CatspersCoffee/S100-Boards/PIC-SPI/S10_PIC_SPI_v1.sch

## KiCad design PIC-SPI/S10_PIC_SPI_v1.sch (2016-01-09, an earlier design)

Schematic: S10_PIC_SPI_v1.sch

Parts:
C1, C2, C5, C7, C11, C12: 10 uF
C3, C4, C6, C8, C14, C17, C20, C21, C25, C27, C28: 0.1 uF
C9: 22 uF
C10, C18: 15 pF
C15: 0.01 uF
C19, C26, C33, C34, C35, C36, C37, C38, C39, C40: C
D1, D4: LED
D2: P55
D3: P54
D5: POWER
D6: DONE
D7: BOARD_SELECT
D8: POWER CH341A
D9: FLASH_0
D10: FLASH_1
D11: FLASH_2
D12: FLASH_3
JP5: JUMPER; PIN_ARRAY_2X1
JPx1, JPx2, JPx3, JPx4, JPx5, JPx6, JPx7, JPx8: JUMPER; PIN_ARRAY_2X1
Jx2: USB_2
P1: M25P80 ISP
P2, P10: CONN_4
P3, P8, P9: CONN_2
P4: S100_MALE
P5: PIC_ISP
P6, P7: CONN_1
P19: XILINX CABLE2
Q1, Q2, Q9: ^^NPN-SOT23
R1, R5, R13, R14, R15, R16, R20, R21, R22, R23, R24, R29, R45: 330
R2, R18, R19, R28, R47: 470
R3: 1K
R4, R8, R10, R11, R30: 10k
R9, R12, R17: 10K
R25, R26, R27: 100
SW1, SW2: RESET
SW4: FLASH_SELECT
SW50: FLASH/RUN
U1: LDO_REG_7805
U2: LM1086CS
U3din1, U3dout1: ^^74HC541
U4, U5, U6, U19: ^^74LS541
U8: PIC18F1330
U12: ^^74LV244
U14, U15, U16, U17: M25P80
U18: CH341A
U20: XC95288XL-TQ144
Ux1: ^^3.3VREG_SOT223
X1: 12MHz

Connections:
0V: C1.2, C2.2, C3.2, C4.2, C5.2, C6.2, C7.2, C8.2, C9.2, C10.2, C11.2, C12.2, C14.2, C15.2, C17.2, C18.2, C19.2, C20.2, C21.2, C25.2, C26.2, C27.2, C28.2, C33.2, C34.2, C35.2, C36.2, C37.2, C38.2, C39.2, C40.2, D2.2 (K), D3.2 (K), D6.2 (K), D7.2 (K), Jx2.4, P1.1, P2.1, P3.2 (PM), P4.50 (0_V2), P4.100 (0_V5), P5.3, P10.1, Q1.2 (E), Q2.2 (E), Q9.2 (E), R5.2, R9.1, R10.1, R14.2, R21.1, R22.1, R23.1, R24.1, SW1.1, SW2.2, SW4.1, SW50.1, U1.2 (GND), U2.2 (GND), U4.1 (G1), U4.19 (G2), U5.1 (G1), U5.19 (G2), U6.1 (G1), U6.19 (G2), U8.5 (VSS/AVSS), U12.10 (GND), U14.4 (GND), U15.4 (GND), U16.4 (GND), U17.4 (GND), U18.12 (GND), U18.27 (WT#), U20.18 (GND), U20.29 (GND), U20.36 (GND), U20.47 (GND), U20.62 (GND), U20.72 (GND), U20.89 (GND), U20.90 (GND), U20.99 (GND), U20.108 (GND), U20.114 (GND), U20.123 (GND), U20.144 (GND), Ux1.1 (GND)
0V_A: P4.20 (0_V1)
0V_B: P4.53 (0_V3)
0V_C: P4.70 (0_V4)
25Pxx_CS: U12.5 (O2b), U12.14 (O2a), U20.124 (P124_FB10_MC10)
25Pxx_SEL_0: U14.1 (~CS), U20.125 (P125_FB10_MC11)
25Pxx_SEL_1: U15.1 (~CS), U20.126 (P126_FB10_MC12)
25Pxx_SEL_2: U16.1 (~CS), U20.128 (P128_FB10_MC14)
25Pxx_SEL_3: U17.1 (~CS), U20.129 (P129_FB10_MC17)
25Pxx_SEL_4: U20.56 (P56_FB9_MC11)
25Pxx_SEL_5: U20.57 (P57_FB9_MC12)
25Pxx_SEL_6: U20.58 (P58_FB9_MC14)
25Pxx_SEL_7: U20.59 (P59_FB9_MC17)
+8V: C1.1, C11.1, P4.1 (+8_V), P4.51 (+8_V), U1.1 (VI), U2.1 (VI)
+16V: P4.2 (+16_V)
-16V: P4.52 (-16_V)
/M1: U20.43 (P43_FB5_MC15)
/WAITtoS100: R47.1, U20.2 (P2_FB4_MC2_I/O/GTS3)
A0: P4.79 (A0), U4.2 (A0), U20.100 (P100_FB14_MC3)
A0b: U4.18 (Y0)
A1: P4.80 (A1), U4.3 (A1), U20.101 (P101_FB14_MC5)
A1b: U4.17 (Y1)
A2: P4.81 (A2), U4.4 (A2), U20.102 (P102_FB14_MC6)
A2b: U4.16 (Y2)
A3: P4.31 (A3), U4.5 (A3), U20.103 (P103_FB14_MC8)
A3b: U4.15 (Y3)
A4: P4.30 (A4), U4.6 (A4), U20.104 (P104_FB14_MC10)
A4b: U4.14 (Y4)
A5: P4.29 (A5), U4.7 (A5), U20.105 (P105_FB14_MC11)
A5b: U4.13 (Y5)
A6: P4.82 (A6), U4.8 (A6), U20.106 (P106_FB14_MC14)
A6b: U4.12 (Y6)
A7: P4.83 (A7), U4.9 (A7), U20.107 (P107_FB14_MC15)
A7b: U4.11 (Y7)
A8: P4.84 (A8), U5.2 (A0), U20.79 (P79_FB15_MC2)
A8b: U5.18 (Y0)
A9: P4.34 (A9), U5.3 (A1), U20.80 (P80_FB15_MC3)
A9b: U5.17 (Y1)
A10: P4.37 (A10), U5.4 (A2), U20.81 (P81_FB15_MC8)
A10b: U5.16 (Y2)
A11: P4.87 (A11), U5.5 (A3), U20.82 (P82_FB15_MC10)
A11b: U5.15 (Y3)
A12: P4.33 (A12), U5.6 (A4), U20.83 (P83_FB15_MC11)
A12b: U5.14 (Y4)
A13: P4.85 (A13), U5.7 (A5), U20.85 (P85_FB15_MC12)
A13b: U5.13 (Y5)
A14: P4.86 (A14), U5.8 (A6), U20.86 (P86_FB15_MC14)
A14b: U5.12 (Y6)
A15: P4.32 (A15), U5.9 (A7), U20.87 (P87_FB15_MC15)
A15b: U5.11 (Y7)
A16: P4.16 (A16), U6.2 (A0), U20.88 (P88_FB15_MC17)
A16b: U6.18 (Y0)
A17: P4.17 (A17), U6.3 (A1), U20.91 (P91_FB16_MC2)
A17b: U6.17 (Y1)
A18: P4.15 (A18), U6.4 (A2), U20.92 (P92_FB16_MC3)
A18b: U6.16 (Y2)
A19: P4.59 (A19), U6.5 (A3), U20.93 (P93_FB16_MC5)
A19b: U6.15 (Y3)
A20: P4.61 (A20), U6.6 (A4), U20.94 (P94_FB16_MC6)
A20b: U6.14 (Y4)
A21: P4.62 (A21), U6.7 (A5), U20.95 (P95_FB16_MC8)
A21b: U6.13 (Y5)
A22: P4.63 (A22), U6.8 (A6), U20.96 (P96_FB16_MC10)
A22b: U6.12 (Y6)
A23: P4.64 (A23), U6.9 (A7), U20.97 (P97_FB16_MC11)
A23b: U6.11 (Y7)
ADSB*: P4.22 (ADSB*)
BOARD_INTERRUPT_VECTc: JPx1.2, JPx2.2, JPx3.2, JPx4.2, JPx5.2, JPx6.2, JPx7.2, JPx8.2
BOARD_SEL_LED: R20.2, U20.31 (P31_FB3_MC12)
CDSB*: P4.19 (CDSB*)
CLOCK*: P4.49 (CLOCK)
CLOCK*b: U20.53 (P53_FB9_MC6)
CPLD2_TCK: R25.1, U20.67 (TCK)
CPLD2_TDI: R26.1, U20.63 (TDI)
CPLD2_TDO: P19.8, U20.122 (TDO)
CPLD2_TMS: R27.1, U20.65 (TMS)
CPLD_4: U20.4 (P4_FB4_MC6)
CPLD_5: U20.5 (P5_FB4_MC8_I/O/GTS1)
CPLD_45: U19.2 (A0), U20.45 (P45_FB7_MC3)
CPLD_46: U19.3 (A1), U20.46 (P46_FB7_MC5)
CPLD_48: U19.4 (A2), U20.48 (P48_FB7_MC12)
CPLD_49: U19.5 (A3), U20.49 (P49_FB7_MC15)
CPLD_130: U19.6 (A4), U20.130 (P130_FB8_MC2)
CPLD_131: U19.7 (A5), U20.131 (P131_FB8_MC3)
CPLD_132: U19.8 (A6), U20.132 (P132_FB8_MC5)
CPLD_133: U19.9 (A7), U20.133 (P133_FB8_MC8)
CPLD_134: U19.1 (G1), U19.19 (G2), U20.134 (P134_FB8_MC10)
CPLD_M25P80_CLK: U12.2 (I0a), U20.135 (P135_FB6_MC2)
CPLD_M25P80_CS: U12.6 (I2a), U20.137 (P137_FB6_MC5)
CPLD_M25P80_Din: U12.4 (I1a), U20.136 (P136_FB6_MC3)
CPLD_M25P80_Dout: R9.2, U12.12 (O3a), U20.138 (P138_FB6_MC6)
D0: U3din1.18 (Y0), U3dout1.2 (A0), U19.18 (Y0), U20.9 (P9_FB2_MC2)
D1: U3din1.17 (Y1), U3dout1.3 (A1), U19.17 (Y1), U20.10 (P3_FB2_MC3)
D2: U3din1.16 (Y2), U3dout1.4 (A2), U19.16 (Y2), U20.11 (P11_FB2_MC5)
D3: U3din1.15 (Y3), U3dout1.5 (A3), U19.15 (Y3), U20.12 (P12_FB2_MC6)
D4: U3din1.14 (Y4), U3dout1.6 (A4), U19.14 (Y4), U20.13 (P13_FB2_MC8)
D5: U3din1.13 (Y5), U3dout1.7 (A5), U19.13 (Y5), U20.14 (P14_FB2_MC10)
D6: U3din1.12 (Y6), U3dout1.8 (A6), U19.12 (Y6), U20.15 (P15_FB2_MC12)
D7: U3din1.11 (Y7), U3dout1.9 (A7), U19.11 (Y7), U20.16 (P16_FB2_MC14)
DBUSIN_EN: U3din1.1 (G1), U3din1.19 (G2), U20.22 (P22_FB1_MC8)
DBUSOUT_EN: U3dout1.1 (G1), U3dout1.19 (G2), U20.21 (P21_FB1_MC6)
DI0: P4.95 (DI1_OD1), U3dout1.18 (Y0)
DI1: P4.94 (DI1_OD1), U3dout1.17 (Y1)
DI2: P4.41 (D12_OD2), U3dout1.16 (Y2)
DI3: P4.42 (D13_OD3), U3dout1.15 (Y3)
DI4: P4.91 (DI4_OD4), U3dout1.14 (Y4)
DI5: P4.92 (DI5_OD5), U3dout1.13 (Y5)
DI6: P4.93 (DI6_OD6), U3dout1.12 (Y6)
DI7: P4.43 (D17_OD7), U3dout1.11 (Y7)
DO0: P4.36 (DO0_ED0), U3din1.2 (A0)
DO1: P4.35 (DO1_ED1), U3din1.3 (A1)
DO2: P4.88 (DO2_ED2), U3din1.4 (A2)
DO3: P4.89 (DO3_ED3), U3din1.5 (A3)
DO4: P4.38 (DO4_ED4), U3din1.6 (A4)
DO5: P4.39 (DO5_ED5), U3din1.7 (A5)
DO6: P4.40 (DO6_ED6), U3din1.8 (A6)
DO7: P4.90 (DO7_ED7), U3din1.9 (A7)
DODSB*: P4.23 (DODSB*)
ERROR*: P4.98 (ERROR*)
FLASH_0: D9.1 (A), U20.71 (P71_FB13_MC2)
FLASH_1: D10.1 (A), U20.74 (P74_FB13_MC8)
FLASH_2: D11.1 (A), U20.75 (P75_FB13_MC11)
FLASH_3: D12.1 (A), U20.76 (P76_FB13_MC14)
GND: P6.1, P7.1, P19.1, P19.3, P19.5, P19.7, P19.9
HOLD*: P4.74 (HOLD*)
INT*: P4.73 (INT*)
IOREQb: P4.69 (RFU3)
IOREQbb: U20.39 (P39_FB5_MC10)
LED_D2: R13.2, U20.7 (P7_FB4_MC14)
LED_D3: R16.2, U20.6 (P6_FB4_MC12_I/O/GTS2)
M2_MCLR: P5.1, R4.2, SW2.1, U8.4 (MCLR/VPP/RA5)
M2_PGC: P5.5, U8.12 (RB6/PWM4/PGC)
M2_PGD: P5.4, U8.13 (RB7/PWM5/PGD)
MWRT: P4.68 (MWRT)
MWRTb: U20.40 (P40_FB5_MC12)
NDEF1: P4.21 (NDEF1)
NDEF2: P4.65 (NDEF2)
NDEF2b: U20.41 (P41_FB5_MC14)
NDEF3: P4.66 (NDEF3)
NMI*: P4.12 (NMI*)
unnamed: C10.1, U18.13 (XI), X1.1
unnamed: C18.1, U18.14 (XO), X1.2
unnamed: D1.1 (A), R1.1
unnamed: D1.2 (K), Q1.3 (C)
unnamed: D2.1 (A), R13.1
unnamed: D3.1 (A), R16.1
unnamed: D4.1 (A), R29.1
unnamed: D4.2 (K), Q2.3 (C)
unnamed: D5.2 (K), R5.1
unnamed: D7.1 (A), R20.1
unnamed: D8.2 (K), R14.1
unnamed: D9.2 (K), R21.2
unnamed: D10.2 (K), R22.2
unnamed: D11.2 (K), R23.2
unnamed: D12.2 (K), R24.2
unnamed: JP5.1, R45.1
unnamed: Jx2.2, U18.11 (UD-)
unnamed: Jx2.3, U18.10 (UD+)
unnamed: P2.2, U20.116 (P116_FB12_MC12)
unnamed: P2.3, U20.115 (P115_FB12_MC10)
unnamed: P2.4, U20.113 (P113_FB12_MC8)
unnamed: P3.1, R15.1
unnamed: P10.2, U20.112 (P112_FB12_MC5)
unnamed: P10.3, U20.111 (P111_FB12_MC3)
unnamed: P10.4, U20.110 (P110_FB12_MC2)
unnamed: P19.4, R27.2
unnamed: P19.6, R25.2
unnamed: P19.10, R26.2
unnamed: Q1.1 (B), R2.1, R19.1
unnamed: Q2.1 (B), R18.1, R28.1
unnamed: Q9.1 (B), R47.2
unnamed: R3.1, U14.3 (~WP), U14.7 (~HOLD), U15.3 (~WP), U15.7 (~HOLD), U16.3 (~WP), U16.7 (~HOLD), U17.3 (~WP), U17.7 (~HOLD)
unnamed: R8.2, SW1.2, U20.24 (P24_FB1_MC12)
unnamed: R11.2, SW4.2, U8.18 (RB3/INT3)
unnamed: R12.2, U12.7 (O1b), U12.16 (O1a), U14.5 (Din), U15.5 (Din), U16.5 (Din), U17.5 (Din)
unnamed: R15.2, U18.1 (ACT#)
unnamed: R17.2, U12.9 (O0b), U12.18 (O0a), U14.6 (CLK), U15.6 (CLK), U16.6 (CLK), U17.6 (CLK)
unnamed: R30.2, SW50.2, U8.17 (RB2/INT2)
unnamed: U12.8 (I3a), U12.17 (I3b), U14.2 (Dout), U15.2 (Dout), U16.2 (Dout), U17.2 (Dout)
PHANTOM*: P4.67 (PHANTOM*)
PHI: P4.24 (PHI)
PHIb: U20.54 (P54_FB9_MC8)
PIC18F_0: U8.11 (RB5/PWM3)
PIC18F_1: U8.10 (RB4/PWM2)
PIC18F_2: U8.7 (RA3/RX/DT)
POC*: P4.99 (POC*)
PROG_M25P80_CLK: P1.2, U12.11 (I0b), U18.18 (D3)
PROG_M25P80_CS: P1.4, U12.15 (I2b), U18.15 (D0)
PROG_M25P80_Din: P1.3, U12.13 (I1b), U18.20 (D5)
PROG_M25P80_Dout: P1.5, R10.2, U12.3 (O3b), U18.22 (D7)
PWRFAIL*: P4.13 (PWRFAIL*)
Q1: R2.2, R18.2, U8.9 (RB1/PWM1), U12.19 (OEb)
Q2: R19.2, R28.2, U8.8 (RB0/PWM0), U12.1 (OEa)
RDY: JP5.2, P4.72 (RDY), Q9.3 (C)
RESET*: P4.75 (RESET*)
RESET*b: U20.3 (P3_FB4_MC5_I/O/GTS4)
RFU1: P4.27 (RFU_1)
RFU2: P4.28 (RFU_2)
RFU4: P4.71 (RFU4)
SDSB*: P4.18 (SDSB*)
SIXTN*: P4.60 (SIXTN*)
SLAVE_CLR*: P4.54 (SLAVE_CLR*)
SLAVE_CLR*vv: U20.33 (P33_FB3_MC15)
SPI_CLK: U20.139 (P139_FB6_MC8)
SPI_Din: U20.140 (P140_FB6_MC10)
SPI_Dout: U20.142 (P142_FB6_MC14)
SPI_SEL_0: U20.66 (P66_FB11_MC11)
SPI_SEL_1: U20.64 (P64_FB11_MC10)
SPI_SEL_2: U20.61 (P61_FB11_MC5)
SPI_SEL_3: U20.60 (P60_FB11_MC3)
TMA0*: P4.55 (TMA0*)
TMA0_CPLD: U20.117 (P117_FB10_MC2)
TMA1*: P4.56 (TMA1*)
TMA1_CPLD: U20.118 (P118_FB10_MC3)
TMA2*: P4.57 (TMA2*)
TMA2_CPLD: U20.119 (P119_FB10_MC5)
TMA3*: P4.14 (TMA3*)
TMA3_CPLD: U20.120 (P120_FB10_MC6)
USB_VCC1: C7.1, Jx2.1, Ux1.3 (VI)
V3.3: C2.1, C4.1, C5.1, C19.1, C26.1, C33.1, C34.1, C35.1, C36.1, C37.1, C38.1, C39.1, C40.1, P8.1, P8.2 (PM), P9.1, P9.2 (PM), P19.2, R3.2, R8.1, R12.1, R17.1, U2.3 (VO), U12.20 (VCC), U14.8 (VCC), U15.8 (VCC), U16.8 (VCC), U17.8 (VCC), U20.1 (VCCIO), U20.8 (VCCINT), U20.37 (VCCIO), U20.42 (VCCINT), U20.55 (VCCIO), U20.73 (VCCIO), U20.84 (VCCINT), U20.109 (VCCIO), U20.127 (VCCIO), U20.141 (VCCINT)
V3.3b: C9.1, C14.1, C15.1, D8.1 (A), U18.9 (V3), U18.28 (VCC), Ux1.2 (VOUT)
VCC: C3.1, C6.1, C8.1, C12.1, C17.1, C20.1, C21.1, C25.1, C27.1, C28.1, D5.1 (A), P5.2, R1.2, R4.1, R11.1, R29.2, R30.1, R45.2, U1.3 (VO), U8.14 (VDD/AVDD)
VI0*: JPx1.1, P4.4 (VIO*)
VI1*: JPx2.1, P4.5 (VI1*)
VI2*: JPx3.1, P4.6 (VI2*)
VI3*: JPx4.1, P4.7 (VI3*)
VI4*: JPx5.1, P4.8 (VI4*)
VI5*: JPx6.1, P4.9 (VI5*)
VI6*: JPx7.1, P4.10 (VI6*)
VI7*: JPx8.1, P4.11 (VI7*)
XRDY: P4.3 (XRDY)
Z80intVectorBusout: U20.44 (P44_FB5_MC17)
pDBIN: P4.78 (pDBIN)
pDBINb: U20.51 (P51_FB9_MC3)
pHLDA: P4.26 (pHDLA)
pSTVAL*: P4.25 (pSTVAL*)
pSYNC: P4.76 (pSYNC)
pWR*: P4.77 (pWR*)
pWR*b: U20.50 (P50_FB9_MC2)
sHLTA: P4.48 (sHLTA)
sINP: P4.46 (sINP)
sINPb: U20.35 (P35_FB5_MC5)
sINTA: P4.96 (sINTA)
sM1: P4.44 (sM1)
sMEMR: P4.47 (sMEMR)
sMEMRb: U20.38 (P38_FB5_MC8_I/O/GCK3)
sOUT: P4.45 (sOUT)
sOUTb: U20.34 (P34_FB5_MC2)
sWO*: P4.97 (sWO*)
sWO*b: U20.52 (P52_FB9_MC5)
sXTRQ*: P4.58 (sXTRQ*)

Notes on the sheet:
XILINX CABLE HEADER 1, 3, 5, 7, 9, 11, 13 - GND 2 - VREF +3.3V 4 - TMS 6 - TCK 8 - TDO 10 - TDI 12, 14 - NC
MOUNTING HOLES
Q1 out is HIGH on PowerUp
B -> A
Pin 49 (clock line from another board) Input
Pin 47 (MEM RD) Input
Pin 45 (I/O WR) Input
INPUT from S100 BUS
Pin 69 (I/O REQUEST) Input
Pin 46 (I/O RD) Input
Pin 68 (MEM WR) Input
Pin 65 (MEM REQUEST) Input
Pin 67 (/PHANTOM) Output
Pin 75 (master reset line) Input
Pin 76 (indicates beginning of machine cycle) Output
Pin 77 (active low when processor write to I/O or MEM) Input
Pin 78 (active high when processor reads I/O or MEM) Input
Pin 79 (Address line 0) S100 Bus
ADDRESS INPUTS from S100 BUS
Pin 44 (processor Instruction Fetch Cycle M1) Input
Pin 16 (Address line 16) S100 Bus
Pin 17 (Address line 17) S100 Bus
Pin 15 (Address line 18) S100 Bus
Pin 97 (active low when processor is in Write status) Input
Pin 26 (Processor in HOLD condition) Output
Pin 27 (Processor in WAIT condition) Output
Pin 24 (Primary Processor clock line ) Input
DATA I/O from/to S100 BUS
input to CPU from S100 bus (in terms of master) OUTPUT for this board
output to S100 Bus from CPU (in terms of master) INPUT for this board
from Pin xx of CPLD
Pin 59 (Address line 19) S100 Bus
/WAIT is output from slave to Processor
SPARE CPLD PINS
TO-220
~WR
~RD
~MREQ
~IORQ
DONE
RUN
PROGRAM
Data input to processorfrom 25Pxx via 74LV244 not able to Hi-Z so is separate Data line into CPLD
Data output (from proc) to 25P80
Q2 out is LOW on PowerUp
Pin 61 (Address line 20) S100 Bus
Pin 62 (Address line 21) S100 Bus
Pin 54 (reset from another board) Input
Pin 63 (Address line 22) S100 Bus
Pin 64 (Address line 23) S100 Bus
to BOARD_SELECT LED
to U35
to U36
to U37
Input - from U35
xxxx
to U42
to U44
to U13
to U15
to FPGA
to LED's
to U71 output /WAIT to S100 BUS
to LED D3
to LED D2
reset signal input from s100 bus
from U7
from U7b
SOT233
to U
FOR RUN/FLASH
WAIT to PIN 72 S100
Active Low This board data output, CPU data input
Pin 72 (controld run/WAIT state of processor) Input
SPARES
MCP_1
MCP_2
Pin96 Input
Buffered RESET* from S100 BUS
Active Low - sINTA*b
Active Low - pDBIN**b
ALL TMA lines are high when Z80 is Bus master
Active Low Address input with I/O req
Active Low - pDBIN*b
Active Low - pDBIN*b (READ STROBE)
Data input to processorfrom other SPI devices able to Hi-Z so is separate Data line into CPLD
CPLD output Data Bus
Q2 out is LOW on PowerUp - RUN
Q1 out is HIGH on PowerUp - PROG
Q1 out is HIGH on PowerUp - PROG so this LED will be on with Q1 high Q1 high = RUN Q1 low = PROG
Texas Instruments CD74HC154M96, Decoder, Demultiplexer, 1-of-16, Inverting, 2 → 6 V, 24-Pin SOIC RS Stock No. 662-7020
to U14
to U16
to U17
output from CPLD to 74LV244 then back to 25Pxx_CS
CS line for 25Pxx SPI: output from CPLD (pin 137) to 74LV244 then back to 25Pxx_CS (pin 124), internally with a 74138 the correct 25Pxx line is selected and routed to a single 25Pxx device (CPLD pins 125, 126, 128, 129)
Signals for other onboard SPI: on separate circuit
Active High (All TMA lines High)
Active High (SINTA and Read)
Active High (SINTA and Read and All TMA Lines high (Z80))
