CatspersCoffee/S100-Boards/Z80-FPGA-SBC/SBC.sch

## KiCad design Z80-FPGA-SBC/SBC.sch (2013-09-12, an earlier design)

Schematic: SBC.sch

Parts:
C1, C5, C9, C10, C12, C14, C15, C16, C17, C18, C23, C30, C41, C42, C43, C44, C45, C46, C47, C48, C49, C50, C51, C52, C54, C55, C56, C57, C60: 0.1 uF
C2, C3, C24, C25, C26, C27, C28, C29, C32: 10 uF
C4, C6, C7, C8, C11, C13, C19, C20: 0.1 uF; C2
C31: 22 uF
C58, C59, C61, C62, C65, C66, C67, C68, C69, C70: C
D2: DIODE
D3, D4, D5, D6, D8, D9, D10: LED
J1: USB_2
JP1, JP2, JP3, JP4: JUMPER; PIN_ARRAY_2X1
K1, K6, K8, K9, K12: CONN_3
P1: PARALLEL
P2: CLK_CPU
P4: XILINX CABLE
P5: CLK_UART
P6: RESET
P7: CPLD_JTAG
P8: PF_JTAG
P9: S6_JTAG
P10: PROG_B
P14: CONN_6
P17, P18: CONN_1
P21: S100_MALE
Q1: ^^NPN-BC817-SOT323
R1: 10
R2: 10K
R3, R25, R26, R27, R29, R35, R41, R42, R43: 330
R4, R33: 1K
R9: 10K; Digikey ??
R12: 4700
R21, R23: 10k
R22, R24: 0
R30, R31, R32: 100
R34, R36: 4K7
SW1: SW_PUSH
SW3: PROG_B
U1: 16550
U2, U16: 27C080
U3: 23LC1024
U4: PAC_GHOST
U6, U17: POWER_SELECT
U7: 74LS14
U9: LDO_REG_7805
U10: LM1086CS
U11: LF25CDT
U12: LD1117DT12
U13, U14, U15, U35, U36, U37, U42, U44, U50, U51, U52, U54, U55: 74LS245
U19: 8255
U22, U46, U47, U48, U49: 74LS541
U24: Z80-CPU
U25, U27: IS61LV5128AL-SOJ32
U26: 74LS06N; 74xx-eu-DIL14
U28: FT232R
U30: XC6SLX9-TQ144
U31: CLK_FPGA1; Digikey CTX285LVCT-ND
U32: XC95288XL-TQ144
U33: XCF02S
U43, U53: 74LVC245

Connections:
0V_A: JP1.2, P21.20 (0_V1)
0V_B: JP2.2, P21.53 (0_V3)
0V_C: JP3.2, P21.70 (0_V4)
25LC_CS: P14.1, R9.1, U3.1 (CS), U30.43 (IO_L62N_D6_2)
25LC_S0: P14.4, U3.2 (SO), U30.44 (IO_L62P_D5_2)
25LC_SCK: P14.5, U3.5 (SI), U30.40 (IO_L64N_D9_2)
25LC_SI: P14.6, U3.6 (SCK), U30.41 (IO_L64P_D8_2)
+8V: C3.1, C24.1, C27.1, C28.1, P21.1 (+8_V), P21.51 (+8_V), U9.1 (VI), U10.1 (VI), U11.1 (VI), U12.3 (VI)
+16V: P21.2 (+16_V), U6.2 (IN2)
-16V: P21.52 (-16_V), U17.2 (IN2)
/BUSAK: U24.23 (BUSAK), U32.4 (P4_FB4_MC6), U50.7 (A5), U55.9 (A7)
/BUSRQ: U24.25 (BUSRQ), U43.14 (B4), U50.6 (A4)
/CS_CFG: U35.9 (A7)
/CS_PPI: U19.6 (CS), U35.6 (A4)
/CS_RAM: R22.1, U35.2 (A0)
/CS_ROM: U2.22 (CE), U35.3 (A1)
/CS_ROM_1: U16.22 (CE), U35.4 (A2)
/CS_ROM_2: R24.1, U35.5 (A3)
/CS_RTC: U35.8 (A6)
/CS_UART: U1.14 (CS2), U35.7 (A5)
/HALT: U24.18 (HALT), U32.3 (P3_FB4_MC5_I/O/GTS4), U55.8 (A6)
/INT: U24.16 (INT), U26.2, U43.17 (B1), U50.3 (A1)
/IORQ: U24.20 (IORQ), U32.31 (P31_FB3_MC12), U55.4 (A2)
/M1: U24.27 (M1), U32.28 (P28_FB3_MC2), U55.2 (A0)
/MREQ: U24.19 (MREQ), U32.30 (P30_FB3_MC10_I/O/GCK1), U55.3 (A1)
/NMI: U24.17 (NMI), U43.16 (B2), U50.4 (A2)
/RD: U1.21 (DISTR), U2.24 (OE), U16.24 (OE), U19.5 (RD), U24.21 (RD), U25.24 (OE), U27.24 (OE), U32.32 (P32_FB3_MC14_I/O/GCK2), U55.5 (A3)
/RESET: U7.4, U24.26 (RESET), U32.131 (P131_FB8_MC3), U43.15 (B3), U50.5 (A3)
/RFSH: U24.28 (REFSH), U32.2 (P2_FB4_MC2_I/O/GTS3), U55.7 (A5)
/WAIT: U24.24 (WAIT), U43.18 (B0), U50.2 (A0)
/WR: K6.3, U1.18 (/DOSTR), U19.36 (WR), U24.22 (WR), U25.29 (WE), U27.29 (WE), U32.33 (P33_FB3_MC15), U55.6 (A4)
A0: U1.28 (A0), U2.12 (A0), U16.12 (A0), U19.9 (A0), U24.30 (A0), U25.12 (A0), U27.12 (A0), U32.100 (P100_FB14_MC3), U46.2 (A0), U51.2 (A0)
A0b: P21.79 (A0), U46.18 (Y0)
A1: U1.27 (A1), U2.11 (A1), U16.11 (A1), U19.8 (A1), U24.31 (A1), U25.11 (A1), U27.11 (A1), U32.101 (P101_FB14_MC5), U46.3 (A1), U51.3 (A1)
A1b: P21.80 (A1), U46.17 (Y1)
A2: U1.26 (A2), U2.10 (A2), U16.10 (A2), U24.32 (A2), U25.10 (A2), U27.10 (A2), U32.102 (P102_FB14_MC6), U46.4 (A2), U51.4 (A2)
A2b: P21.81 (A2), U46.16 (Y2)
A3: U2.9 (A3), U16.9 (A3), U24.33 (A3), U25.9 (A3), U27.9 (A3), U32.103 (P103_FB14_MC8), U46.5 (A3), U51.5 (A3)
A3b: P21.31 (A3), U46.15 (Y3)
A4: U2.8 (A4), U16.8 (A4), U24.34 (A4), U25.8 (A4), U27.8 (A4), U32.104 (P104_FB14_MC10), U46.6 (A4), U51.6 (A4)
A4b: P21.30 (A4), U46.14 (Y4)
A5: U2.7 (A5), U16.7 (A5), U24.35 (A5), U25.7 (A5), U27.7 (A5), U32.105 (P105_FB14_MC11), U46.7 (A5), U51.7 (A5)
A5b: P21.29 (A5), U46.13 (Y5)
A6: U2.6 (A6), U16.6 (A6), U24.36 (A6), U25.6 (A6), U27.6 (A6), U32.106 (P106_FB14_MC14), U46.8 (A6), U51.8 (A6)
A6b: P21.82 (A6), U46.12 (Y6)
A7: U2.5 (A7), U16.5 (A7), U24.37 (A7), U25.5 (A7), U27.5 (A7), U32.107 (P107_FB14_MC15), U46.9 (A7), U51.9 (A7)
A7b: P21.83 (A7), U46.11 (Y7)
A8: U2.27 (A8), U16.27 (A8), U24.38 (A8), U25.27 (A8), U27.27 (A8), U32.79 (P79_FB15_MC2), U47.2 (A0), U52.2 (A0)
A8b: P21.84 (A8), U47.18 (Y0)
A9: U2.26 (A9), U16.26 (A9), U24.39 (A9), U25.26 (A9), U27.26 (A9), U32.80 (P80_FB15_MC3), U47.3 (A1), U52.3 (A1)
A9b: P21.34 (A9), U47.17 (Y1)
A10: U2.23 (A10), U16.23 (A10), U24.40 (A10), U25.23 (A10), U27.23 (A10), U32.81 (P81_FB15_MC8), U47.4 (A2), U52.4 (A2)
A10b: P21.37 (A10), U47.16 (Y2)
A11: U2.25 (A11), U16.25 (A11), U24.1 (A11), U25.25 (A11), U27.25 (A11), U32.82 (P82_FB15_MC10), U47.5 (A3), U52.5 (A3)
A11b: P21.87 (A11), U47.15 (Y3)
A12: U2.4 (A12), U16.4 (A12), U24.2 (A12), U25.4 (A12), U27.4 (A12), U32.83 (P83_FB15_MC11), U47.6 (A4), U52.6 (A4)
A12b: P21.33 (A12), U47.14 (Y4)
A13: U2.28 (A13), U16.28 (A13), U24.3 (A13), U25.28 (A13), U27.28 (A13), U32.85 (P85_FB15_MC12), U47.7 (A5), U52.7 (A5)
A13b: P21.85 (A13), U47.13 (Y5)
A14: U2.29 (A14), U16.29 (A14), U24.4 (A14), U25.3 (A14), U27.3 (A14), U32.86 (P86_FB15_MC14), U47.8 (A6), U52.8 (A6)
A14b: P21.86 (A14), U47.12 (Y6)
A15: U24.5 (A15), U32.87 (P87_FB15_MC15), U47.9 (A7), U52.9 (A7)
A15_RAM: U25.31 (A15), U36.7 (A5)
A15_RAM_3: U27.31 (A15), U37.3 (A1)
A15_ROM: U2.3 (A15), U16.3 (A15), U36.2 (A0)
A15b: P21.32 (A15), U47.11 (Y7)
A16_RAM: U25.2 (A16), U36.8 (A6), U48.2 (A0)
A16_RAM_3: U27.2 (A16), U37.4 (A2)
A16_ROM: U2.2 (A16), U16.2 (A16), U36.3 (A1)
A16b: P21.16 (A16), U48.18 (Y0)
A17_RAM: U25.1 (A17), U36.9 (A7), U48.3 (A1)
A17_RAM_3: U27.1 (A17), U37.5 (A3)
A17_ROM: K1.1, U36.4 (A2)
A17b: P21.17 (A17), U48.17 (Y1)
A18_RAM: U25.30 (A18), U37.2 (A0), U48.4 (A2)
A18_RAM_3: U27.30 (A18), U37.6 (A4)
A18_ROM: K6.1, K8.3, U36.5 (A3)
A18b: P21.15 (A18), U48.16 (Y2)
A19_ROM: K8.1, U36.6 (A4)
ADSB*: P21.22 (ADSB*)
B_/INT: K12.1, U26.13
CDSB*: P21.19 (CDSB*)
CLK_CPU: P2.8, U13.11 (B7), U24.6 (CLK), U43.11 (B7)
CLK_CPU2: U15.8 (A6)
CLK_UART: P5.5, U1.16 (XTAL1(I))
CLOCK2: P21.59 (A19), U15.12 (B6)
CLOCK*: P21.49 (CLOCK), U13.9 (A7)
CPLD1_TDI: P7.3, U32.63 (TDI)
CPLD1_TDO: P7.1, U32.122 (TDO)
CPLD_20: U14.9 (A7), U32.20 (P20_FB1_MC5)
CPLD_21: U14.8 (A6), U32.21 (P21_FB1_MC6)
CPLD_22: U14.7 (A5), U32.22 (P22_FB1_MC8)
CPLD_23: U14.6 (A4), U32.23 (P23_FB1_MC10)
CPLD_24: U14.5 (A3), U32.24 (P24_FB1_MC12)
CPLD_25: U14.4 (A2), U32.25 (P25_FB1_MC14)
CPLD_26: U14.3 (A1), U32.26 (P26_FB1_MC15)
CPLD_27: U14.2 (A0), U32.27 (P27_FB1_MC17)
CPLD_39: U32.39 (P39_FB5_MC10), U42.18 (B0)
CPLD_40: U32.40 (P40_FB5_MC12), U42.17 (B1)
CPLD_41: U32.41 (P41_FB5_MC14), U42.16 (B2)
CPLD_43: U32.43 (P43_FB5_MC15), U42.15 (B3)
CPLD_44: U32.44 (P44_FB5_MC17), U42.14 (B4)
CPLD_45: U32.45 (P45_FB7_MC3), U42.13 (B5)
CPLD_46: U32.46 (P46_FB7_MC5), U42.12 (B6)
CPLD_48: U32.48 (P48_FB7_MC12), U42.11 (B7)
CPLD_49: U32.49 (P49_FB7_MC15)
CPLD_50: U32.50 (P50_FB9_MC2)
CPLD_51: U15.6 (A4), U32.51 (P51_FB9_MC3)
CPLD_52: U15.5 (A3), U32.52 (P52_FB9_MC5)
CPLD_53: U15.4 (A2), U32.53 (P53_FB9_MC6)
CPLD_54: U15.3 (A1), U32.54 (P54_FB9_MC8)
CPLD_56: U15.2 (A0), U32.56 (P56_FB9_MC11)
CPLD_57: U13.17 (B1), U32.57 (P57_FB9_MC12)
CPLD_58: U13.18 (B0), U32.58 (P58_FB9_MC14)
CPLD_59: U32.59 (P59_FB9_MC17)
CPLD_60: U32.60 (P60_FB11_MC3), U36.14 (B4)
CPLD_61: U32.61 (P61_FB11_MC5), U36.15 (B3)
CPLD_64: U32.64 (P64_FB11_MC10), U36.16 (B2)
CPLD_66: U32.66 (P66_FB11_MC11), U36.17 (B1)
CPLD_68: U32.68 (P68_FB11_MC12), U36.18 (B0)
CPLD_69: U32.69 (P69_FB11_MC14), U35.11 (B7)
CPLD_70: U32.70 (P70_FB11_MC17), U35.12 (B6)
CPLD_71: R41.1, U32.71 (P71_FB13_MC2)
CPLD_74: R42.1, U32.74 (P74_FB13_MC8)
CPLD_75: R43.1, U32.75 (P75_FB13_MC11)
CPLD_76: U32.76 (P76_FB13_MC14), U37.11 (B7)
CPLD_77: U32.77 (P77_FB13_MC15), U37.12 (B6)
CPLD_78: U32.78 (P78_FB13_MC17), U37.13 (B5)
CPLD_91: U32.91 (P91_FB16_MC2), U36.13 (B5)
CPLD_92: U32.92 (P92_FB16_MC3), U36.12 (B6)
CPLD_93: U32.93 (P93_FB16_MC5), U36.11 (B7)
CPLD_94: U32.94 (P94_FB16_MC6), U37.18 (B0)
CPLD_95: U32.95 (P95_FB16_MC8), U37.17 (B1)
CPLD_96: U32.96 (P96_FB16_MC10), U37.16 (B2)
CPLD_97: U32.97 (P97_FB16_MC11), U37.15 (B3)
CPLD_98: U32.98 (P98_FB16_MC12), U37.14 (B4)
CPLD_110: U32.110 (P110_FB12_MC2), U35.13 (B5)
CPLD_111: U32.111 (P111_FB12_MC3), U35.14 (B4)
CPLD_112: U32.112 (P112_FB12_MC5), U35.15 (B3)
CPLD_113: U32.113 (P113_FB12_MC8), U35.16 (B2)
CPLD_115: U32.115 (P115_FB12_MC10), U35.17 (B1)
CPLD_116: U32.116 (P116_FB12_MC12), U35.18 (B0)
CPLD_117: U32.117 (P117_FB10_MC2), U44.12 (B6)
CPLD_118: U32.118 (P118_FB10_MC3), U44.13 (B5)
CPLD_119: U32.119 (P119_FB10_MC5), U44.14 (B4)
CPLD_120: U32.120 (P120_FB10_MC6), U44.15 (B3)
CPLD_121: U32.121 (P121_FB10_MC8), U44.16 (B2)
CPLD_124: U32.124 (P124_FB10_MC10), U44.17 (B1)
CPLD_125: U32.125 (P125_FB10_MC11), U44.18 (B0)
CPLD_126: U32.126 (P126_FB10_MC12)
CPLD_128: U32.128 (P128_FB10_MC14)
CPLD_129: U32.129 (P129_FB10_MC17)
CPLD_130: U32.130 (P130_FB8_MC2)
CTS_TTL: U1.36 (CTS), U28.11 (CTS#)
D0: U1.1 (D0), U2.13 (D0), U16.13 (D0), U19.34 (D0), U22.18 (Y0), U24.14 (D0), U25.13 (I/O_0), U27.13 (I/O_0), U32.9 (P9_FB2_MC2), U32.17 (P17_FB2_MC15), U49.2 (A0), U53.18 (B0), U54.2 (A0)
D1: U1.2 (D1), U2.14 (D1), U16.14 (D1), U19.33 (D1), U22.17 (Y1), U24.15 (D1), U25.14 (I/O_1), U27.14 (I/O_1), U32.10 (P3_FB2_MC3), U32.19 (P19_FB2_MC17), U49.3 (A1), U53.17 (B1), U54.3 (A1)
D2: U1.3 (D2), U2.15 (D2), U16.15 (D2), U19.32 (D2), U22.16 (Y2), U24.12 (D2), U25.15 (I/O_2), U27.15 (I/O_2), U32.11 (P11_FB2_MC5), U49.4 (A2), U53.16 (B2), U54.4 (A2)
D3: U1.4 (D3), U2.17 (D3), U16.17 (D3), U19.31 (D3), U22.15 (Y3), U24.8 (D3), U25.17 (I/O_3), U27.17 (I/O_3), U32.12 (P12_FB2_MC6), U49.5 (A3), U53.15 (B3), U54.5 (A3)
D4: U1.5 (D4), U2.18 (D4), U16.18 (D4), U19.30 (D4), U22.14 (Y4), U24.7 (D4), U25.18 (I/O_4), U27.18 (I/O_4), U32.13 (P13_FB2_MC8), U49.6 (A4), U53.14 (B4), U54.6 (A4)
D5: U1.6 (D5), U2.19 (D5), U16.19 (D5), U19.29 (D5), U22.13 (Y5), U24.9 (D5), U25.19 (I/O_5), U27.19 (I/O_5), U32.14 (P14_FB2_MC10), U49.7 (A5), U53.13 (B5), U54.7 (A5)
D6: U1.7 (D6), U2.20 (D6), U16.20 (D6), U19.28 (D6), U22.12 (Y6), U24.10 (D6), U25.20 (I/O_6), U27.20 (I/O_6), U32.15 (P15_FB2_MC12), U49.8 (A6), U53.12 (B6), U54.8 (A6)
D7: U1.8 (D7), U2.21 (D7), U16.21 (D7), U19.27 (D7), U22.11 (Y7), U24.13 (D7), U25.21 (I/O_7), U27.21 (I/O_7), U32.16 (P16_FB2_MC14), U49.9 (A7), U53.11 (B7), U54.9 (A7)
DBUSIN_EN: U22.1 (G1), U22.19 (G2), U32.132 (P132_FB8_MC5)
DBUSOUT_EN: U32.133 (P133_FB8_MC8), U49.1 (G1), U49.19 (G2)
DI0b: P21.95 (DI1_OD1), U49.18 (Y0)
DI1b: P21.94 (DI1_OD1), U49.17 (Y1)
DI2b: P21.41 (D12_OD2), U49.16 (Y2)
DI3b: P21.42 (D13_OD3), U49.15 (Y3)
DI4b: P21.91 (DI4_OD4), U49.14 (Y4)
DI5b: P21.92 (DI5_OD5), U49.13 (Y5)
DI6b: P21.93 (DI6_OD6), U49.12 (Y6)
DI7b: P21.43 (D17_OD7), U49.11 (Y7)
DO0b: P21.36 (DO0_ED0), U22.2 (A0)
DO1b: P21.35 (DO1_ED1), U22.3 (A1)
DO2b: P21.88 (DO2_ED2), U22.4 (A2)
DO3b: P21.89 (DO3_ED3), U22.5 (A3)
DO4b: P21.38 (DO4_ED4), U22.6 (A4)
DO5b: P21.39 (DO5_ED5), U22.7 (A5)
DO6b: P21.40 (DO6_ED6), U22.8 (A6)
DO7b: P21.90 (DO7_ED7), U22.9 (A7)
DODSB*: P21.23 (DODSB*)
DSR_TTL: U1.37 (DSR), U28.9 (DSR#)
DTR_TTL: U1.33 (DTR), U28.2 (DTR#)
ERROR*: P21.98 (ERROR*)
FPGA_2: U30.2 (IO_L83P_3)
FPGA_5: U30.5 (IO_L52N_3)
FPGA_6: U30.6 (IO_L52P_3)
FPGA_7: U30.7 (IO_L51N_3)
FPGA_8: U30.8 (IO_L51P_3)
FPGA_9: U30.9 (IO_L50N_3)
FPGA_10: U30.10 (IO_L50P_3)
FPGA_11: U30.11 (IO_L49N_3)
FPGA_12: U30.12 (IO_L49P_3)
FPGA_14: U30.14 (IO_L44N_GCLK20_3)
FPGA_15: U30.15 (IO_L44P_GCLK21_3)
FPGA_16: U30.16 (IO_L43N_GCLK22_IRDY2_3)
FPGA_17: U30.17 (IO_L43P_GCLK23_3)
FPGA_21: U30.21 (IO_L42N_GCLK24_3)
FPGA_22: U30.22 (IO_L42P_GCLK25_TRDY2_3)
FPGA_23: U30.23 (IO_L41N_GCLK26_3)
FPGA_24: U30.24 (IO_L41P_GCLK27_3)
FPGA_26: U30.26 (IO_L37N_3), U32.143 (P143_FB6_MC15_I/O/GSR)
FPGA_27: U30.27 (IO_L37P_3), U32.142 (P142_FB6_MC14)
FPGA_29: U30.29 (IO_L36N_3), U32.140 (P140_FB6_MC10)
FPGA_30: U30.30 (IO_L36P_3), U32.139 (P139_FB6_MC8)
FPGA_32: U30.32 (IO_L2N_3), U32.138 (P138_FB6_MC6)
FPGA_33: U30.33 (IO_L2P_3), U32.137 (P137_FB6_MC5)
FPGA_34: U30.34 (IO_L1N_VREF_3), U32.136 (P136_FB6_MC3)
FPGA_35: U30.35 (IO_L1P_3), U32.135 (P135_FB6_MC2)
FPGA_45: U30.45 (IO_L49N_D4_2)
FPGA_46: U30.46 (IO_L49P_D3_2)
FPGA_48: U30.48 (IO_L48P_D7_2)
FPGA_55: U30.55 (IO_L30N_GCLK0_USERCCLK_2)
FPGA_56: U30.56 (IO_L30P_GCLK1_D13_2)
FPGA_57: U30.57 (IO_L14N_D12_2)
FPGA_58: U30.58 (IO_L14P_D11_2)
FPGA_59: U30.59 (IO_L13N_D10_2)
FPGA_84: U30.84 (IO_L43N_GCLK4_1), U43.8 (A6)
FPGA_87: U30.87 (IO_L42N_GCLK6_TRDY1_1), U43.7 (A5)
FPGA_88: U30.88 (IO_L42P_GCLK7_1), U43.6 (A4)
FPGA_92: U30.92 (IO_L41N_GCLK8_1), U43.5 (A3)
FPGA_93: U30.93 (IO_L41P_GCLK9_IRDY1_1), U43.4 (A2)
FPGA_94: U30.94 (IO_L40N_GCLK10_1), U43.3 (A1)
FPGA_95: U30.95 (IO_L40P_GCLK11_1), U43.2 (A0)
FPGA_97: U30.97 (IO_L34N_1), U55.11 (B7)
FPGA_98: U30.98 (IO_L34P_1), U55.12 (B6)
FPGA_99: U30.99 (IO_L33N_1), U55.13 (B5)
FPGA_100: U30.100 (IO_L33P_1), U55.14 (B4)
FPGA_101: U30.101 (IO_L32N_1), U55.15 (B3)
FPGA_102: U30.102 (IO_L32P_1), U55.16 (B2)
FPGA_104: U30.104 (IO_L1N_VREF_1), U55.17 (B1)
FPGA_105: U30.105 (IO_L1P_1), U55.18 (B0)
FPGA_111: U30.111 (IO_L66N_SCP0_0), U53.9 (A7), U54.11 (B7)
FPGA_112: U30.112 (IO_L66P_SCP1_0), U53.8 (A6), U54.12 (B6)
FPGA_114: U30.114 (IO_L65N_SCP2_0), U53.7 (A5), U54.13 (B5)
FPGA_115: U30.115 (IO_L65P_SCP3_0), U53.6 (A4), U54.14 (B4)
FPGA_116: U30.116 (IO_L64N_SCP4_0), U53.5 (A3), U54.15 (B3)
FPGA_117: U30.117 (IO_L64P_SCP5_0), U53.4 (A2), U54.16 (B2)
FPGA_118: U30.118 (IO_L63N_SCP6_0), U53.3 (A1), U54.17 (B1)
FPGA_119: U30.119 (IO_L63P_SCP7_0), U53.2 (A0), U54.18 (B0)
FPGA_120: U30.120 (IO_L62N_VREF_0), U52.11 (B7)
FPGA_121: U30.121 (IO_L62P_0), U52.12 (B6)
FPGA_123: U30.123 (IO_L37N_GCLK12_0), U52.13 (B5)
FPGA_124: U30.124 (IO_L37P_GCLK13_0), U52.14 (B4)
FPGA_126: U30.126 (IO_L36N_GCLK14_0), U52.15 (B3)
FPGA_127: U30.127 (IO_L36P_GCLK15_0), U52.16 (B2)
FPGA_131: U30.131 (IO_L35N_GCLK16_0), U52.17 (B1)
FPGA_132: U30.132 (IO_L35P_GCLK17_0), U52.18 (B0)
FPGA_133: U30.133 (IO_L34N_GCLK18_0), U51.11 (B7)
FPGA_134: U30.134 (IO_L34P_GCLK19_0), U51.12 (B6)
FPGA_137: U30.137 (IO_L4N_0), U51.13 (B5)
FPGA_138: U30.138 (IO_L4P_0), U51.14 (B4)
FPGA_139: U30.139 (IO_L3N_0), U51.15 (B3)
FPGA_140: U30.140 (IO_L3P_0), U51.16 (B2)
FPGA_141: U30.141 (IO_L2N_0), U51.17 (B1)
FPGA_142: U30.142 (IO_L2P_0), U51.18 (B0)
FPGA_CLK_0: U30.51 (IO_L31P_GCLK31_D14_2), U31.3 (OUT)
FPGA_CLK_2: U30.50 (IO_L31N_GCLK30_D15_2), U43.9 (A7)
GND: C1.2, C2.2, C3.2, C4.2, C5.2, C6.2, C7.2, C8.2, C9.2, C10.2, C11.2, C12.2, C13.2, C14.2, C15.2, C16.2, C17.2, C18.2, C19.2, C20.2, C23.2, C24.2, C25.2, C26.2, C27.2, C28.2, C29.2, C30.2, C31.2, C32.2, C41.2, C42.2, C43.2, C44.2, C45.2, C46.2, C47.2, C48.2, C49.2, C50.2, C51.2, C52.2, C54.2, C55.2, C56.2, C57.2, C58.2, C59.2, C60.2, C61.2, C62.2, C65.2, C66.2, C67.2, C68.2, C69.2, C70.2, D3.2 (K), D8.2 (K), D9.2 (K), D10.2 (K), J1.4, JP1.1, JP2.1, JP3.1, JP4.2, K9.1, P1.26 (P22), P2.7, P4.1, P4.3, P4.5, P4.7, P4.9, P5.4, P6.1, P10.2 (PM), P14.3, P17.1, P18.1, P21.50 (0_V2), P21.100 (0_V5), Q1.2 (E), SW1.1, SW3.1, U1.19 (DOSTR), U1.22 (/DISTR), U1.25 (ADS), U3.4 (VSS), U9.2 (GND), U10.2 (GND), U11.2 (GND), U12.1 (GND), U24.29 (VSS), U25.16 (GND), U27.16 (GND), U28.7 (GND), U28.18 (GND), U28.21 (GND), U28.25 (AGND), U28.26 (TEST), U30.3 (GND), U30.13 (GND), U30.25 (GND), U30.49 (GND), U30.54 (GND), U30.60 (IO_L13P_M1_2), U30.68 (GND), U30.73 (SUSPEND), U30.77 (GND), U30.91 (GND), U30.96 (GND), U30.108 (GND), U30.113 (GND), U30.130 (GND), U30.136 (GND), U31.2 (GND), U32.18 (GND), U32.29 (GND), U32.36 (GND), U32.47 (GND), U32.62 (GND), U32.72 (GND), U32.89 (GND), U32.90 (GND), U32.99 (GND), U32.108 (GND), U32.114 (GND), U32.123 (GND), U32.144 (GND), U33.11 (GND), U35.1 (A->B), U35.19 (CE), U36.1 (A->B), U36.19 (CE), U37.1 (A->B), U37.19 (CE), U43.1 (DIR), U43.10 (GND), U50.1 (A->B), U50.19 (CE), U53.10 (GND)
HOLD*: P21.74 (HOLD*), U15.16 (B2)
INT: U1.30 (IRQ), U26.3
INT*: P21.73 (INT*), U15.17 (B1)
IOREQ: U32.134 (P134_FB8_MC10), U48.9 (A7)
IOREQb: P21.63 (A22), U42.6 (A4), U48.11 (Y7)
MWRT: P21.68 (MWRT), U42.7 (A5), U44.3 (A1)
NC_A23: K12.3, R12.2
NDEF1: P21.21 (NDEF1), U15.14 (B4)
NDEF2: P21.65 (NDEF2), U42.8 (A6)
NDEF3: P21.66 (NDEF3), U42.9 (A7)
NMI*: P21.12 (NMI*), U14.18 (B0)
unnamed: C2.1, D2.1 (A), R1.1, R2.2, U7.1
unnamed: D3.1 (A), R3.2
unnamed: D4.1 (A), R25.2
unnamed: D4.2 (K), U28.23 (CBUS0)
unnamed: D5.1 (A), R26.2
unnamed: D5.2 (K), U28.22 (CBUS1)
unnamed: D6.1 (A), R27.2
unnamed: D6.2 (K), Q1.3 (C)
unnamed: D8.1 (A), R41.2
unnamed: D9.1 (A), R42.2
unnamed: D10.1 (A), R43.2
unnamed: J1.2, U28.16 (USBDM_D-)
unnamed: J1.3, U28.15 (USBDP_D+)
unnamed: K1.2 (PM), U2.30 (A17), U16.30 (A17)
unnamed: K6.2 (PM), U2.31 (A18), U16.31 (A18)
unnamed: K8.2 (PM), U2.1 (A19), U16.1 (A19)
unnamed: K12.2 (PM), U26.4
unnamed: P4.4, R32.2
unnamed: P4.6, R30.2
unnamed: P4.8, P7.2
unnamed: P4.10, R31.2
unnamed: P6.2 (PM), R1.2, SW1.2
unnamed: P7.4, P8.2
unnamed: P8.4, P9.2
unnamed: P9.4, R31.1
unnamed: P10.1, R34.2, SW3.2, U30.37 (PROGRAM_B_2), U33.7 (CF)
unnamed: Q1.1 (B), R29.1
unnamed: R21.2, R22.2, U25.22 (CE)
unnamed: R23.2, R24.2, U27.22 (CE)
unnamed: R29.2, R35.2, U30.71 (DONE_2), U33.10 (CE)
unnamed: R33.1, U31.1 (OE/StandBy)
unnamed: R36.2, U30.39 (IO_L65P_INIT_B_2), U33.8 (OE/RST)
unnamed: U1.9 (RCLK), U1.15 (BAUDOUT)
unnamed: U6.1 (IN1), U9.3 (VO)
unnamed: U10.3 (VO), U17.1 (IN1)
unnamed: U26.1, U26.12
unnamed: U30.65 (IO_L3P_D0_DIN_MISO_MISO1_2), U33.1 (DATA_(D0))
unnamed: U30.70 (IO_L1P_CCLK_2), U33.3 (CLK)
unnamed: U32.5 (P5_FB4_MC8_I/O/GTS1), U50.18 (B0)
unnamed: U32.6 (P6_FB4_MC12_I/O/GTS2), U50.17 (B1)
unnamed: U32.7 (P7_FB4_MC14), U50.16 (B2)
unnamed: U32.34 (P34_FB5_MC2), U50.15 (B3)
unnamed: U32.35 (P35_FB5_MC5), U50.14 (B4)
unnamed: U32.38 (P38_FB5_MC8_I/O/GCK3), U50.13 (B5)
PA0: P1.2, U19.4 (PA0)
PA1: P1.4, U19.3 (PA1)
PA2: P1.6, U19.2 (PA2)
PA3: P1.8, U19.1 (PA3)
PA4: P1.10, U19.40 (PA4)
PA5: P1.12, U19.39 (PA5)
PA6: P1.14, U19.38 (PA6)
PA7: P1.16, U19.37 (PA7)
PB0: P1.18, U19.18 (PB0)
PB1: P1.20, U19.19 (PB1)
PB2: P1.22, U19.20 (PB2)
PB3: P1.24 (P20), U19.21 (PB3)
PB4: P1.23, U19.22 (PB4)
PB5: P1.21, U19.23 (PB5)
PB6: P1.19, U19.24 (PB6)
PB7: P1.17, U19.25 (PB7)
PC0: P1.1, U19.14 (PC0)
PC1: P1.3, U19.15 (PC1)
PC2: P1.5, U19.16 (PC2)
PC3: P1.7, U19.17 (PC3)
PC4: P1.9, U19.13 (PC4)
PC5: P1.11, U19.12 (PC5)
PC6: P1.13, U19.11 (PC6)
PC7: P1.15, U19.10 (PC7)
PF1_TDI: P8.3, U33.4 (TDI)
PF1_TDO: P8.1, U33.17 (TDO)
PHANTOM*: P21.67 (PHANTOM*), U44.2 (A0)
PHI: P21.24 (PHI), U15.11 (B7)
PHI_CLOCK: U15.9 (A7)
POC*: P21.99 (POC*)
PPWR: K9.2 (PM), P1.25 (P24)
PWRFAIL*: P21.13 (PWRFAIL*)
RDY: P21.72 (RDY), U15.18 (B0)
RESET: U1.35 (MR), U7.2, U7.3, U19.35 (RESET)
RESET*: P21.75 (RESET*), U15.15 (B3)
RFU1: P21.27 (RFU_1), U13.3 (A1)
RFU2: P21.28 (RFU_2)
RFU3: P21.69 (RFU3)
RFU4: P21.71 (RFU4)
RTS_TTL: U1.32 (RTS), U28.3 (RTS#)
S6LX9_TD0: P9.1, U30.106 (TDO)
S6LX9_TDI: P9.3, U30.110 (TDI)
S100bufferEN: JP4.1, R4.1, U13.1 (A->B), U13.19 (CE), U14.1 (A->B), U14.19 (CE), U15.1 (A->B), U15.19 (CE), U42.1 (A->B), U42.19 (CE), U44.1 (A->B), U44.19 (CE), U46.1 (G1), U46.19 (G2), U47.1 (G1), U47.19 (G2), U48.1 (G1), U48.19 (G2)
SDSB*: P21.18 (SDSB*)
SIN_TTL: U1.10 (SIN), U28.1 (TXD)
SIXTN*: P21.60 (SIXTN*)
SLAVE_CLR*: P21.54 (SLAVE_CLR*)
SOUT_TTL: U1.11 (SOUT), U28.5 (RXD)
TCK: R30.1, U30.109 (TCK), U32.67 (TCK), U33.6 (TCK)
TMA0*: P21.55 (TMA0*)
TMA1*: P21.56 (TMA1*)
TMA2*: P21.57 (TMA2*)
TMA3*: P21.14 (TMA3*)
TMS: R32.1, U30.107 (TMS), U32.65 (TMS), U33.5 (TMS)
USB_VCC0: J1.1, R25.1, R26.1, U28.4 (VCCIO), U28.20 (VCC)
V1.2: C32.1, C42.1, C48.1, C54.1, C56.1, C60.1, U12.2 (VO), U30.19 (VCCINT), U30.28 (VCCINT), U30.52 (VCCINT), U30.89 (VCCINT), U30.128 (VCCINT)
V2.5: C29.1, R34.1, R35.1, U11.3 (VO)
V3.3: C26.1, C41.1, C43.1, C44.1, C45.1, C46.1, C47.1, C49.1, C50.1, C51.1, C52.1, C55.1, C57.1, C58.1, C59.1, C61.1, C62.1, C65.1, C66.1, C67.1, C68.1, C69.1, C70.1, P4.2, P14.2, R9.2, R33.2, R36.1, U3.3 (SIO2), U3.7 (HOLD), U3.8 (VCC), U17.3 (OUT), U30.4 (VCCO_3), U30.18 (VCCO_3), U30.20 (VCCAUX), U30.31 (VCCO_3), U30.36 (VCCAUX), U30.42 (VCCO_2), U30.53 (VCCAUX), U30.63 (VCCO_2), U30.69 (IO_L1N_M0_CMPMISO_2), U30.76 (VCCO_1), U30.86 (VCCO_1), U30.90 (VCCAUX), U30.103 (VCCO_1), U30.122 (VCCO_0), U30.125 (VCCO_0), U30.129 (VCCAUX), U30.135 (VCCO_0), U31.4 (VDD), U32.1 (VCCIO), U32.8 (VCCINT), U32.37 (VCCIO), U32.42 (VCCINT), U32.55 (VCCIO), U32.73 (VCCIO), U32.84 (VCCINT), U32.109 (VCCIO), U32.127 (VCCIO), U32.141 (VCCINT), U33.18 (VCCINT), U33.19 (VCCO), U33.20 (VCCJ), U43.20 (VCC), U53.20 (VCC)
VCC: C1.1, C4.1, C5.1, C6.1, C7.1, C8.1, C9.1, C10.1, C11.1, C12.1, C13.1, C14.1, C15.1, C16.1, C17.1, C18.1, C19.1, C20.1, C23.1, C25.1, C30.1, C31.1, D2.2 (K), K1.3, K9.3, P2.1, P2.14, P5.1, P5.8, R2.1, R3.1, R4.2, R12.1, R21.1, R23.1, R27.1, U1.12 (CS0), U1.13 (CS1), U6.3 (OUT), U24.11 (VCC), U25.32 (VDD), U27.32 (VDD)
VI0*: P21.4 (VIO*)
VI1*: P21.5 (VI1*), U14.11 (B7)
VI2*: P21.6 (VI2*), U14.12 (B6)
VI3*: P21.7 (VI3*), U14.13 (B5)
VI4*: P21.8 (VI4*), U14.14 (B4)
VI5*: P21.9 (VI5*), U14.15 (B3)
VI6*: P21.10 (VI6*), U14.16 (B2)
VI7*: P21.11 (VI7*), U14.17 (B1)
XRDY: P21.3 (XRDY)
pDBIN: P21.78 (pDBIN), U44.6 (A4)
pHLDA: P21.26 (pHDLA), U13.2 (A0)
pSTVAL*: P21.25 (pSTVAL*)
pSYNC: P21.76 (pSYNC), U44.4 (A2)
pWR*: P21.77 (pWR*), U44.5 (A3)
sHLTA: P21.48 (sHLTA)
sINP: P21.46 (sINP), U42.4 (A2)
sINTA: P21.96 (sINTA), U44.7 (A5)
sM1: P21.44 (sM1), U42.2 (A0)
sMEMR: P21.47 (sMEMR), U42.5 (A3)
sOUT: P21.45 (sOUT), U42.3 (A1)
sWO*: P21.97 (sWO*), U44.8 (A6)
sXTRQ*: P21.58 (sXTRQ*)

Notes on the sheet:
Pin 49
Input to Processor from CPLD
Input - from Processor to CPLD
Pin 47 (MEM RD) Output
Pin 12 (Nonmaskable Interrupt) Input
Pin 45 (I/O WR) output
MOUNTING HOLES
Connections for 25LC devices --------------------------------------- PICkit 2 Pin 25LC Device Pin (DIP) (1) VPP 1 nCS (2) Vdd 8 Vcc (3) GND 4 Vss (4) PGD 2 SO (5) PGC 6 SCK (6) AUX 5 SI 7 nHOLD - disabled (Vdd) 3 nWP - disabled (Vdd)
All routed to CPLD
Pin 5 (RXD) - INPUT Pin 1 (TXD) - OUTPUT
SRAM used as ROM space. CS defined by latches inside CPLD so Z80 can run initial program to load SRAM with Program (seen as RAM) and then switch its CS line over to see it as ROM
/CS_ROM1-2 are extra ROMs
POWER
CONFIG
DONE_LED
DIN
2CCLK
INIT_B
XILINX CABLE HEADER 1, 3, 5, 7, 9, 11, 13 - GND 2 - VREF +3.3V 4 - TMS 6 - TCK 8 - TDO 10 - TDI 12, 14 - NC
PROG_B
Jumper to exclude Uxx CPLD1 from Chain jump 2->4, for inclusion jump 1->2 & 3->4
BANK 2
BANK 1
BANK 0
BANK 3
Jumper to exclude Program Flash 1 from Chain jump 2->4, for inclusion jump 1->2 & 3->4
Jumper to exclude S3E 1 from Chain jump 2->4, for inclusion jump 1->2 & 3->4
MODE Selector
K9 = USE FOR VCC OR GND PIN 25 PARALLEL PORT
DELETED!! K7 = USE FOR 512K SRAM OR 128K SRAM DELETED!!
K1 = USE FOR 32 PIN EPROM OR 28 PIN EPROM K6 = USE FOR 27C080 EPROM OR 29C040 FLASH K8 = USE FOR 27C080 EPROM OR 29C040 FLASH
SERIAL IO
PARALLEL IO
CPU, CLOCK, AND MEMORY
FILTER CAPACITORS ON VARIOUS INTEGRATED CIRCUITS
RESET SWITCH / POWER ON RESET / POWER SWITCH
to U35
to U36
B->A
Z80 OUTPUTS from FPGA
reset into CPLD
B->A OUTPUT to S100 BUS
Pin 63 (I/O REQUEST) output
Pin 46 (I/O RD) output
Pin 68 (MEM WR) Output
Pin 65 (MEM REQUEST) Output
Pin 66 (/REFRESH - Z80 DRAM Refresh) Output
Pin 67 (/PHANTOM) Output
Pin 68 (Memory Write) Output
Pin 72 (controld run/WAIT state of processor) Input
Pin 73 (request to interrupt to processor) Input
Pin 74 (request for HOLD to processor) Input
Pin 75 (forces processor to reset state) Input
Pin 76 (indicates beginning of machine cycle) Output
Pin 77 (active low when processor write to I/O or MEM) Output
Pin 78 (active high when processor reads I/O or MEM) Output
Pin 79 (Address line 0) output
OUTPUT to S100 BUS
ADDRESS OUTPUTS to S100 BUS
Pin 44 (processor Instruction Fetch Cycle M1) output
DATA I/O from/to S100 BUS
Z80 INPUTS to FPGA
Z80 DATA BUS INPUT to FPGA
Z80 DATA BUS OUTPUT from FPGA
+5V from Power supply on Rail
+3.3V from Power supply on Rail
to U37
Pin 63 (I/O Request Signal) output
from Pin 44 of CPLD
INPUT from S100 BUS
Input in terms of the Slave on the S100 Bus, DI is INPUT for salve, so, OUTPUT for master
OUTPUT from Slave on S100 Bus, INPUT for the Master
from Pin 41 of CPLD
from Pin 42 of CPLD
to U22
to U49
B->A INPUT from S100 BUS
Pin 5 (Vectored Interrupt 1) Input
Pin 6 (Vectored Interrupt 2) Input
Pin 7 (Vectored Interrupt 3) Input
Pin 8 (Vectored Interrupt 4) Input
Pin 9 (Vectored Interrupt 5) Input
Pin 10 (Vectored Interrupt 6) Input
Pin 11 (Vectored Interrupt 7) Input
Pin 16 (Address line 16) output
Pin 17 (Address line 17) output
Pin 15 (Address line 18) output
Pin 21 (Single Step Processor) Input
Pin 96 (Interrupt Acknowledge - for PINT, identifiees the IF cycle(s) about to happen) Output
Pin 97 (active low when processor is in Write status) Output
Pin 26 (Processor in HOLD condition) Output
Pin 27 (Processor in WAIT condition) Output
Pin 24 (Primary Processor clock line - USUALLY Output but Input into this board) Input
Pin 59 (Clock line 2) Input
B -> A
DPAK
TO-220
Input - from U35
to U42
to U44
to U13
to U15
to FPGA
to LED's
