CatspersCoffee/S100-Boards/Backplane-18-Slot/rev1/S100-Backplane.sch

## KiCad design Backplane-18-Slot/rev1/S100-Backplane.sch (2014-03-11, an earlier design)

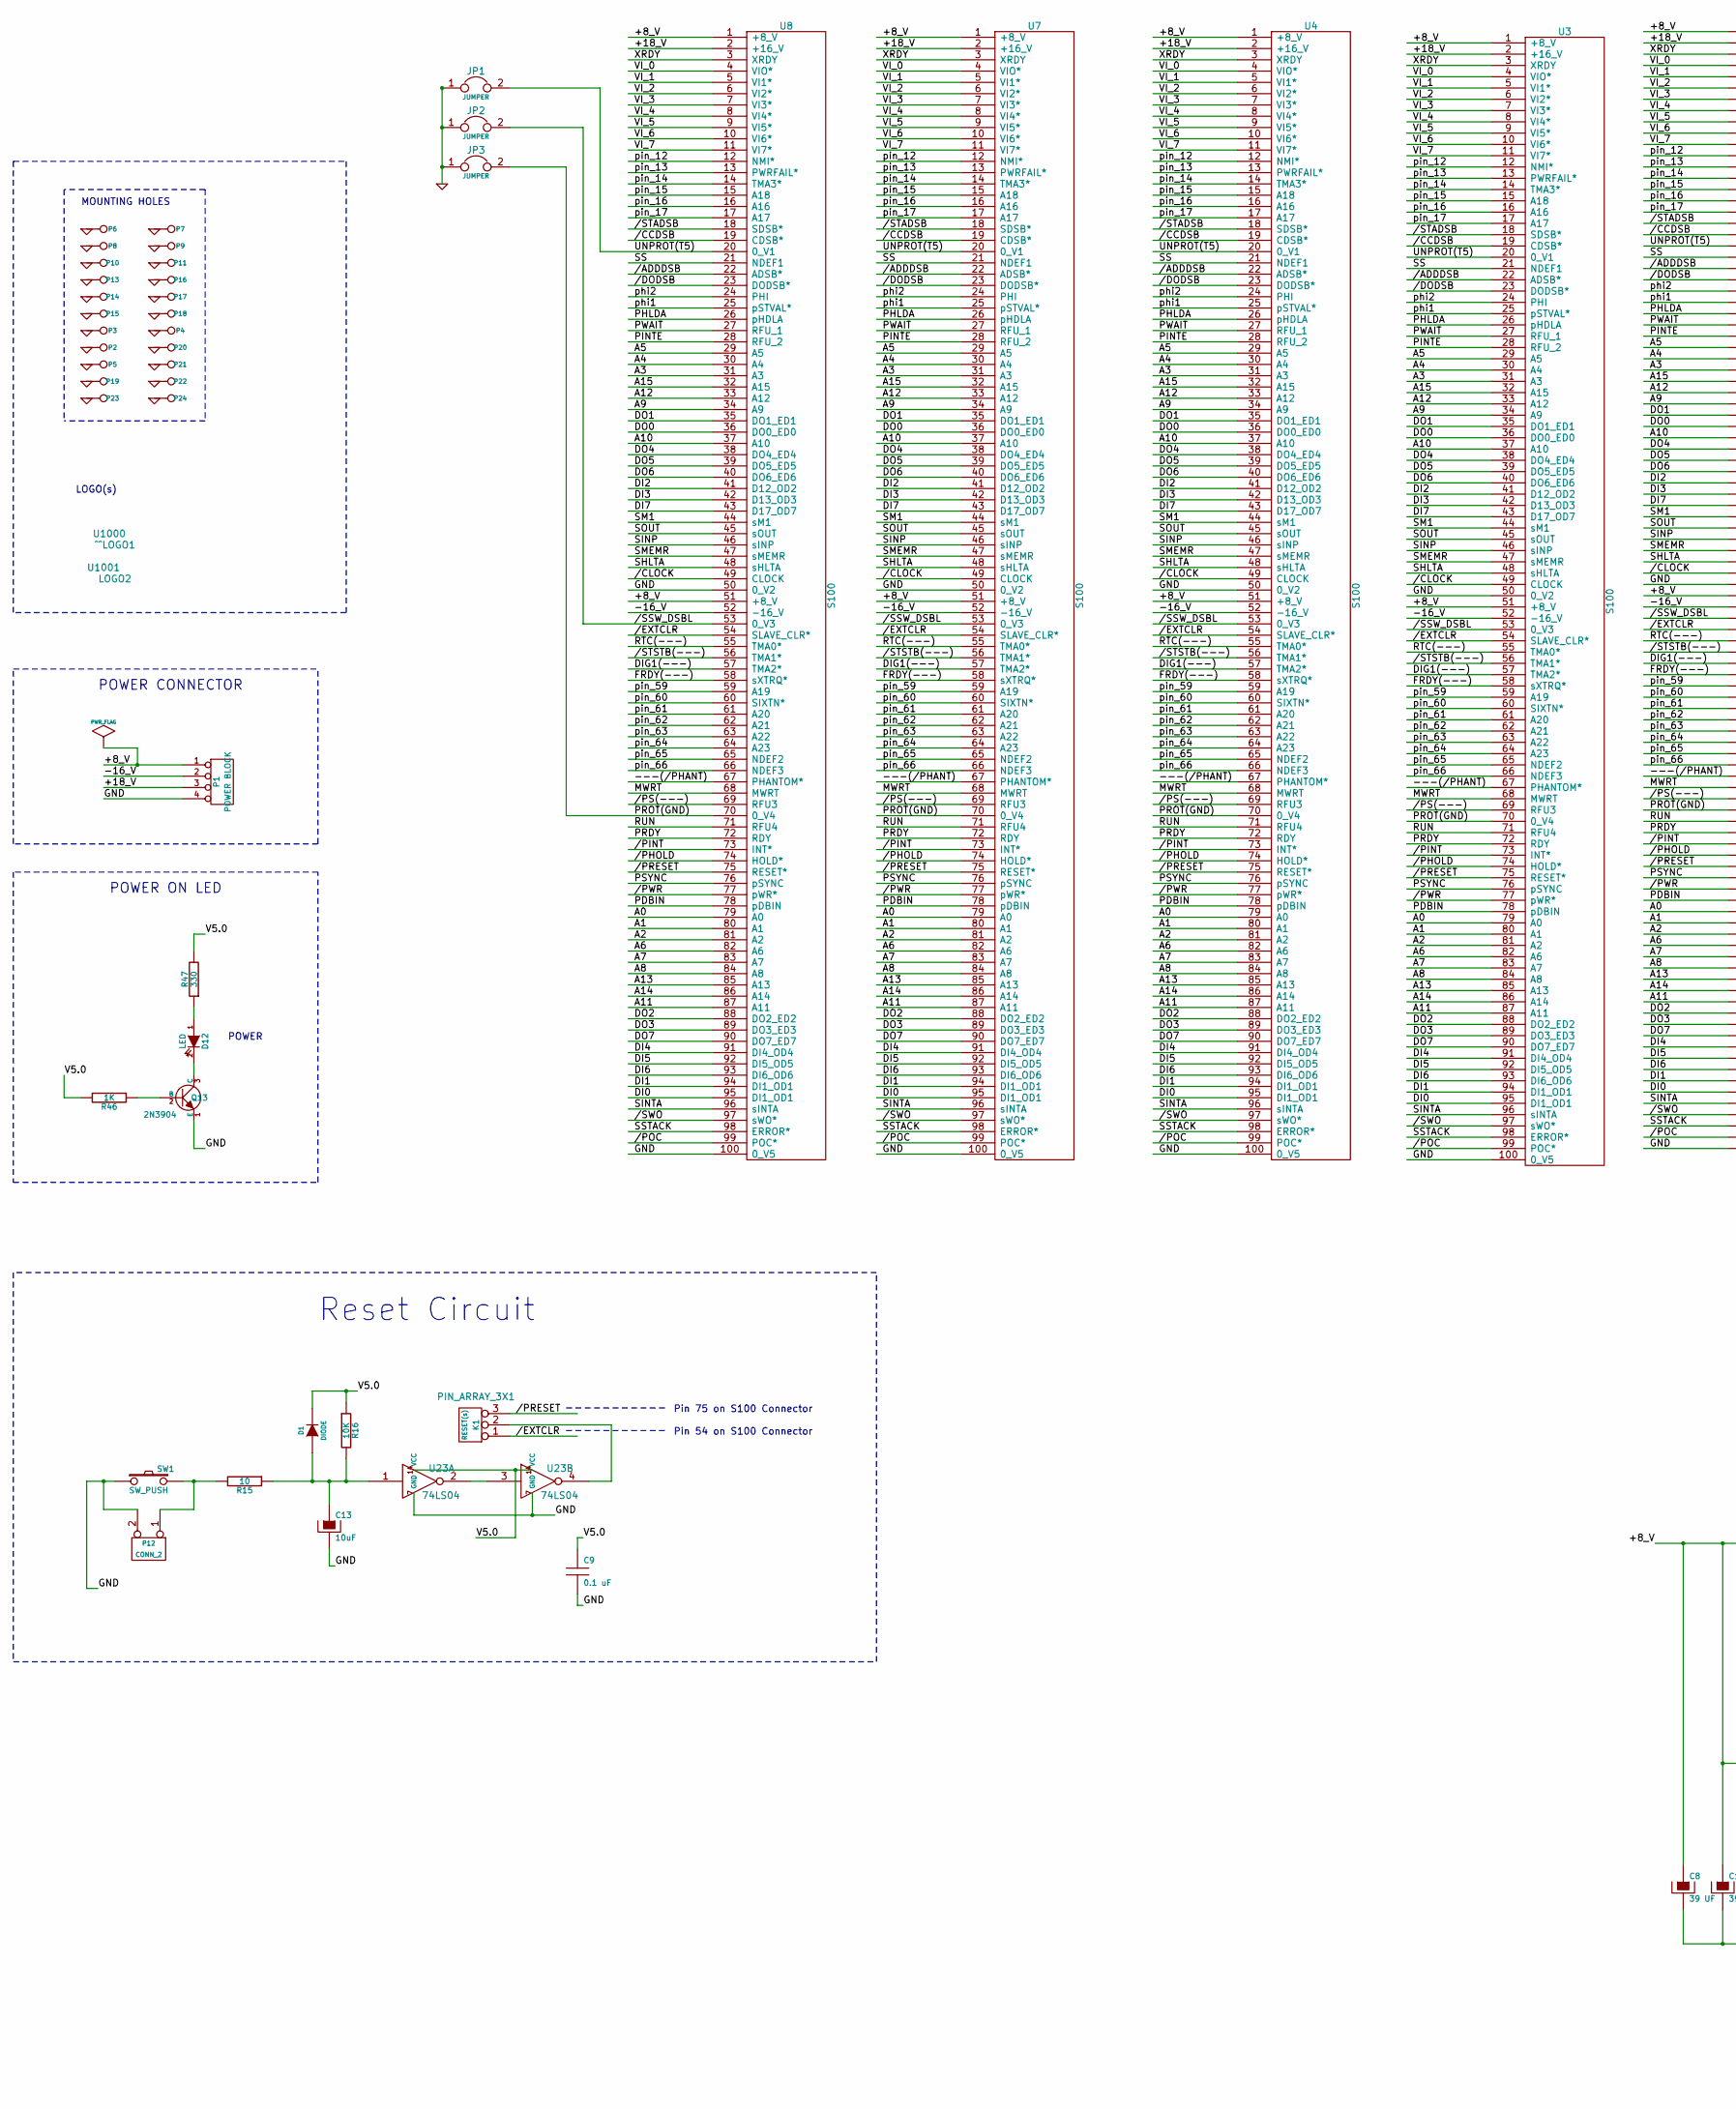
[picture p59: schematic S100-Backplane.sch, part in row 1, column 1]

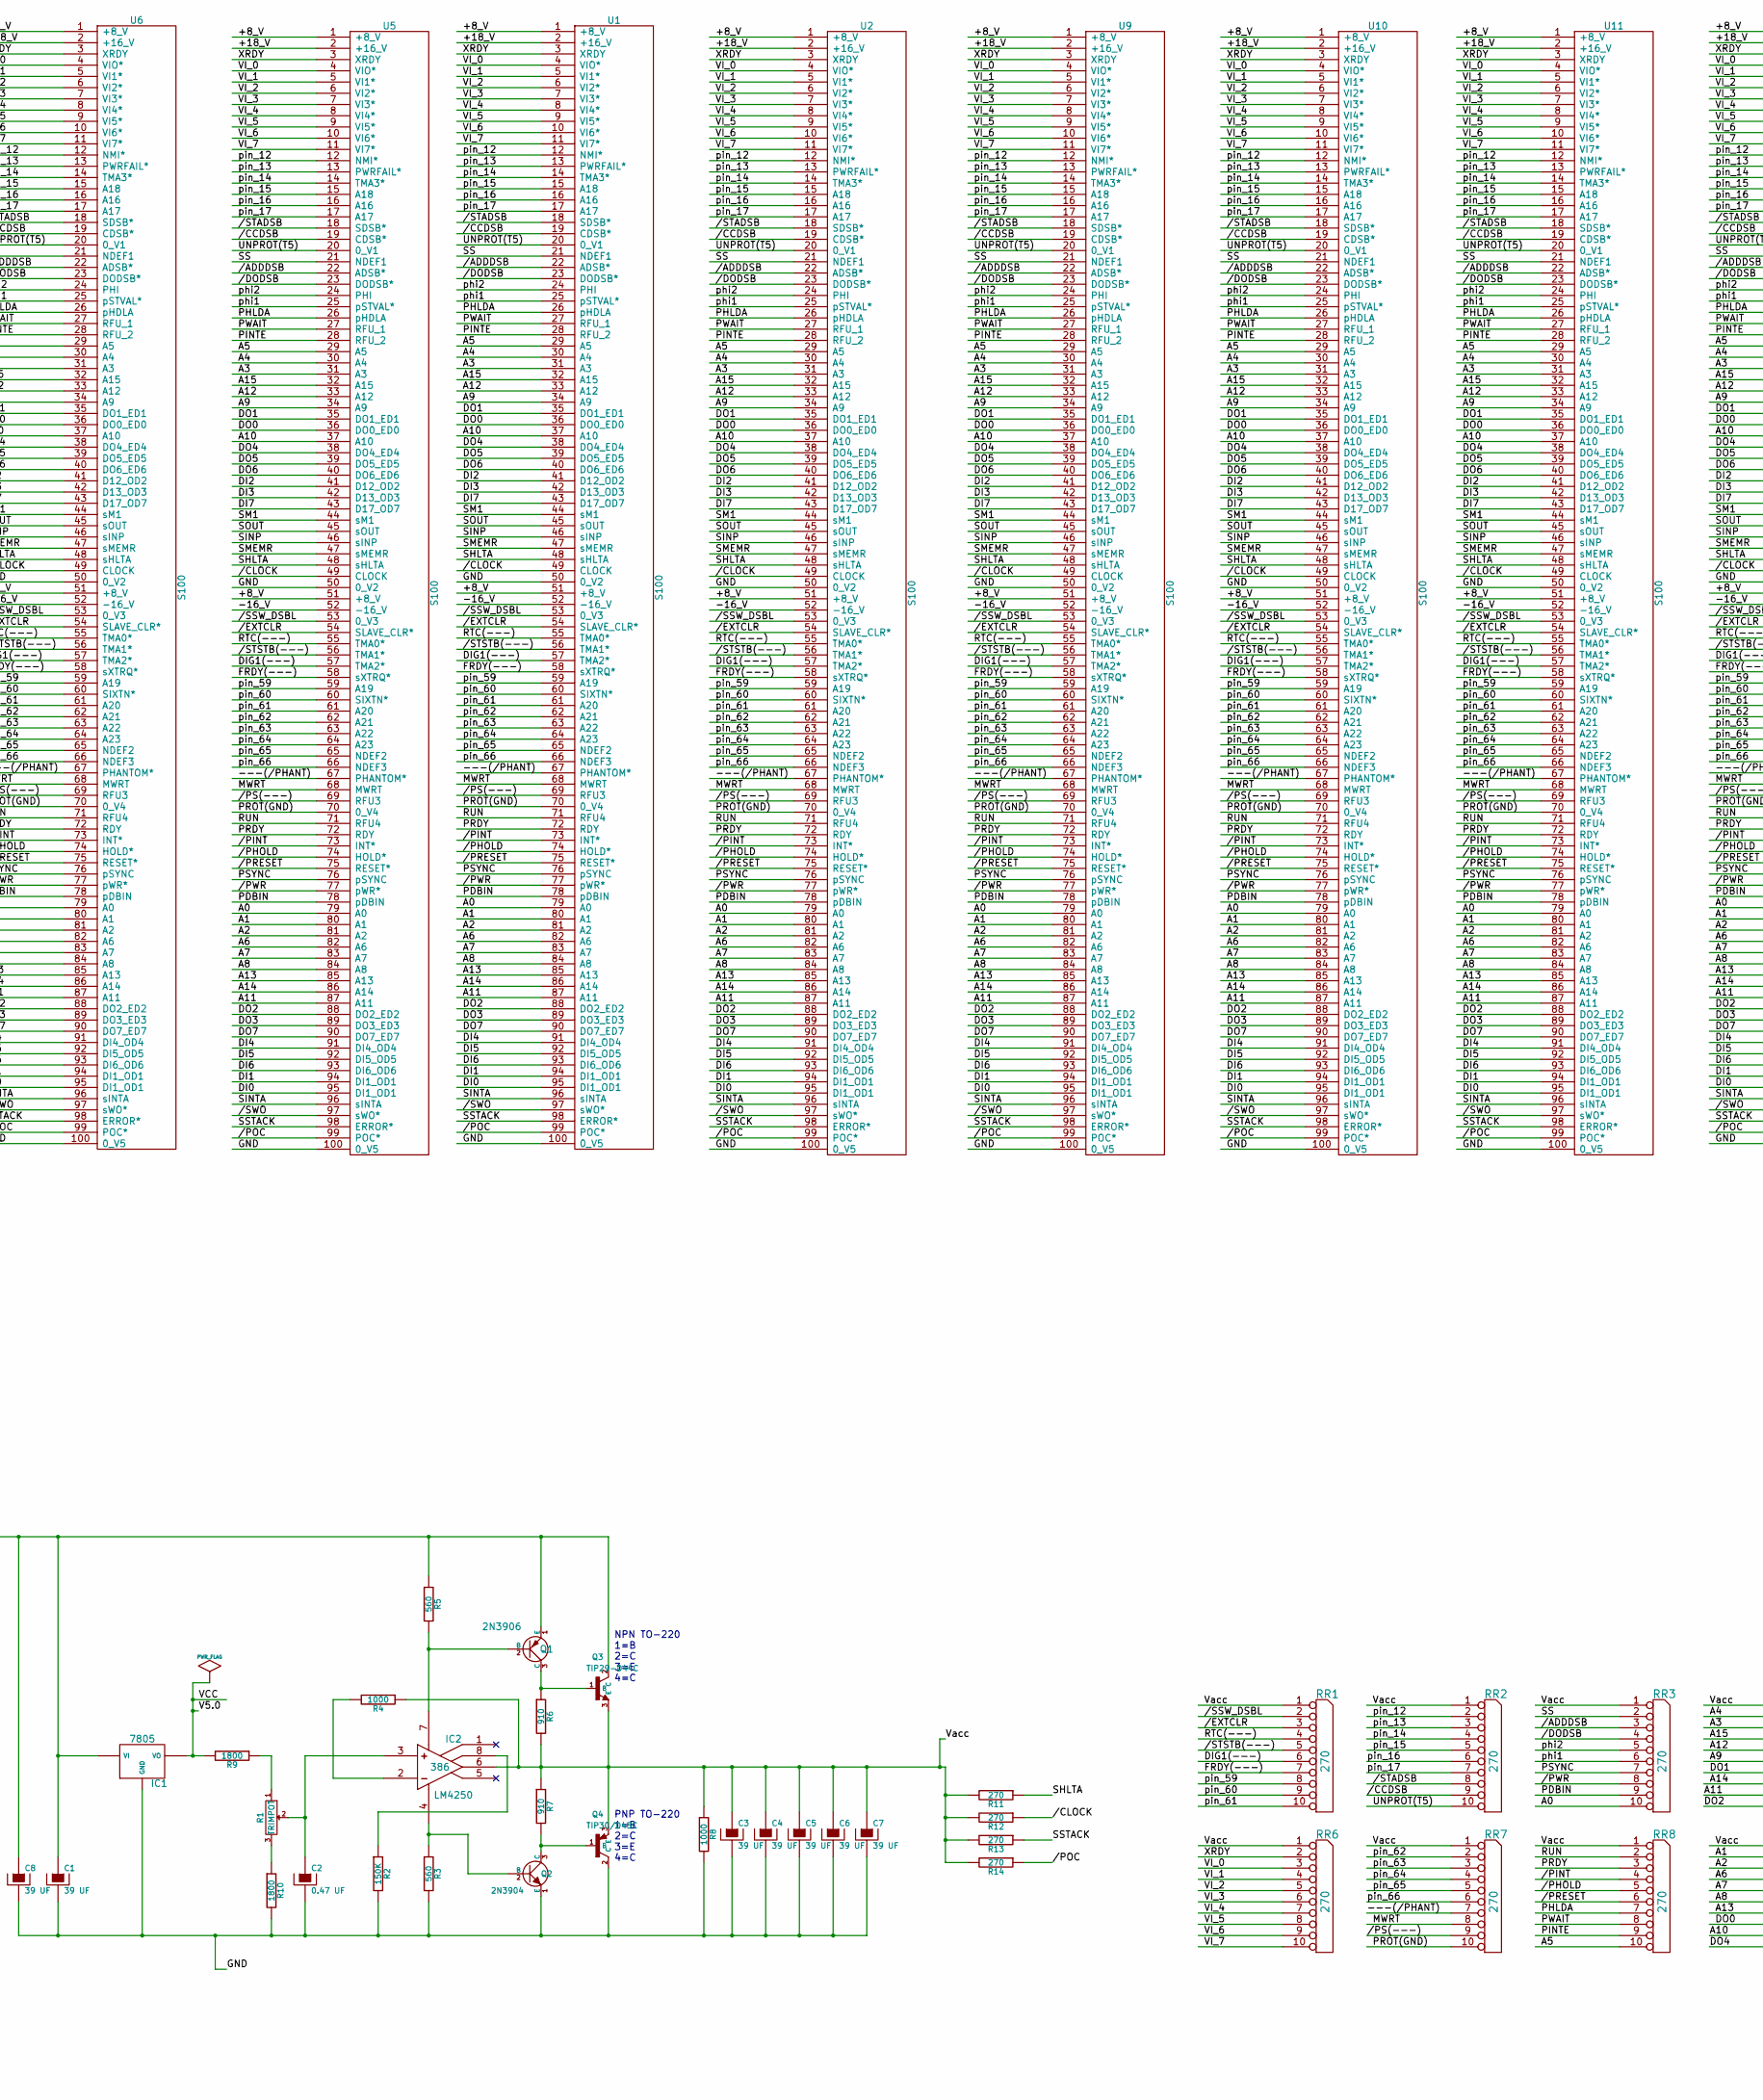
[picture p60: schematic S100-Backplane.sch, part in row 1, column 2]

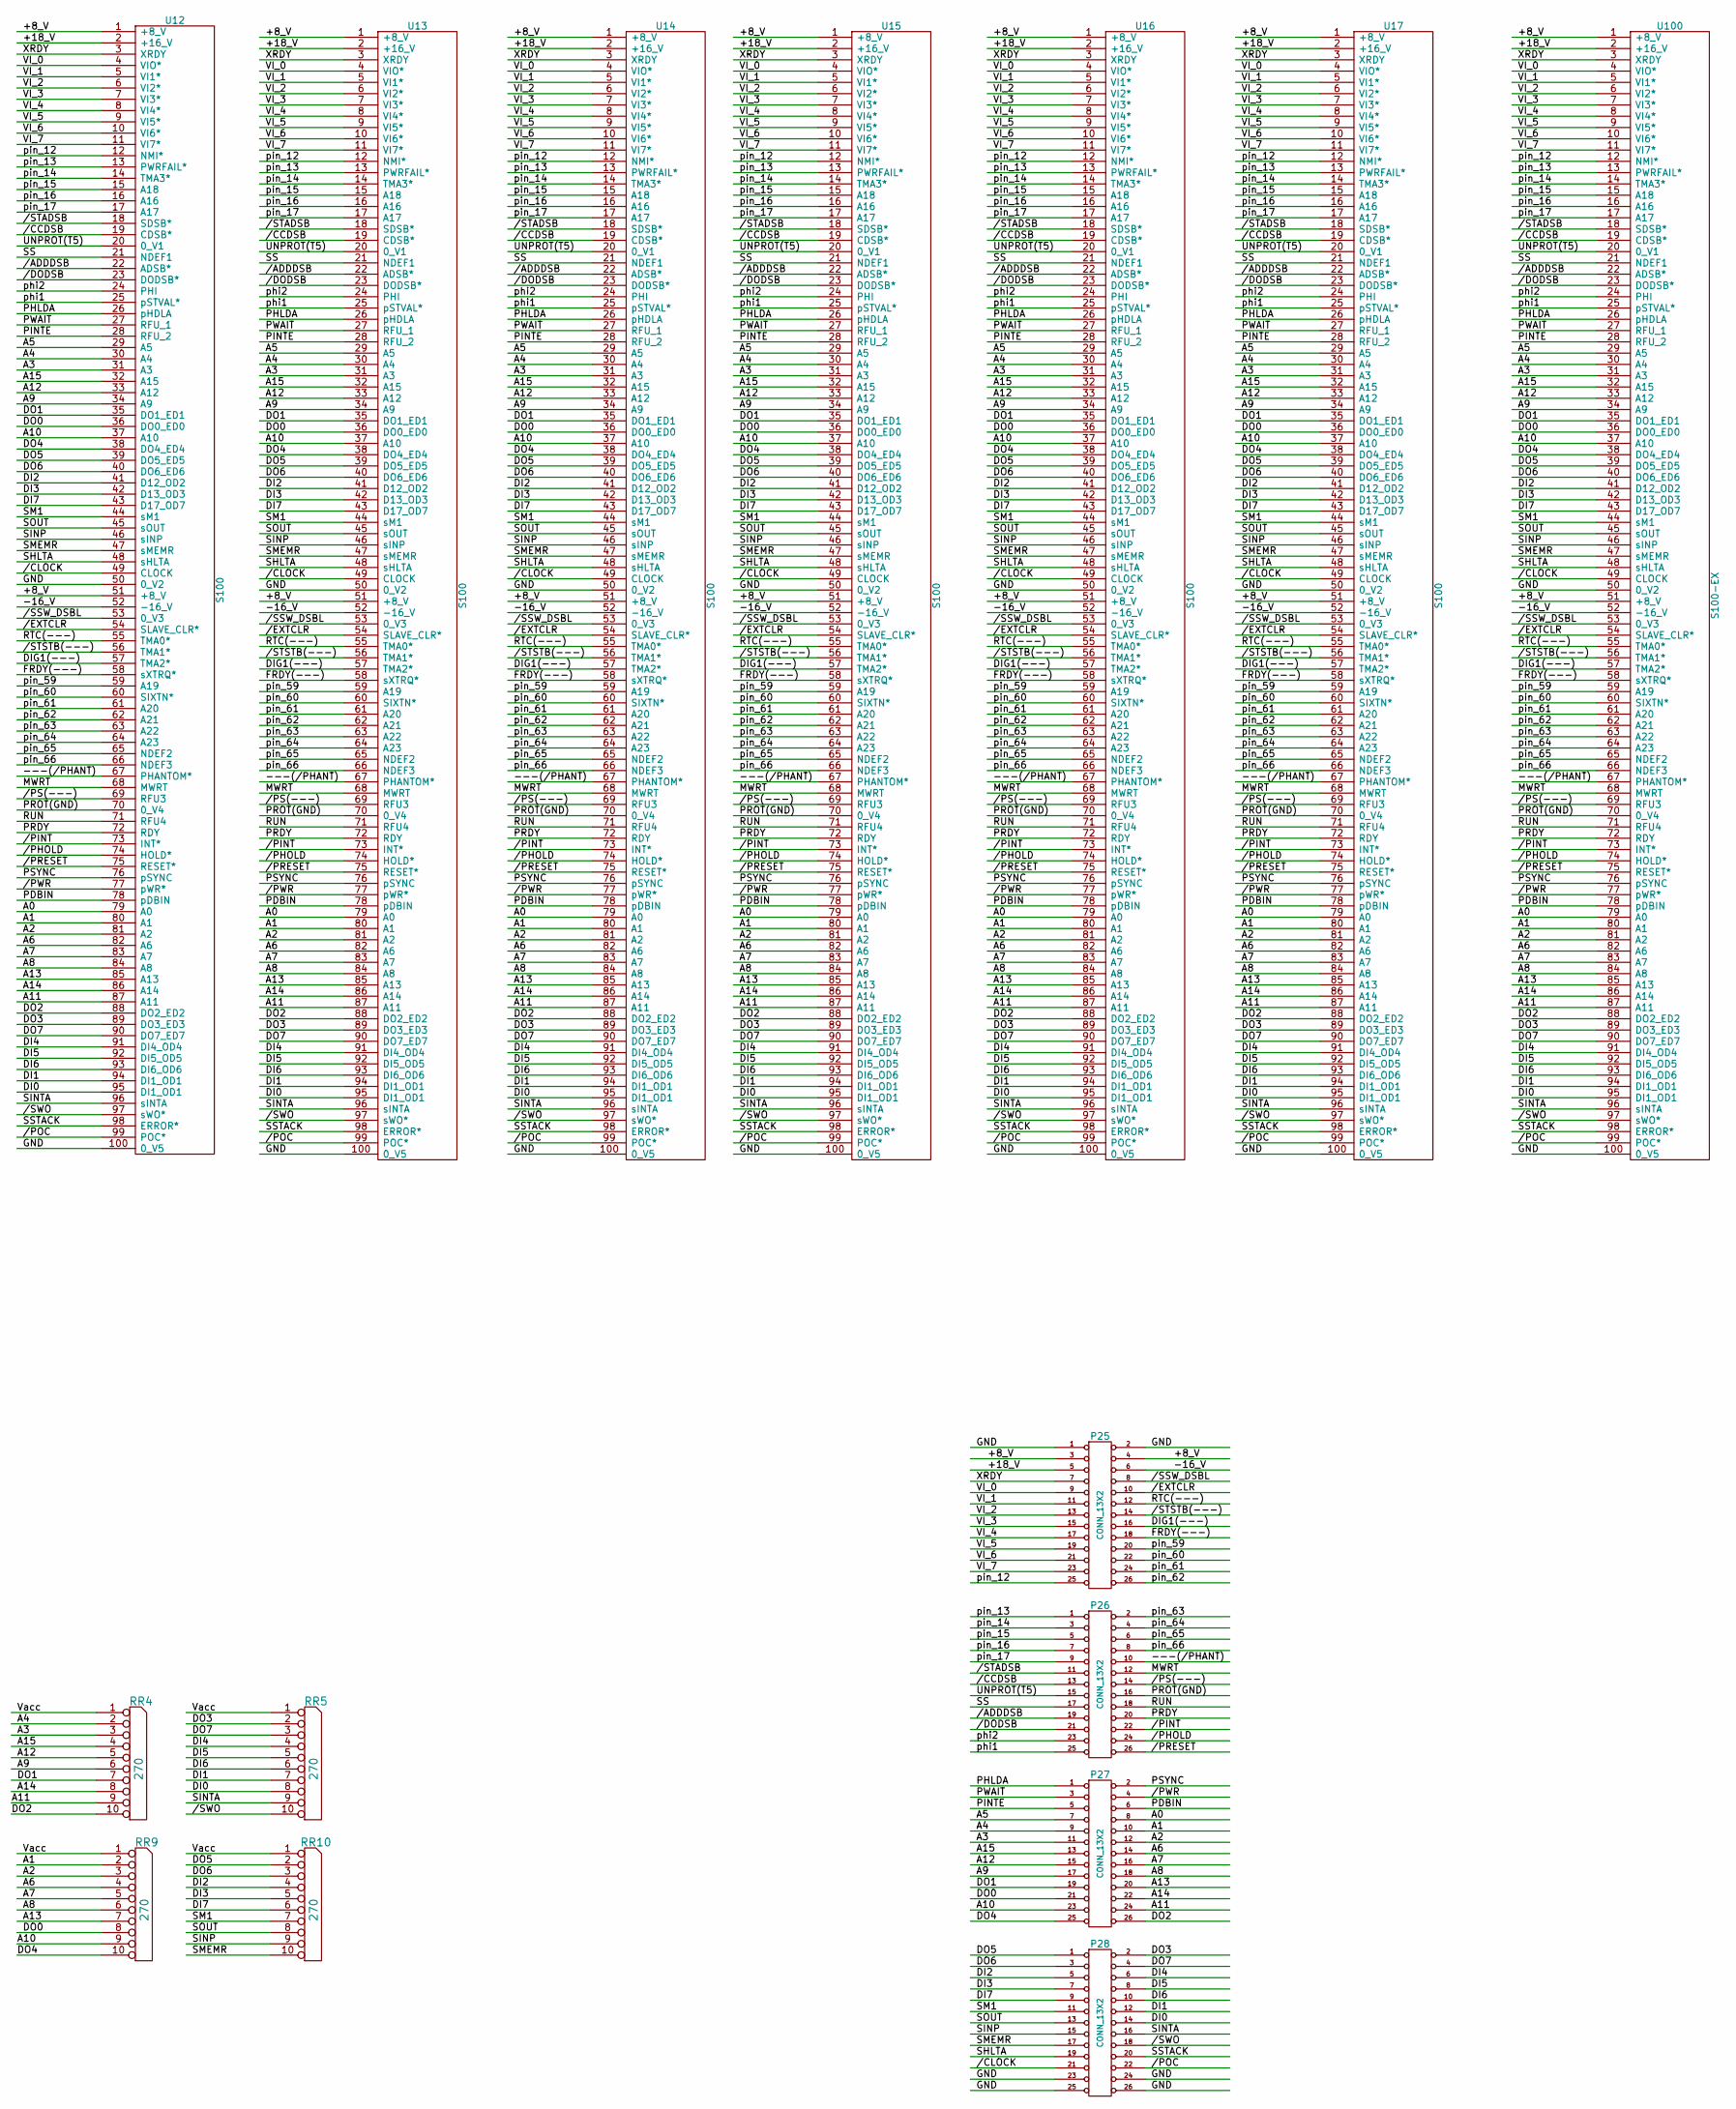
[picture p61: schematic S100-Backplane.sch, part in row 1, column 3]

Parts:
C1, C3, C4, C5, C6, C7, C8: 39 UF
C2: 0.47 UF
C9: 0.1 uF
C13: 10uF
D1: DIODE
D12: LED
IC1: 7805
IC2: LM4250
JP1, JP2, JP3: JUMPER
K1: RESET(s); PIN_ARRAY_3X1
P1: POWER BLOCK
P2, P3, P4, P5, P6, P7, P8, P9, P10, P11, P13, P14, P15, P16, P17, P18, P19, P20, P21, P22, P23, P24: CONN_1
P12: CONN_2
P25, P26, P27, P28: CONN_13X2
Q1: 2N3906
Q2, Q13: 2N3904
Q3: TIP29-D44C; transistor-TO220
Q4: TIP30/D45C; transistor-TO220
R1: TRIMPOT
R2: 150K
R3, R5: 560
R4, R8: 1000
R6, R7: 910
R9, R10: 1800
R11, R12, R13, R14: 270
R15: 10
R16: 10K
R46: 1K
R47: 330
RR1, RR2, RR3, RR4, RR5, RR6, RR7, RR8, RR9, RR10: 270
SW1: SW_PUSH
U1, U2, U3, U4, U5, U6, U7, U8, U9, U10, U11, U12, U13, U14, U15, U16, U17: S100
U23: 74LS04
U100: S100-EX
U1000: ^^LOGO1
U1001: LOGO2

Connections:
+8_V: C1.1, C8.1, IC1.VI, P1.1, P25.3, P25.4, Q1.1 (E), Q3.2 (C), R5.1, U1.1 (+8_V), U1.51 (+8_V), U2.1 (+8_V), U2.51 (+8_V), U3.1 (+8_V), U3.51 (+8_V), U4.1 (+8_V), U4.51 (+8_V), U5.1 (+8_V), U5.51 (+8_V), U6.1 (+8_V), U6.51 (+8_V), U7.1 (+8_V), U7.51 (+8_V), U8.1 (+8_V), U8.51 (+8_V), U9.1 (+8_V), U9.51 (+8_V), U10.1 (+8_V), U10.51 (+8_V), U11.1 (+8_V), U11.51 (+8_V), U12.1 (+8_V), U12.51 (+8_V), U13.1 (+8_V), U13.51 (+8_V), U14.1 (+8_V), U14.51 (+8_V), U15.1 (+8_V), U15.51 (+8_V), U16.1 (+8_V), U16.51 (+8_V), U17.1 (+8_V), U17.51 (+8_V), U100.1 (+8_V), U100.51 (+8_V)
+18_V: P1.3, P25.5, U1.2 (+16_V), U2.2 (+16_V), U3.2 (+16_V), U4.2 (+16_V), U5.2 (+16_V), U6.2 (+16_V), U7.2 (+16_V), U8.2 (+16_V), U9.2 (+16_V), U10.2 (+16_V), U11.2 (+16_V), U12.2 (+16_V), U13.2 (+16_V), U14.2 (+16_V), U15.2 (+16_V), U16.2 (+16_V), U17.2 (+16_V), U100.2 (+16_V)
-16_V: P1.2, P25.6, U1.52 (-16_V), U2.52 (-16_V), U3.52 (-16_V), U4.52 (-16_V), U5.52 (-16_V), U6.52 (-16_V), U7.52 (-16_V), U8.52 (-16_V), U9.52 (-16_V), U10.52 (-16_V), U11.52 (-16_V), U12.52 (-16_V), U13.52 (-16_V), U14.52 (-16_V), U15.52 (-16_V), U16.52 (-16_V), U17.52 (-16_V), U100.52 (-16_V)
---(/PHANT): P26.10, RR7.7, U1.67 (PHANTOM*), U2.67 (PHANTOM*), U3.67 (PHANTOM*), U4.67 (PHANTOM*), U5.67 (PHANTOM*), U6.67 (PHANTOM*), U7.67 (PHANTOM*), U8.67 (PHANTOM*), U9.67 (PHANTOM*), U10.67 (PHANTOM*), U11.67 (PHANTOM*), U12.67 (PHANTOM*), U13.67 (PHANTOM*), U14.67 (PHANTOM*), U15.67 (PHANTOM*), U16.67 (PHANTOM*), U17.67 (PHANTOM*), U100.67 (PHANTOM*)
/ADDDSB: P26.19, RR3.3, U1.22 (ADSB*), U2.22 (ADSB*), U3.22 (ADSB*), U4.22 (ADSB*), U5.22 (ADSB*), U6.22 (ADSB*), U7.22 (ADSB*), U8.22 (ADSB*), U9.22 (ADSB*), U10.22 (ADSB*), U11.22 (ADSB*), U12.22 (ADSB*), U13.22 (ADSB*), U14.22 (ADSB*), U15.22 (ADSB*), U16.22 (ADSB*), U17.22 (ADSB*), U100.22 (ADSB*)
/CCDSB: P26.13, RR2.9, U1.19 (CDSB*), U2.19 (CDSB*), U3.19 (CDSB*), U4.19 (CDSB*), U5.19 (CDSB*), U6.19 (CDSB*), U7.19 (CDSB*), U8.19 (CDSB*), U9.19 (CDSB*), U10.19 (CDSB*), U11.19 (CDSB*), U12.19 (CDSB*), U13.19 (CDSB*), U14.19 (CDSB*), U15.19 (CDSB*), U16.19 (CDSB*), U17.19 (CDSB*), U100.19 (CDSB*)
/CLOCK: P28.21, R12.1, U1.49 (CLOCK), U2.49 (CLOCK), U3.49 (CLOCK), U4.49 (CLOCK), U5.49 (CLOCK), U6.49 (CLOCK), U7.49 (CLOCK), U8.49 (CLOCK), U9.49 (CLOCK), U10.49 (CLOCK), U11.49 (CLOCK), U12.49 (CLOCK), U13.49 (CLOCK), U14.49 (CLOCK), U15.49 (CLOCK), U16.49 (CLOCK), U17.49 (CLOCK), U100.49 (CLOCK)
/DODSB: P26.21, RR3.4, U1.23 (DODSB*), U2.23 (DODSB*), U3.23 (DODSB*), U4.23 (DODSB*), U5.23 (DODSB*), U6.23 (DODSB*), U7.23 (DODSB*), U8.23 (DODSB*), U9.23 (DODSB*), U10.23 (DODSB*), U11.23 (DODSB*), U12.23 (DODSB*), U13.23 (DODSB*), U14.23 (DODSB*), U15.23 (DODSB*), U16.23 (DODSB*), U17.23 (DODSB*), U100.23 (DODSB*)
/EXTCLR: K1.1, P25.10, RR1.3, U1.54 (SLAVE_CLR*), U2.54 (SLAVE_CLR*), U3.54 (SLAVE_CLR*), U4.54 (SLAVE_CLR*), U5.54 (SLAVE_CLR*), U6.54 (SLAVE_CLR*), U7.54 (SLAVE_CLR*), U8.54 (SLAVE_CLR*), U9.54 (SLAVE_CLR*), U10.54 (SLAVE_CLR*), U11.54 (SLAVE_CLR*), U12.54 (SLAVE_CLR*), U13.54 (SLAVE_CLR*), U14.54 (SLAVE_CLR*), U15.54 (SLAVE_CLR*), U16.54 (SLAVE_CLR*), U17.54 (SLAVE_CLR*), U100.54 (SLAVE_CLR*)
/PHOLD: P26.24 (P20), RR8.5, U1.74 (HOLD*), U2.74 (HOLD*), U3.74 (HOLD*), U4.74 (HOLD*), U5.74 (HOLD*), U6.74 (HOLD*), U7.74 (HOLD*), U8.74 (HOLD*), U9.74 (HOLD*), U10.74 (HOLD*), U11.74 (HOLD*), U12.74 (HOLD*), U13.74 (HOLD*), U14.74 (HOLD*), U15.74 (HOLD*), U16.74 (HOLD*), U17.74 (HOLD*), U100.74 (HOLD*)
/PINT: P26.22, RR8.4, U1.73 (INT*), U2.73 (INT*), U3.73 (INT*), U4.73 (INT*), U5.73 (INT*), U6.73 (INT*), U7.73 (INT*), U8.73 (INT*), U9.73 (INT*), U10.73 (INT*), U11.73 (INT*), U12.73 (INT*), U13.73 (INT*), U14.73 (INT*), U15.73 (INT*), U16.73 (INT*), U17.73 (INT*), U100.73 (INT*)
/POC: P28.22, R14.1, U1.99 (POC*), U2.99 (POC*), U3.99 (POC*), U4.99 (POC*), U5.99 (POC*), U6.99 (POC*), U7.99 (POC*), U8.99 (POC*), U9.99 (POC*), U10.99 (POC*), U11.99 (POC*), U12.99 (POC*), U13.99 (POC*), U14.99 (POC*), U15.99 (POC*), U16.99 (POC*), U17.99 (POC*), U100.99 (POC*)
/PRESET: K1.3, P26.26 (P22), RR8.6, U1.75 (RESET*), U2.75 (RESET*), U3.75 (RESET*), U4.75 (RESET*), U5.75 (RESET*), U6.75 (RESET*), U7.75 (RESET*), U8.75 (RESET*), U9.75 (RESET*), U10.75 (RESET*), U11.75 (RESET*), U12.75 (RESET*), U13.75 (RESET*), U14.75 (RESET*), U15.75 (RESET*), U16.75 (RESET*), U17.75 (RESET*), U100.75 (RESET*)
/PS(---): P26.14, RR7.9, U1.69 (RFU3), U2.69 (RFU3), U3.69 (RFU3), U4.69 (RFU3), U5.69 (RFU3), U6.69 (RFU3), U7.69 (RFU3), U8.69 (RFU3), U9.69 (RFU3), U10.69 (RFU3), U11.69 (RFU3), U12.69 (RFU3), U13.69 (RFU3), U14.69 (RFU3), U15.69 (RFU3), U16.69 (RFU3), U17.69 (RFU3), U100.69 (RFU3)
/PWR: P27.4, RR3.8, U1.77 (pWR*), U2.77 (pWR*), U3.77 (pWR*), U4.77 (pWR*), U5.77 (pWR*), U6.77 (pWR*), U7.77 (pWR*), U8.77 (pWR*), U9.77 (pWR*), U10.77 (pWR*), U11.77 (pWR*), U12.77 (pWR*), U13.77 (pWR*), U14.77 (pWR*), U15.77 (pWR*), U16.77 (pWR*), U17.77 (pWR*), U100.77 (pWR*)
/SSW_DSBL: JP2.2, P25.8, RR1.2, U1.53 (0_V3), U2.53 (0_V3), U3.53 (0_V3), U4.53 (0_V3), U5.53 (0_V3), U6.53 (0_V3), U7.53 (0_V3), U8.53 (0_V3), U9.53 (0_V3), U10.53 (0_V3), U11.53 (0_V3), U12.53 (0_V3), U13.53 (0_V3), U14.53 (0_V3), U15.53 (0_V3), U16.53 (0_V3), U17.53 (0_V3), U100.53 (0_V3)
/STADSB: P26.11, RR2.8, U1.18 (SDSB*), U2.18 (SDSB*), U3.18 (SDSB*), U4.18 (SDSB*), U5.18 (SDSB*), U6.18 (SDSB*), U7.18 (SDSB*), U8.18 (SDSB*), U9.18 (SDSB*), U10.18 (SDSB*), U11.18 (SDSB*), U12.18 (SDSB*), U13.18 (SDSB*), U14.18 (SDSB*), U15.18 (SDSB*), U16.18 (SDSB*), U17.18 (SDSB*), U100.18 (SDSB*)
/STSTB(---): P25.14, RR1.5, U1.56 (TMA1*), U2.56 (TMA1*), U3.56 (TMA1*), U4.56 (TMA1*), U5.56 (TMA1*), U6.56 (TMA1*), U7.56 (TMA1*), U8.56 (TMA1*), U9.56 (TMA1*), U10.56 (TMA1*), U11.56 (TMA1*), U12.56 (TMA1*), U13.56 (TMA1*), U14.56 (TMA1*), U15.56 (TMA1*), U16.56 (TMA1*), U17.56 (TMA1*), U100.56 (TMA1*)
/SWO: P28.18, RR5.10, U1.97 (sWO*), U2.97 (sWO*), U3.97 (sWO*), U4.97 (sWO*), U5.97 (sWO*), U6.97 (sWO*), U7.97 (sWO*), U8.97 (sWO*), U9.97 (sWO*), U10.97 (sWO*), U11.97 (sWO*), U12.97 (sWO*), U13.97 (sWO*), U14.97 (sWO*), U15.97 (sWO*), U16.97 (sWO*), U17.97 (sWO*), U100.97 (sWO*)
A0: P27.8, RR3.10, U1.79 (A0), U2.79 (A0), U3.79 (A0), U4.79 (A0), U5.79 (A0), U6.79 (A0), U7.79 (A0), U8.79 (A0), U9.79 (A0), U10.79 (A0), U11.79 (A0), U12.79 (A0), U13.79 (A0), U14.79 (A0), U15.79 (A0), U16.79 (A0), U17.79 (A0), U100.79 (A0)
A1: P27.10, RR9.2, U1.80 (A1), U2.80 (A1), U3.80 (A1), U4.80 (A1), U5.80 (A1), U6.80 (A1), U7.80 (A1), U8.80 (A1), U9.80 (A1), U10.80 (A1), U11.80 (A1), U12.80 (A1), U13.80 (A1), U14.80 (A1), U15.80 (A1), U16.80 (A1), U17.80 (A1), U100.80 (A1)
A2: P27.12, RR9.3, U1.81 (A2), U2.81 (A2), U3.81 (A2), U4.81 (A2), U5.81 (A2), U6.81 (A2), U7.81 (A2), U8.81 (A2), U9.81 (A2), U10.81 (A2), U11.81 (A2), U12.81 (A2), U13.81 (A2), U14.81 (A2), U15.81 (A2), U16.81 (A2), U17.81 (A2), U100.81 (A2)
A3: P27.11, RR4.3, U1.31 (A3), U2.31 (A3), U3.31 (A3), U4.31 (A3), U5.31 (A3), U6.31 (A3), U7.31 (A3), U8.31 (A3), U9.31 (A3), U10.31 (A3), U11.31 (A3), U12.31 (A3), U13.31 (A3), U14.31 (A3), U15.31 (A3), U16.31 (A3), U17.31 (A3), U100.31 (A3)
A4: P27.9, RR4.2, U1.30 (A4), U2.30 (A4), U3.30 (A4), U4.30 (A4), U5.30 (A4), U6.30 (A4), U7.30 (A4), U8.30 (A4), U9.30 (A4), U10.30 (A4), U11.30 (A4), U12.30 (A4), U13.30 (A4), U14.30 (A4), U15.30 (A4), U16.30 (A4), U17.30 (A4), U100.30 (A4)
A5: P27.7, RR8.10, U1.29 (A5), U2.29 (A5), U3.29 (A5), U4.29 (A5), U5.29 (A5), U6.29 (A5), U7.29 (A5), U8.29 (A5), U9.29 (A5), U10.29 (A5), U11.29 (A5), U12.29 (A5), U13.29 (A5), U14.29 (A5), U15.29 (A5), U16.29 (A5), U17.29 (A5), U100.29 (A5)
A6: P27.14, RR9.4, U1.82 (A6), U2.82 (A6), U3.82 (A6), U4.82 (A6), U5.82 (A6), U6.82 (A6), U7.82 (A6), U8.82 (A6), U9.82 (A6), U10.82 (A6), U11.82 (A6), U12.82 (A6), U13.82 (A6), U14.82 (A6), U15.82 (A6), U16.82 (A6), U17.82 (A6), U100.82 (A6)
A7: P27.16, RR9.5, U1.83 (A7), U2.83 (A7), U3.83 (A7), U4.83 (A7), U5.83 (A7), U6.83 (A7), U7.83 (A7), U8.83 (A7), U9.83 (A7), U10.83 (A7), U11.83 (A7), U12.83 (A7), U13.83 (A7), U14.83 (A7), U15.83 (A7), U16.83 (A7), U17.83 (A7), U100.83 (A7)
A8: P27.18, RR9.6, U1.84 (A8), U2.84 (A8), U3.84 (A8), U4.84 (A8), U5.84 (A8), U6.84 (A8), U7.84 (A8), U8.84 (A8), U9.84 (A8), U10.84 (A8), U11.84 (A8), U12.84 (A8), U13.84 (A8), U14.84 (A8), U15.84 (A8), U16.84 (A8), U17.84 (A8), U100.84 (A8)
A9: P27.17, RR4.6, U1.34 (A9), U2.34 (A9), U3.34 (A9), U4.34 (A9), U5.34 (A9), U6.34 (A9), U7.34 (A9), U8.34 (A9), U9.34 (A9), U10.34 (A9), U11.34 (A9), U12.34 (A9), U13.34 (A9), U14.34 (A9), U15.34 (A9), U16.34 (A9), U17.34 (A9), U100.34 (A9)
A10: P27.23, RR9.9, U1.37 (A10), U2.37 (A10), U3.37 (A10), U4.37 (A10), U5.37 (A10), U6.37 (A10), U7.37 (A10), U8.37 (A10), U9.37 (A10), U10.37 (A10), U11.37 (A10), U12.37 (A10), U13.37 (A10), U14.37 (A10), U15.37 (A10), U16.37 (A10), U17.37 (A10), U100.37 (A10)
A11: P27.24 (P20), RR4.9, U1.87 (A11), U2.87 (A11), U3.87 (A11), U4.87 (A11), U5.87 (A11), U6.87 (A11), U7.87 (A11), U8.87 (A11), U9.87 (A11), U10.87 (A11), U11.87 (A11), U12.87 (A11), U13.87 (A11), U14.87 (A11), U15.87 (A11), U16.87 (A11), U17.87 (A11), U100.87 (A11)
A12: P27.15, RR4.5, U1.33 (A12), U2.33 (A12), U3.33 (A12), U4.33 (A12), U5.33 (A12), U6.33 (A12), U7.33 (A12), U8.33 (A12), U9.33 (A12), U10.33 (A12), U11.33 (A12), U12.33 (A12), U13.33 (A12), U14.33 (A12), U15.33 (A12), U16.33 (A12), U17.33 (A12), U100.33 (A12)
A13: P27.20, RR9.7, U1.85 (A13), U2.85 (A13), U3.85 (A13), U4.85 (A13), U5.85 (A13), U6.85 (A13), U7.85 (A13), U8.85 (A13), U9.85 (A13), U10.85 (A13), U11.85 (A13), U12.85 (A13), U13.85 (A13), U14.85 (A13), U15.85 (A13), U16.85 (A13), U17.85 (A13), U100.85 (A13)
A14: P27.22, RR4.8, U1.86 (A14), U2.86 (A14), U3.86 (A14), U4.86 (A14), U5.86 (A14), U6.86 (A14), U7.86 (A14), U8.86 (A14), U9.86 (A14), U10.86 (A14), U11.86 (A14), U12.86 (A14), U13.86 (A14), U14.86 (A14), U15.86 (A14), U16.86 (A14), U17.86 (A14), U100.86 (A14)
A15: P27.13, RR4.4, U1.32 (A15), U2.32 (A15), U3.32 (A15), U4.32 (A15), U5.32 (A15), U6.32 (A15), U7.32 (A15), U8.32 (A15), U9.32 (A15), U10.32 (A15), U11.32 (A15), U12.32 (A15), U13.32 (A15), U14.32 (A15), U15.32 (A15), U16.32 (A15), U17.32 (A15), U100.32 (A15)
DI0: P28.14, RR5.8, U1.95 (DI1_OD1), U2.95 (DI1_OD1), U3.95 (DI1_OD1), U4.95 (DI1_OD1), U5.95 (DI1_OD1), U6.95 (DI1_OD1), U7.95 (DI1_OD1), U8.95 (DI1_OD1), U9.95 (DI1_OD1), U10.95 (DI1_OD1), U11.95 (DI1_OD1), U12.95 (DI1_OD1), U13.95 (DI1_OD1), U14.95 (DI1_OD1), U15.95 (DI1_OD1), U16.95 (DI1_OD1), U17.95 (DI1_OD1), U100.95 (DI1_OD1)
DI1: P28.12, RR5.7, U1.94 (DI1_OD1), U2.94 (DI1_OD1), U3.94 (DI1_OD1), U4.94 (DI1_OD1), U5.94 (DI1_OD1), U6.94 (DI1_OD1), U7.94 (DI1_OD1), U8.94 (DI1_OD1), U9.94 (DI1_OD1), U10.94 (DI1_OD1), U11.94 (DI1_OD1), U12.94 (DI1_OD1), U13.94 (DI1_OD1), U14.94 (DI1_OD1), U15.94 (DI1_OD1), U16.94 (DI1_OD1), U17.94 (DI1_OD1), U100.94 (DI1_OD1)
DI2: P28.5, RR10.4, U1.41 (D12_OD2), U2.41 (D12_OD2), U3.41 (D12_OD2), U4.41 (D12_OD2), U5.41 (D12_OD2), U6.41 (D12_OD2), U7.41 (D12_OD2), U8.41 (D12_OD2), U9.41 (D12_OD2), U10.41 (D12_OD2), U11.41 (D12_OD2), U12.41 (D12_OD2), U13.41 (D12_OD2), U14.41 (D12_OD2), U15.41 (D12_OD2), U16.41 (D12_OD2), U17.41 (D12_OD2), U100.41 (D12_OD2)
DI3: P28.7, RR10.5, U1.42 (D13_OD3), U2.42 (D13_OD3), U3.42 (D13_OD3), U4.42 (D13_OD3), U5.42 (D13_OD3), U6.42 (D13_OD3), U7.42 (D13_OD3), U8.42 (D13_OD3), U9.42 (D13_OD3), U10.42 (D13_OD3), U11.42 (D13_OD3), U12.42 (D13_OD3), U13.42 (D13_OD3), U14.42 (D13_OD3), U15.42 (D13_OD3), U16.42 (D13_OD3), U17.42 (D13_OD3), U100.42 (D13_OD3)
DI4: P28.6, RR5.4, U1.91 (DI4_OD4), U2.91 (DI4_OD4), U3.91 (DI4_OD4), U4.91 (DI4_OD4), U5.91 (DI4_OD4), U6.91 (DI4_OD4), U7.91 (DI4_OD4), U8.91 (DI4_OD4), U9.91 (DI4_OD4), U10.91 (DI4_OD4), U11.91 (DI4_OD4), U12.91 (DI4_OD4), U13.91 (DI4_OD4), U14.91 (DI4_OD4), U15.91 (DI4_OD4), U16.91 (DI4_OD4), U17.91 (DI4_OD4), U100.91 (DI4_OD4)
DI5: P28.8, RR5.5, U1.92 (DI5_OD5), U2.92 (DI5_OD5), U3.92 (DI5_OD5), U4.92 (DI5_OD5), U5.92 (DI5_OD5), U6.92 (DI5_OD5), U7.92 (DI5_OD5), U8.92 (DI5_OD5), U9.92 (DI5_OD5), U10.92 (DI5_OD5), U11.92 (DI5_OD5), U12.92 (DI5_OD5), U13.92 (DI5_OD5), U14.92 (DI5_OD5), U15.92 (DI5_OD5), U16.92 (DI5_OD5), U17.92 (DI5_OD5), U100.92 (DI5_OD5)
DI6: P28.10, RR5.6, U1.93 (DI6_OD6), U2.93 (DI6_OD6), U3.93 (DI6_OD6), U4.93 (DI6_OD6), U5.93 (DI6_OD6), U6.93 (DI6_OD6), U7.93 (DI6_OD6), U8.93 (DI6_OD6), U9.93 (DI6_OD6), U10.93 (DI6_OD6), U11.93 (DI6_OD6), U12.93 (DI6_OD6), U13.93 (DI6_OD6), U14.93 (DI6_OD6), U15.93 (DI6_OD6), U16.93 (DI6_OD6), U17.93 (DI6_OD6), U100.93 (DI6_OD6)
DI7: P28.9, RR10.6, U1.43 (D17_OD7), U2.43 (D17_OD7), U3.43 (D17_OD7), U4.43 (D17_OD7), U5.43 (D17_OD7), U6.43 (D17_OD7), U7.43 (D17_OD7), U8.43 (D17_OD7), U9.43 (D17_OD7), U10.43 (D17_OD7), U11.43 (D17_OD7), U12.43 (D17_OD7), U13.43 (D17_OD7), U14.43 (D17_OD7), U15.43 (D17_OD7), U16.43 (D17_OD7), U17.43 (D17_OD7), U100.43 (D17_OD7)
DIG1(---): P25.16, RR1.6, U1.57 (TMA2*), U2.57 (TMA2*), U3.57 (TMA2*), U4.57 (TMA2*), U5.57 (TMA2*), U6.57 (TMA2*), U7.57 (TMA2*), U8.57 (TMA2*), U9.57 (TMA2*), U10.57 (TMA2*), U11.57 (TMA2*), U12.57 (TMA2*), U13.57 (TMA2*), U14.57 (TMA2*), U15.57 (TMA2*), U16.57 (TMA2*), U17.57 (TMA2*), U100.57 (TMA2*)
DO0: P27.21, RR9.8, U1.36 (DO0_ED0), U2.36 (DO0_ED0), U3.36 (DO0_ED0), U4.36 (DO0_ED0), U5.36 (DO0_ED0), U6.36 (DO0_ED0), U7.36 (DO0_ED0), U8.36 (DO0_ED0), U9.36 (DO0_ED0), U10.36 (DO0_ED0), U11.36 (DO0_ED0), U12.36 (DO0_ED0), U13.36 (DO0_ED0), U14.36 (DO0_ED0), U15.36 (DO0_ED0), U16.36 (DO0_ED0), U17.36 (DO0_ED0), U100.36 (DO0_ED0)
DO1: P27.19, RR4.7, U1.35 (DO1_ED1), U2.35 (DO1_ED1), U3.35 (DO1_ED1), U4.35 (DO1_ED1), U5.35 (DO1_ED1), U6.35 (DO1_ED1), U7.35 (DO1_ED1), U8.35 (DO1_ED1), U9.35 (DO1_ED1), U10.35 (DO1_ED1), U11.35 (DO1_ED1), U12.35 (DO1_ED1), U13.35 (DO1_ED1), U14.35 (DO1_ED1), U15.35 (DO1_ED1), U16.35 (DO1_ED1), U17.35 (DO1_ED1), U100.35 (DO1_ED1)
DO2: P27.26 (P22), RR4.10, U1.88 (DO2_ED2), U2.88 (DO2_ED2), U3.88 (DO2_ED2), U4.88 (DO2_ED2), U5.88 (DO2_ED2), U6.88 (DO2_ED2), U7.88 (DO2_ED2), U8.88 (DO2_ED2), U9.88 (DO2_ED2), U10.88 (DO2_ED2), U11.88 (DO2_ED2), U12.88 (DO2_ED2), U13.88 (DO2_ED2), U14.88 (DO2_ED2), U15.88 (DO2_ED2), U16.88 (DO2_ED2), U17.88 (DO2_ED2), U100.88 (DO2_ED2)
DO3: P28.2, RR5.2, U1.89 (DO3_ED3), U2.89 (DO3_ED3), U3.89 (DO3_ED3), U4.89 (DO3_ED3), U5.89 (DO3_ED3), U6.89 (DO3_ED3), U7.89 (DO3_ED3), U8.89 (DO3_ED3), U9.89 (DO3_ED3), U10.89 (DO3_ED3), U11.89 (DO3_ED3), U12.89 (DO3_ED3), U13.89 (DO3_ED3), U14.89 (DO3_ED3), U15.89 (DO3_ED3), U16.89 (DO3_ED3), U17.89 (DO3_ED3), U100.89 (DO3_ED3)
DO4: P27.25 (P24), RR9.10, U1.38 (DO4_ED4), U2.38 (DO4_ED4), U3.38 (DO4_ED4), U4.38 (DO4_ED4), U5.38 (DO4_ED4), U6.38 (DO4_ED4), U7.38 (DO4_ED4), U8.38 (DO4_ED4), U9.38 (DO4_ED4), U10.38 (DO4_ED4), U11.38 (DO4_ED4), U12.38 (DO4_ED4), U13.38 (DO4_ED4), U14.38 (DO4_ED4), U15.38 (DO4_ED4), U16.38 (DO4_ED4), U17.38 (DO4_ED4), U100.38 (DO4_ED4)
DO5: P28.1, RR10.2, U1.39 (DO5_ED5), U2.39 (DO5_ED5), U3.39 (DO5_ED5), U4.39 (DO5_ED5), U5.39 (DO5_ED5), U6.39 (DO5_ED5), U7.39 (DO5_ED5), U8.39 (DO5_ED5), U9.39 (DO5_ED5), U10.39 (DO5_ED5), U11.39 (DO5_ED5), U12.39 (DO5_ED5), U13.39 (DO5_ED5), U14.39 (DO5_ED5), U15.39 (DO5_ED5), U16.39 (DO5_ED5), U17.39 (DO5_ED5), U100.39 (DO5_ED5)
DO6: P28.3, RR10.3, U1.40 (DO6_ED6), U2.40 (DO6_ED6), U3.40 (DO6_ED6), U4.40 (DO6_ED6), U5.40 (DO6_ED6), U6.40 (DO6_ED6), U7.40 (DO6_ED6), U8.40 (DO6_ED6), U9.40 (DO6_ED6), U10.40 (DO6_ED6), U11.40 (DO6_ED6), U12.40 (DO6_ED6), U13.40 (DO6_ED6), U14.40 (DO6_ED6), U15.40 (DO6_ED6), U16.40 (DO6_ED6), U17.40 (DO6_ED6), U100.40 (DO6_ED6)
DO7: P28.4, RR5.3, U1.90 (DO7_ED7), U2.90 (DO7_ED7), U3.90 (DO7_ED7), U4.90 (DO7_ED7), U5.90 (DO7_ED7), U6.90 (DO7_ED7), U7.90 (DO7_ED7), U8.90 (DO7_ED7), U9.90 (DO7_ED7), U10.90 (DO7_ED7), U11.90 (DO7_ED7), U12.90 (DO7_ED7), U13.90 (DO7_ED7), U14.90 (DO7_ED7), U15.90 (DO7_ED7), U16.90 (DO7_ED7), U17.90 (DO7_ED7), U100.90 (DO7_ED7)
FRDY(---): P25.18, RR1.7, U1.58 (sXTRQ*), U2.58 (sXTRQ*), U3.58 (sXTRQ*), U4.58 (sXTRQ*), U5.58 (sXTRQ*), U6.58 (sXTRQ*), U7.58 (sXTRQ*), U8.58 (sXTRQ*), U9.58 (sXTRQ*), U10.58 (sXTRQ*), U11.58 (sXTRQ*), U12.58 (sXTRQ*), U13.58 (sXTRQ*), U14.58 (sXTRQ*), U15.58 (sXTRQ*), U16.58 (sXTRQ*), U17.58 (sXTRQ*), U100.58 (sXTRQ*)
GND: C1.2, C2.2, C3.2, C4.2, C5.2, C6.2, C7.2, C8.2, C9.2, C13.2, IC1.GND, JP1.1, JP2.1, JP3.1, P1.4, P2.1, P3.1, P4.1, P5.1, P6.1, P7.1, P8.1, P9.1, P10.1, P11.1, P12.2 (PM), P13.1, P14.1, P15.1, P16.1, P17.1, P18.1, P19.1, P20.1, P21.1, P22.1, P23.1, P24.1, P25.1, P25.2, P28.23, P28.24 (P20), P28.25 (P24), P28.26 (P22), Q2.1 (E), Q4.2 (C), Q13.1 (E), R2.2, R3.2, R8.2, R10.2, SW1.1, U1.50 (0_V2), U1.100 (0_V5), U2.50 (0_V2), U2.100 (0_V5), U3.50 (0_V2), U3.100 (0_V5), U4.50 (0_V2), U4.100 (0_V5), U5.50 (0_V2), U5.100 (0_V5), U6.50 (0_V2), U6.100 (0_V5), U7.50 (0_V2), U7.100 (0_V5), U8.50 (0_V2), U8.100 (0_V5), U9.50 (0_V2), U9.100 (0_V5), U10.50 (0_V2), U10.100 (0_V5), U11.50 (0_V2), U11.100 (0_V5), U12.50 (0_V2), U12.100 (0_V5), U13.50 (0_V2), U13.100 (0_V5), U14.50 (0_V2), U14.100 (0_V5), U15.50 (0_V2), U15.100 (0_V5), U16.50 (0_V2), U16.100 (0_V5), U17.50 (0_V2), U17.100 (0_V5), U23.7 (GND), U100.50 (0_V2), U100.100 (0_V5)
MWRT: P26.12, RR7.8, U1.68 (MWRT), U2.68 (MWRT), U3.68 (MWRT), U4.68 (MWRT), U5.68 (MWRT), U6.68 (MWRT), U7.68 (MWRT), U8.68 (MWRT), U9.68 (MWRT), U10.68 (MWRT), U11.68 (MWRT), U12.68 (MWRT), U13.68 (MWRT), U14.68 (MWRT), U15.68 (MWRT), U16.68 (MWRT), U17.68 (MWRT), U100.68 (MWRT)
unnamed: C2.1, IC2.3 (PLUS), R1.2
unnamed: C13.1, D1.1 (A), R15.1, R16.2, U23.1
unnamed: D12.1 (A), R47.1
unnamed: D12.2 (K), Q13.3 (C)
unnamed: IC2.2 (MINUS), R4.2
unnamed: IC2.4 (MINUS), Q2.2 (B), R3.1
unnamed: IC2.7 (PLUS), Q1.2 (B), R5.2
unnamed: IC2.8 (FIN), R2.1
unnamed: K1.2 (PM), U23.4
unnamed: P12.1, R15.2, SW1.2
unnamed: Q1.3 (C), Q3.1 (B), R6.1
unnamed: Q2.3 (C), Q4.1 (B), R7.2
unnamed: Q13.2 (B), R46.1
unnamed: R1.1, R9.1
unnamed: R1.3, R10.1
unnamed: U23.2, U23.3
PDBIN: P27.6, RR3.9, U1.78 (pDBIN), U2.78 (pDBIN), U3.78 (pDBIN), U4.78 (pDBIN), U5.78 (pDBIN), U6.78 (pDBIN), U7.78 (pDBIN), U8.78 (pDBIN), U9.78 (pDBIN), U10.78 (pDBIN), U11.78 (pDBIN), U12.78 (pDBIN), U13.78 (pDBIN), U14.78 (pDBIN), U15.78 (pDBIN), U16.78 (pDBIN), U17.78 (pDBIN), U100.78 (pDBIN)
PHLDA: P27.1, RR8.7, U1.26 (pHDLA), U2.26 (pHDLA), U3.26 (pHDLA), U4.26 (pHDLA), U5.26 (pHDLA), U6.26 (pHDLA), U7.26 (pHDLA), U8.26 (pHDLA), U9.26 (pHDLA), U10.26 (pHDLA), U11.26 (pHDLA), U12.26 (pHDLA), U13.26 (pHDLA), U14.26 (pHDLA), U15.26 (pHDLA), U16.26 (pHDLA), U17.26 (pHDLA), U100.26 (pHDLA)
PINTE: P27.5, RR8.9, U1.28 (RFU_2), U2.28 (RFU_2), U3.28 (RFU_2), U4.28 (RFU_2), U5.28 (RFU_2), U6.28 (RFU_2), U7.28 (RFU_2), U8.28 (RFU_2), U9.28 (RFU_2), U10.28 (RFU_2), U11.28 (RFU_2), U12.28 (RFU_2), U13.28 (RFU_2), U14.28 (RFU_2), U15.28 (RFU_2), U16.28 (RFU_2), U17.28 (RFU_2), U100.28 (RFU_2)
PRDY: P26.20, RR8.3, U1.72 (RDY), U2.72 (RDY), U3.72 (RDY), U4.72 (RDY), U5.72 (RDY), U6.72 (RDY), U7.72 (RDY), U8.72 (RDY), U9.72 (RDY), U10.72 (RDY), U11.72 (RDY), U12.72 (RDY), U13.72 (RDY), U14.72 (RDY), U15.72 (RDY), U16.72 (RDY), U17.72 (RDY), U100.72 (RDY)
PROT(GND): JP3.2, P26.16, RR7.10, U1.70 (0_V4), U2.70 (0_V4), U3.70 (0_V4), U4.70 (0_V4), U5.70 (0_V4), U6.70 (0_V4), U7.70 (0_V4), U8.70 (0_V4), U9.70 (0_V4), U10.70 (0_V4), U11.70 (0_V4), U12.70 (0_V4), U13.70 (0_V4), U14.70 (0_V4), U15.70 (0_V4), U16.70 (0_V4), U17.70 (0_V4), U100.70 (0_V4)
PSYNC: P27.2, RR3.7, U1.76 (pSYNC), U2.76 (pSYNC), U3.76 (pSYNC), U4.76 (pSYNC), U5.76 (pSYNC), U6.76 (pSYNC), U7.76 (pSYNC), U8.76 (pSYNC), U9.76 (pSYNC), U10.76 (pSYNC), U11.76 (pSYNC), U12.76 (pSYNC), U13.76 (pSYNC), U14.76 (pSYNC), U15.76 (pSYNC), U16.76 (pSYNC), U17.76 (pSYNC), U100.76 (pSYNC)
PWAIT: P27.3, RR8.8, U1.27 (RFU_1), U2.27 (RFU_1), U3.27 (RFU_1), U4.27 (RFU_1), U5.27 (RFU_1), U6.27 (RFU_1), U7.27 (RFU_1), U8.27 (RFU_1), U9.27 (RFU_1), U10.27 (RFU_1), U11.27 (RFU_1), U12.27 (RFU_1), U13.27 (RFU_1), U14.27 (RFU_1), U15.27 (RFU_1), U16.27 (RFU_1), U17.27 (RFU_1), U100.27 (RFU_1)
RTC(---): P25.12, RR1.4, U1.55 (TMA0*), U2.55 (TMA0*), U3.55 (TMA0*), U4.55 (TMA0*), U5.55 (TMA0*), U6.55 (TMA0*), U7.55 (TMA0*), U8.55 (TMA0*), U9.55 (TMA0*), U10.55 (TMA0*), U11.55 (TMA0*), U12.55 (TMA0*), U13.55 (TMA0*), U14.55 (TMA0*), U15.55 (TMA0*), U16.55 (TMA0*), U17.55 (TMA0*), U100.55 (TMA0*)
RUN: P26.18, RR8.2, U1.71 (RFU4), U2.71 (RFU4), U3.71 (RFU4), U4.71 (RFU4), U5.71 (RFU4), U6.71 (RFU4), U7.71 (RFU4), U8.71 (RFU4), U9.71 (RFU4), U10.71 (RFU4), U11.71 (RFU4), U12.71 (RFU4), U13.71 (RFU4), U14.71 (RFU4), U15.71 (RFU4), U16.71 (RFU4), U17.71 (RFU4), U100.71 (RFU4)
SHLTA: P28.19, R11.1, U1.48 (sHLTA), U2.48 (sHLTA), U3.48 (sHLTA), U4.48 (sHLTA), U5.48 (sHLTA), U6.48 (sHLTA), U7.48 (sHLTA), U8.48 (sHLTA), U9.48 (sHLTA), U10.48 (sHLTA), U11.48 (sHLTA), U12.48 (sHLTA), U13.48 (sHLTA), U14.48 (sHLTA), U15.48 (sHLTA), U16.48 (sHLTA), U17.48 (sHLTA), U100.48 (sHLTA)
SINP: P28.15, RR10.9, U1.46 (sINP), U2.46 (sINP), U3.46 (sINP), U4.46 (sINP), U5.46 (sINP), U6.46 (sINP), U7.46 (sINP), U8.46 (sINP), U9.46 (sINP), U10.46 (sINP), U11.46 (sINP), U12.46 (sINP), U13.46 (sINP), U14.46 (sINP), U15.46 (sINP), U16.46 (sINP), U17.46 (sINP), U100.46 (sINP)
SINTA: P28.16, RR5.9, U1.96 (sINTA), U2.96 (sINTA), U3.96 (sINTA), U4.96 (sINTA), U5.96 (sINTA), U6.96 (sINTA), U7.96 (sINTA), U8.96 (sINTA), U9.96 (sINTA), U10.96 (sINTA), U11.96 (sINTA), U12.96 (sINTA), U13.96 (sINTA), U14.96 (sINTA), U15.96 (sINTA), U16.96 (sINTA), U17.96 (sINTA), U100.96 (sINTA)
SM1: P28.11, RR10.7, U1.44 (sM1), U2.44 (sM1), U3.44 (sM1), U4.44 (sM1), U5.44 (sM1), U6.44 (sM1), U7.44 (sM1), U8.44 (sM1), U9.44 (sM1), U10.44 (sM1), U11.44 (sM1), U12.44 (sM1), U13.44 (sM1), U14.44 (sM1), U15.44 (sM1), U16.44 (sM1), U17.44 (sM1), U100.44 (sM1)
SMEMR: P28.17, RR10.10, U1.47 (sMEMR), U2.47 (sMEMR), U3.47 (sMEMR), U4.47 (sMEMR), U5.47 (sMEMR), U6.47 (sMEMR), U7.47 (sMEMR), U8.47 (sMEMR), U9.47 (sMEMR), U10.47 (sMEMR), U11.47 (sMEMR), U12.47 (sMEMR), U13.47 (sMEMR), U14.47 (sMEMR), U15.47 (sMEMR), U16.47 (sMEMR), U17.47 (sMEMR), U100.47 (sMEMR)
SOUT: P28.13, RR10.8, U1.45 (sOUT), U2.45 (sOUT), U3.45 (sOUT), U4.45 (sOUT), U5.45 (sOUT), U6.45 (sOUT), U7.45 (sOUT), U8.45 (sOUT), U9.45 (sOUT), U10.45 (sOUT), U11.45 (sOUT), U12.45 (sOUT), U13.45 (sOUT), U14.45 (sOUT), U15.45 (sOUT), U16.45 (sOUT), U17.45 (sOUT), U100.45 (sOUT)
SS: P26.17, RR3.2, U1.21 (NDEF1), U2.21 (NDEF1), U3.21 (NDEF1), U4.21 (NDEF1), U5.21 (NDEF1), U6.21 (NDEF1), U7.21 (NDEF1), U8.21 (NDEF1), U9.21 (NDEF1), U10.21 (NDEF1), U11.21 (NDEF1), U12.21 (NDEF1), U13.21 (NDEF1), U14.21 (NDEF1), U15.21 (NDEF1), U16.21 (NDEF1), U17.21 (NDEF1), U100.21 (NDEF1)
SSTACK: P28.20, R13.1, U1.98 (ERROR*), U2.98 (ERROR*), U3.98 (ERROR*), U4.98 (ERROR*), U5.98 (ERROR*), U6.98 (ERROR*), U7.98 (ERROR*), U8.98 (ERROR*), U9.98 (ERROR*), U10.98 (ERROR*), U11.98 (ERROR*), U12.98 (ERROR*), U13.98 (ERROR*), U14.98 (ERROR*), U15.98 (ERROR*), U16.98 (ERROR*), U17.98 (ERROR*), U100.98 (ERROR*)
UNPROT(T5): JP1.2, P26.15, RR2.10, U1.20 (0_V1), U2.20 (0_V1), U3.20 (0_V1), U4.20 (0_V1), U5.20 (0_V1), U6.20 (0_V1), U7.20 (0_V1), U8.20 (0_V1), U9.20 (0_V1), U10.20 (0_V1), U11.20 (0_V1), U12.20 (0_V1), U13.20 (0_V1), U14.20 (0_V1), U15.20 (0_V1), U16.20 (0_V1), U17.20 (0_V1), U100.20 (0_V1)
V5.0: C9.1, D1.2 (K), IC1.VO, R9.2, R16.1, R46.2, R47.2, U23.14 (VCC)
VI_0: P25.9, RR6.3, U1.4 (VIO*), U2.4 (VIO*), U3.4 (VIO*), U4.4 (VIO*), U5.4 (VIO*), U6.4 (VIO*), U7.4 (VIO*), U8.4 (VIO*), U9.4 (VIO*), U10.4 (VIO*), U11.4 (VIO*), U12.4 (VIO*), U13.4 (VIO*), U14.4 (VIO*), U15.4 (VIO*), U16.4 (VIO*), U17.4 (VIO*), U100.4 (VIO*)
VI_1: P25.11, RR6.4, U1.5 (VI1*), U2.5 (VI1*), U3.5 (VI1*), U4.5 (VI1*), U5.5 (VI1*), U6.5 (VI1*), U7.5 (VI1*), U8.5 (VI1*), U9.5 (VI1*), U10.5 (VI1*), U11.5 (VI1*), U12.5 (VI1*), U13.5 (VI1*), U14.5 (VI1*), U15.5 (VI1*), U16.5 (VI1*), U17.5 (VI1*), U100.5 (VI1*)
VI_2: P25.13, RR6.5, U1.6 (VI2*), U2.6 (VI2*), U3.6 (VI2*), U4.6 (VI2*), U5.6 (VI2*), U6.6 (VI2*), U7.6 (VI2*), U8.6 (VI2*), U9.6 (VI2*), U10.6 (VI2*), U11.6 (VI2*), U12.6 (VI2*), U13.6 (VI2*), U14.6 (VI2*), U15.6 (VI2*), U16.6 (VI2*), U17.6 (VI2*), U100.6 (VI2*)
VI_3: P25.15, RR6.6, U1.7 (VI3*), U2.7 (VI3*), U3.7 (VI3*), U4.7 (VI3*), U5.7 (VI3*), U6.7 (VI3*), U7.7 (VI3*), U8.7 (VI3*), U9.7 (VI3*), U10.7 (VI3*), U11.7 (VI3*), U12.7 (VI3*), U13.7 (VI3*), U14.7 (VI3*), U15.7 (VI3*), U16.7 (VI3*), U17.7 (VI3*), U100.7 (VI3*)
VI_4: P25.17, RR6.7, U1.8 (VI4*), U2.8 (VI4*), U3.8 (VI4*), U4.8 (VI4*), U5.8 (VI4*), U6.8 (VI4*), U7.8 (VI4*), U8.8 (VI4*), U9.8 (VI4*), U10.8 (VI4*), U11.8 (VI4*), U12.8 (VI4*), U13.8 (VI4*), U14.8 (VI4*), U15.8 (VI4*), U16.8 (VI4*), U17.8 (VI4*), U100.8 (VI4*)
VI_5: P25.19, RR6.8, U1.9 (VI5*), U2.9 (VI5*), U3.9 (VI5*), U4.9 (VI5*), U5.9 (VI5*), U6.9 (VI5*), U7.9 (VI5*), U8.9 (VI5*), U9.9 (VI5*), U10.9 (VI5*), U11.9 (VI5*), U12.9 (VI5*), U13.9 (VI5*), U14.9 (VI5*), U15.9 (VI5*), U16.9 (VI5*), U17.9 (VI5*), U100.9 (VI5*)
VI_6: P25.21, RR6.9, U1.10 (VI6*), U2.10 (VI6*), U3.10 (VI6*), U4.10 (VI6*), U5.10 (VI6*), U6.10 (VI6*), U7.10 (VI6*), U8.10 (VI6*), U9.10 (VI6*), U10.10 (VI6*), U11.10 (VI6*), U12.10 (VI6*), U13.10 (VI6*), U14.10 (VI6*), U15.10 (VI6*), U16.10 (VI6*), U17.10 (VI6*), U100.10 (VI6*)
VI_7: P25.23, RR6.10, U1.11 (VI7*), U2.11 (VI7*), U3.11 (VI7*), U4.11 (VI7*), U5.11 (VI7*), U6.11 (VI7*), U7.11 (VI7*), U8.11 (VI7*), U9.11 (VI7*), U10.11 (VI7*), U11.11 (VI7*), U12.11 (VI7*), U13.11 (VI7*), U14.11 (VI7*), U15.11 (VI7*), U16.11 (VI7*), U17.11 (VI7*), U100.11 (VI7*)
Vacc: C3.1, C4.1, C5.1, C6.1, C7.1, IC2.6 (OUTPUT), Q3.3 (E), Q4.3 (E), R4.1, R6.2, R7.1, R8.1, R11.2, R12.2, R13.2, R14.2, RR1.1 (COM), RR2.1 (COM), RR3.1 (COM), RR4.1 (COM), RR5.1 (COM), RR6.1 (COM), RR7.1 (COM), RR8.1 (COM), RR9.1 (COM), RR10.1 (COM)
XRDY: P25.7, RR6.2, U1.3 (XRDY), U2.3 (XRDY), U3.3 (XRDY), U4.3 (XRDY), U5.3 (XRDY), U6.3 (XRDY), U7.3 (XRDY), U8.3 (XRDY), U9.3 (XRDY), U10.3 (XRDY), U11.3 (XRDY), U12.3 (XRDY), U13.3 (XRDY), U14.3 (XRDY), U15.3 (XRDY), U16.3 (XRDY), U17.3 (XRDY), U100.3 (XRDY)
phi1: P26.25 (P24), RR3.6, U1.25 (pSTVAL*), U2.25 (pSTVAL*), U3.25 (pSTVAL*), U4.25 (pSTVAL*), U5.25 (pSTVAL*), U6.25 (pSTVAL*), U7.25 (pSTVAL*), U8.25 (pSTVAL*), U9.25 (pSTVAL*), U10.25 (pSTVAL*), U11.25 (pSTVAL*), U12.25 (pSTVAL*), U13.25 (pSTVAL*), U14.25 (pSTVAL*), U15.25 (pSTVAL*), U16.25 (pSTVAL*), U17.25 (pSTVAL*), U100.25 (pSTVAL*)
phi2: P26.23, RR3.5, U1.24 (PHI), U2.24 (PHI), U3.24 (PHI), U4.24 (PHI), U5.24 (PHI), U6.24 (PHI), U7.24 (PHI), U8.24 (PHI), U9.24 (PHI), U10.24 (PHI), U11.24 (PHI), U12.24 (PHI), U13.24 (PHI), U14.24 (PHI), U15.24 (PHI), U16.24 (PHI), U17.24 (PHI), U100.24 (PHI)
pin_12: P25.25 (P24), RR2.2, U1.12 (NMI*), U2.12 (NMI*), U3.12 (NMI*), U4.12 (NMI*), U5.12 (NMI*), U6.12 (NMI*), U7.12 (NMI*), U8.12 (NMI*), U9.12 (NMI*), U10.12 (NMI*), U11.12 (NMI*), U12.12 (NMI*), U13.12 (NMI*), U14.12 (NMI*), U15.12 (NMI*), U16.12 (NMI*), U17.12 (NMI*), U100.12 (NMI*)
pin_13: P26.1, RR2.3, U1.13 (PWRFAIL*), U2.13 (PWRFAIL*), U3.13 (PWRFAIL*), U4.13 (PWRFAIL*), U5.13 (PWRFAIL*), U6.13 (PWRFAIL*), U7.13 (PWRFAIL*), U8.13 (PWRFAIL*), U9.13 (PWRFAIL*), U10.13 (PWRFAIL*), U11.13 (PWRFAIL*), U12.13 (PWRFAIL*), U13.13 (PWRFAIL*), U14.13 (PWRFAIL*), U15.13 (PWRFAIL*), U16.13 (PWRFAIL*), U17.13 (PWRFAIL*), U100.13 (PWRFAIL*)
pin_14: P26.3, RR2.4, U1.14 (TMA3*), U2.14 (TMA3*), U3.14 (TMA3*), U4.14 (TMA3*), U5.14 (TMA3*), U6.14 (TMA3*), U7.14 (TMA3*), U8.14 (TMA3*), U9.14 (TMA3*), U10.14 (TMA3*), U11.14 (TMA3*), U12.14 (TMA3*), U13.14 (TMA3*), U14.14 (TMA3*), U15.14 (TMA3*), U16.14 (TMA3*), U17.14 (TMA3*), U100.14 (TMA3*)
pin_15: P26.5, RR2.5, U1.15 (A18), U2.15 (A18), U3.15 (A18), U4.15 (A18), U5.15 (A18), U6.15 (A18), U7.15 (A18), U8.15 (A18), U9.15 (A18), U10.15 (A18), U11.15 (A18), U12.15 (A18), U13.15 (A18), U14.15 (A18), U15.15 (A18), U16.15 (A18), U17.15 (A18), U100.15 (A18)
pin_16: P26.7, RR2.6, U1.16 (A16), U2.16 (A16), U3.16 (A16), U4.16 (A16), U5.16 (A16), U6.16 (A16), U7.16 (A16), U8.16 (A16), U9.16 (A16), U10.16 (A16), U11.16 (A16), U12.16 (A16), U13.16 (A16), U14.16 (A16), U15.16 (A16), U16.16 (A16), U17.16 (A16), U100.16 (A16)
pin_17: P26.9, RR2.7, U1.17 (A17), U2.17 (A17), U3.17 (A17), U4.17 (A17), U5.17 (A17), U6.17 (A17), U7.17 (A17), U8.17 (A17), U9.17 (A17), U10.17 (A17), U11.17 (A17), U12.17 (A17), U13.17 (A17), U14.17 (A17), U15.17 (A17), U16.17 (A17), U17.17 (A17), U100.17 (A17)
pin_59: P25.20, RR1.8, U1.59 (A19), U2.59 (A19), U3.59 (A19), U4.59 (A19), U5.59 (A19), U6.59 (A19), U7.59 (A19), U8.59 (A19), U9.59 (A19), U10.59 (A19), U11.59 (A19), U12.59 (A19), U13.59 (A19), U14.59 (A19), U15.59 (A19), U16.59 (A19), U17.59 (A19), U100.59 (A19)
pin_60: P25.22, RR1.9, U1.60 (SIXTN*), U2.60 (SIXTN*), U3.60 (SIXTN*), U4.60 (SIXTN*), U5.60 (SIXTN*), U6.60 (SIXTN*), U7.60 (SIXTN*), U8.60 (SIXTN*), U9.60 (SIXTN*), U10.60 (SIXTN*), U11.60 (SIXTN*), U12.60 (SIXTN*), U13.60 (SIXTN*), U14.60 (SIXTN*), U15.60 (SIXTN*), U16.60 (SIXTN*), U17.60 (SIXTN*), U100.60 (SIXTN*)
pin_61: P25.24 (P20), RR1.10, U1.61 (A20), U2.61 (A20), U3.61 (A20), U4.61 (A20), U5.61 (A20), U6.61 (A20), U7.61 (A20), U8.61 (A20), U9.61 (A20), U10.61 (A20), U11.61 (A20), U12.61 (A20), U13.61 (A20), U14.61 (A20), U15.61 (A20), U16.61 (A20), U17.61 (A20), U100.61 (A20)
pin_62: P25.26 (P22), RR7.2, U1.62 (A21), U2.62 (A21), U3.62 (A21), U4.62 (A21), U5.62 (A21), U6.62 (A21), U7.62 (A21), U8.62 (A21), U9.62 (A21), U10.62 (A21), U11.62 (A21), U12.62 (A21), U13.62 (A21), U14.62 (A21), U15.62 (A21), U16.62 (A21), U17.62 (A21), U100.62 (A21)
pin_63: P26.2, RR7.3, U1.63 (A22), U2.63 (A22), U3.63 (A22), U4.63 (A22), U5.63 (A22), U6.63 (A22), U7.63 (A22), U8.63 (A22), U9.63 (A22), U10.63 (A22), U11.63 (A22), U12.63 (A22), U13.63 (A22), U14.63 (A22), U15.63 (A22), U16.63 (A22), U17.63 (A22), U100.63 (A22)
pin_64: P26.4, RR7.4, U1.64 (A23), U2.64 (A23), U3.64 (A23), U4.64 (A23), U5.64 (A23), U6.64 (A23), U7.64 (A23), U8.64 (A23), U9.64 (A23), U10.64 (A23), U11.64 (A23), U12.64 (A23), U13.64 (A23), U14.64 (A23), U15.64 (A23), U16.64 (A23), U17.64 (A23), U100.64 (A23)
pin_65: P26.6, RR7.5, U1.65 (NDEF2), U2.65 (NDEF2), U3.65 (NDEF2), U4.65 (NDEF2), U5.65 (NDEF2), U6.65 (NDEF2), U7.65 (NDEF2), U8.65 (NDEF2), U9.65 (NDEF2), U10.65 (NDEF2), U11.65 (NDEF2), U12.65 (NDEF2), U13.65 (NDEF2), U14.65 (NDEF2), U15.65 (NDEF2), U16.65 (NDEF2), U17.65 (NDEF2), U100.65 (NDEF2)
pin_66: P26.8, RR7.6, U1.66 (NDEF3), U2.66 (NDEF3), U3.66 (NDEF3), U4.66 (NDEF3), U5.66 (NDEF3), U6.66 (NDEF3), U7.66 (NDEF3), U8.66 (NDEF3), U9.66 (NDEF3), U10.66 (NDEF3), U11.66 (NDEF3), U12.66 (NDEF3), U13.66 (NDEF3), U14.66 (NDEF3), U15.66 (NDEF3), U16.66 (NDEF3), U17.66 (NDEF3), U100.66 (NDEF3)

Notes on the sheet:
MOUNTING HOLES
POWER CONNECTOR
LOGO(s)
Pin 54 on S100 Connector
Pin 75 on S100 Connector
NPN TO-220 1=B 2=C 3=E 4=C
PNP TO-220 1=B 2=C 3=E 4=C
Reset Circuit
POWER
POWER ON LED
