CatspersCoffee/S100-Boards/SRAM-8MB/rev1/s100_SRAM.sch

## KiCad design SRAM-8MB/rev1/s100_SRAM.sch (2014-03-23, an earlier design)

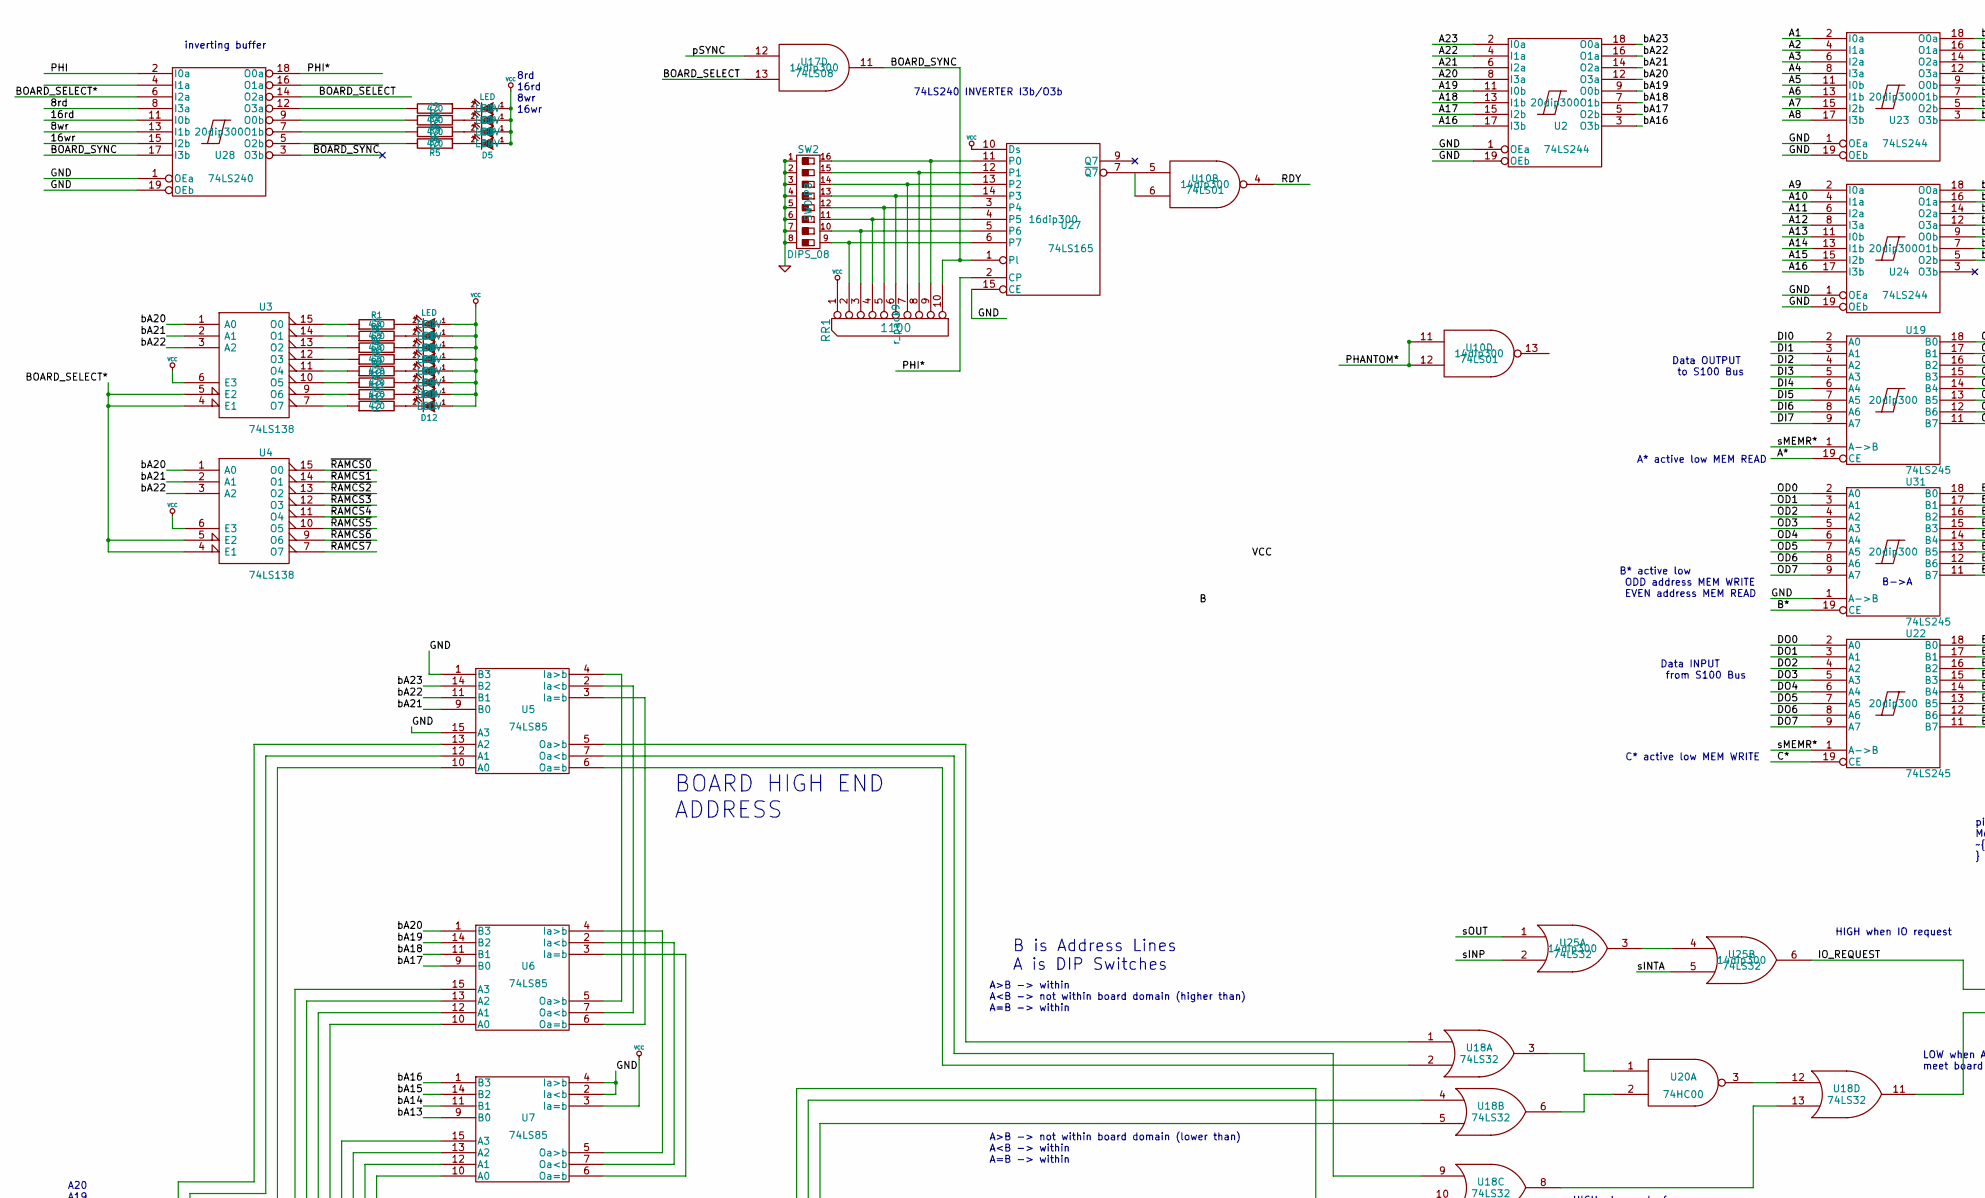
[picture p62: schematic s100_SRAM.sch, part in row 1, column 1]

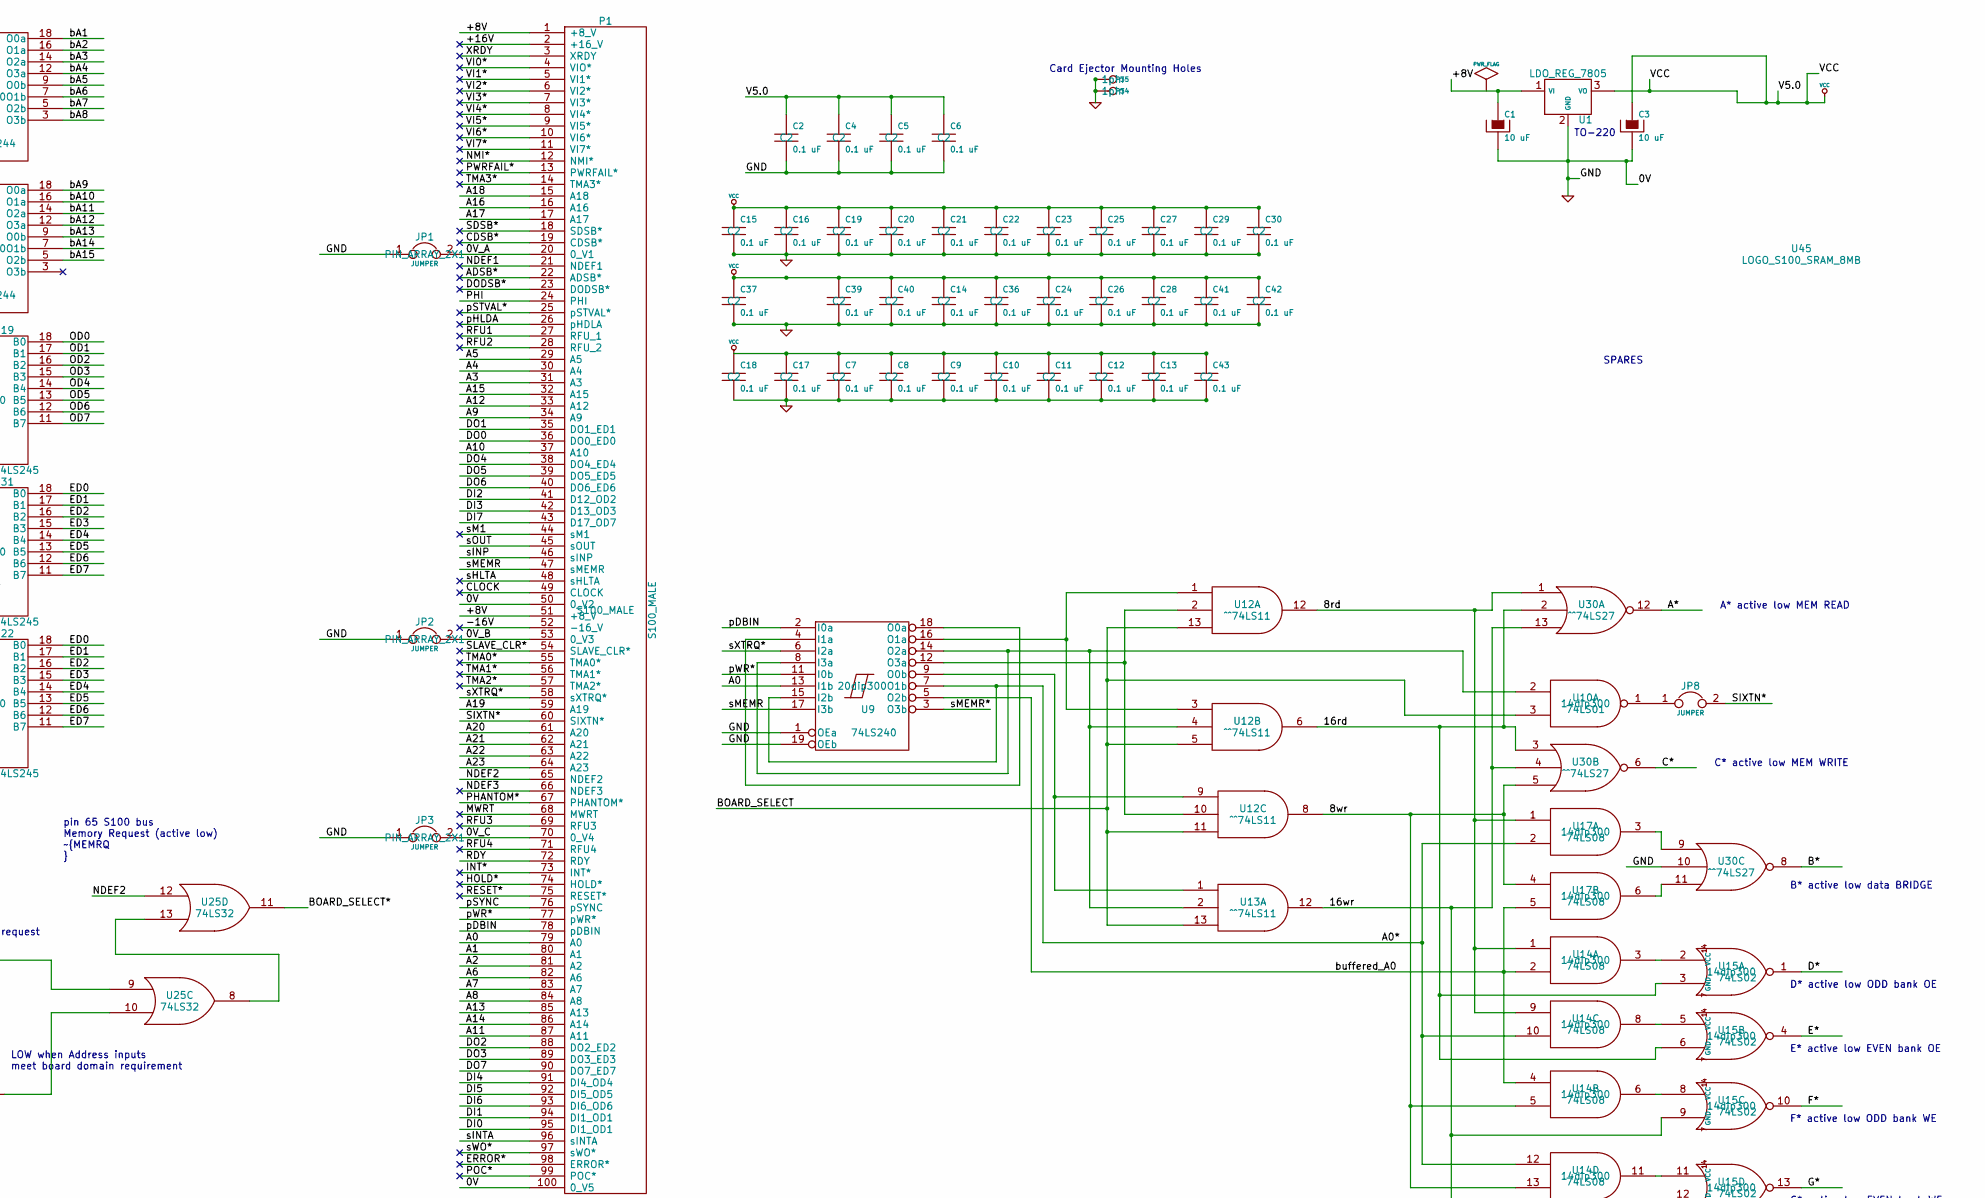
[picture p63: schematic s100_SRAM.sch, part in row 1, column 2]

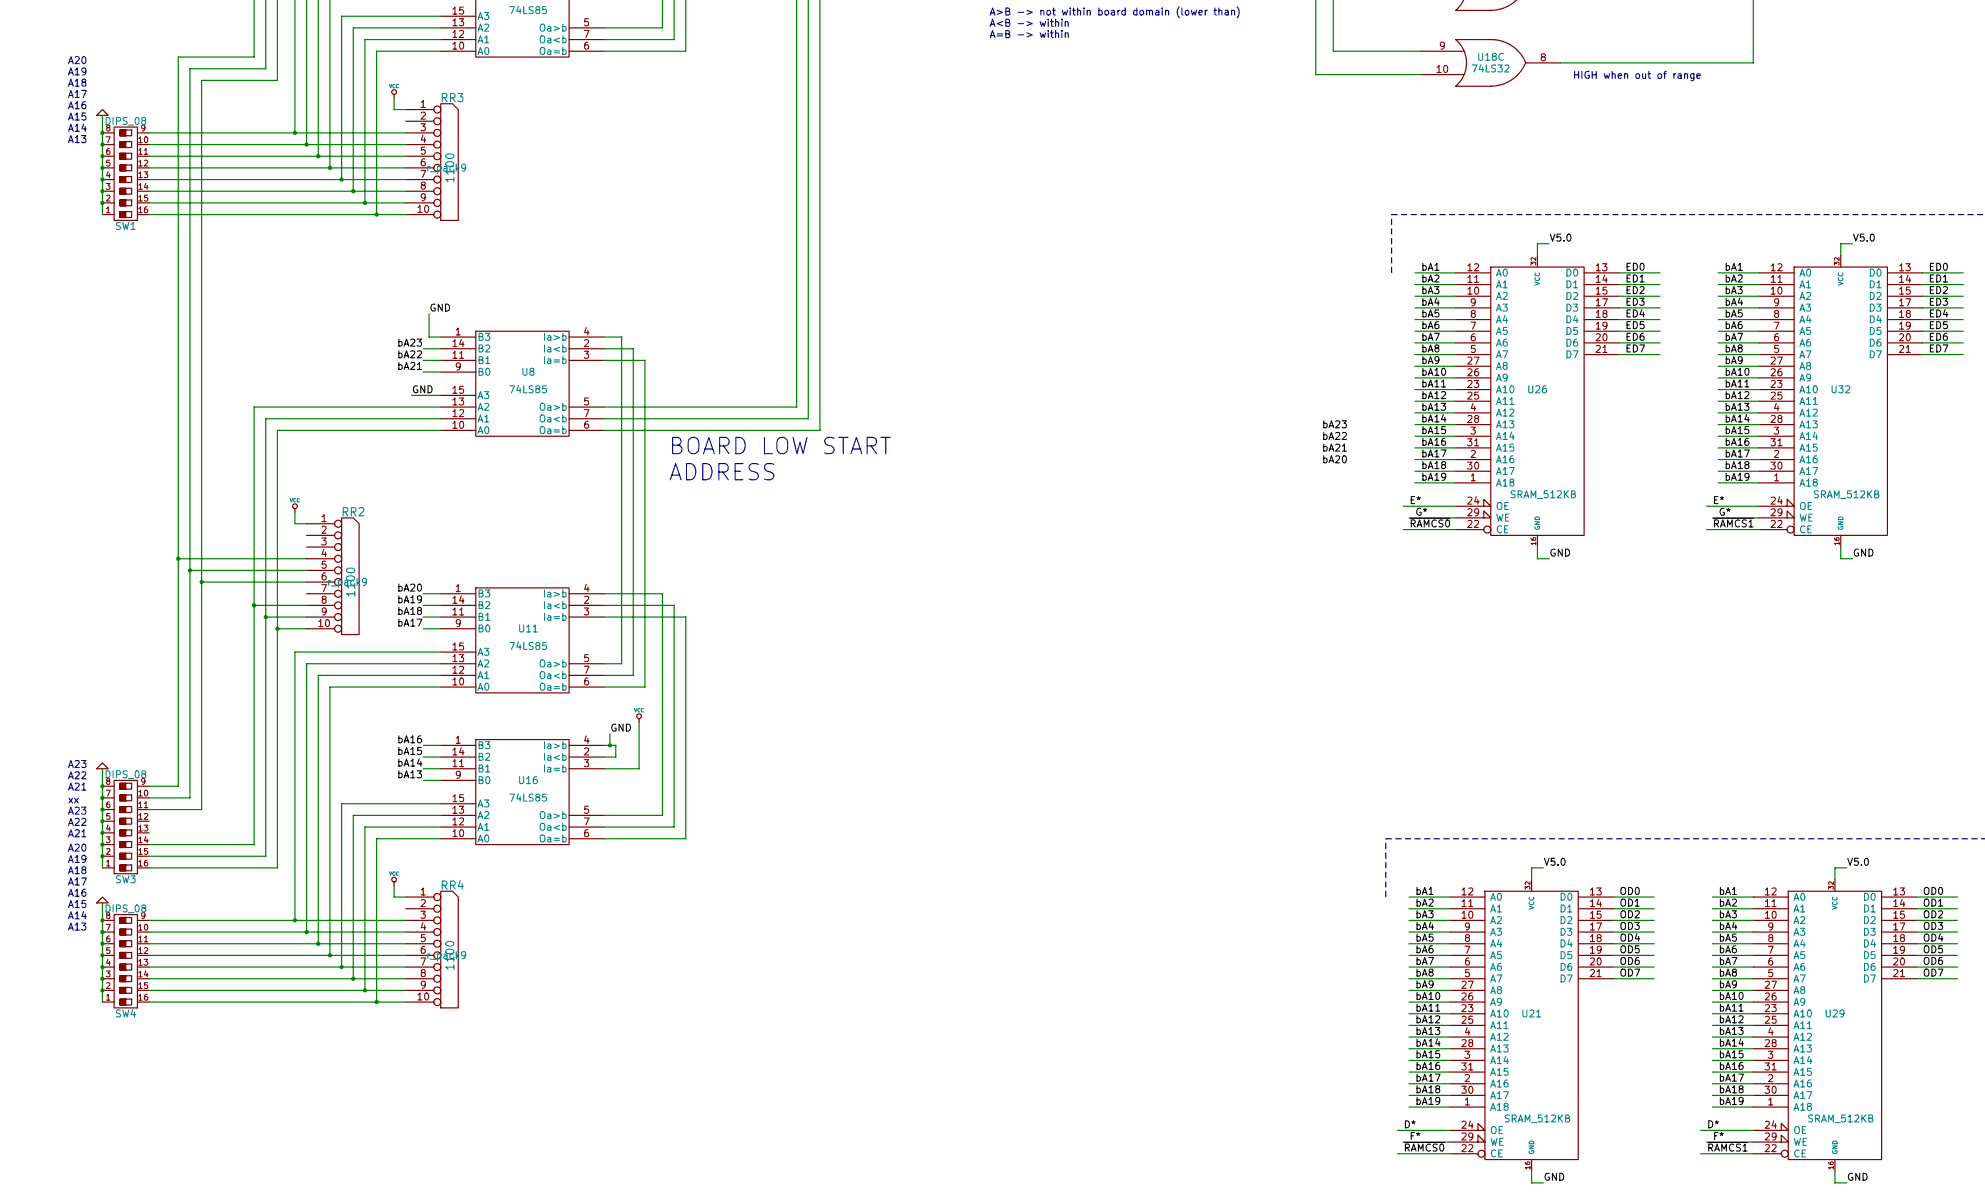
[picture p64: schematic s100_SRAM.sch, part in row 2, column 1]

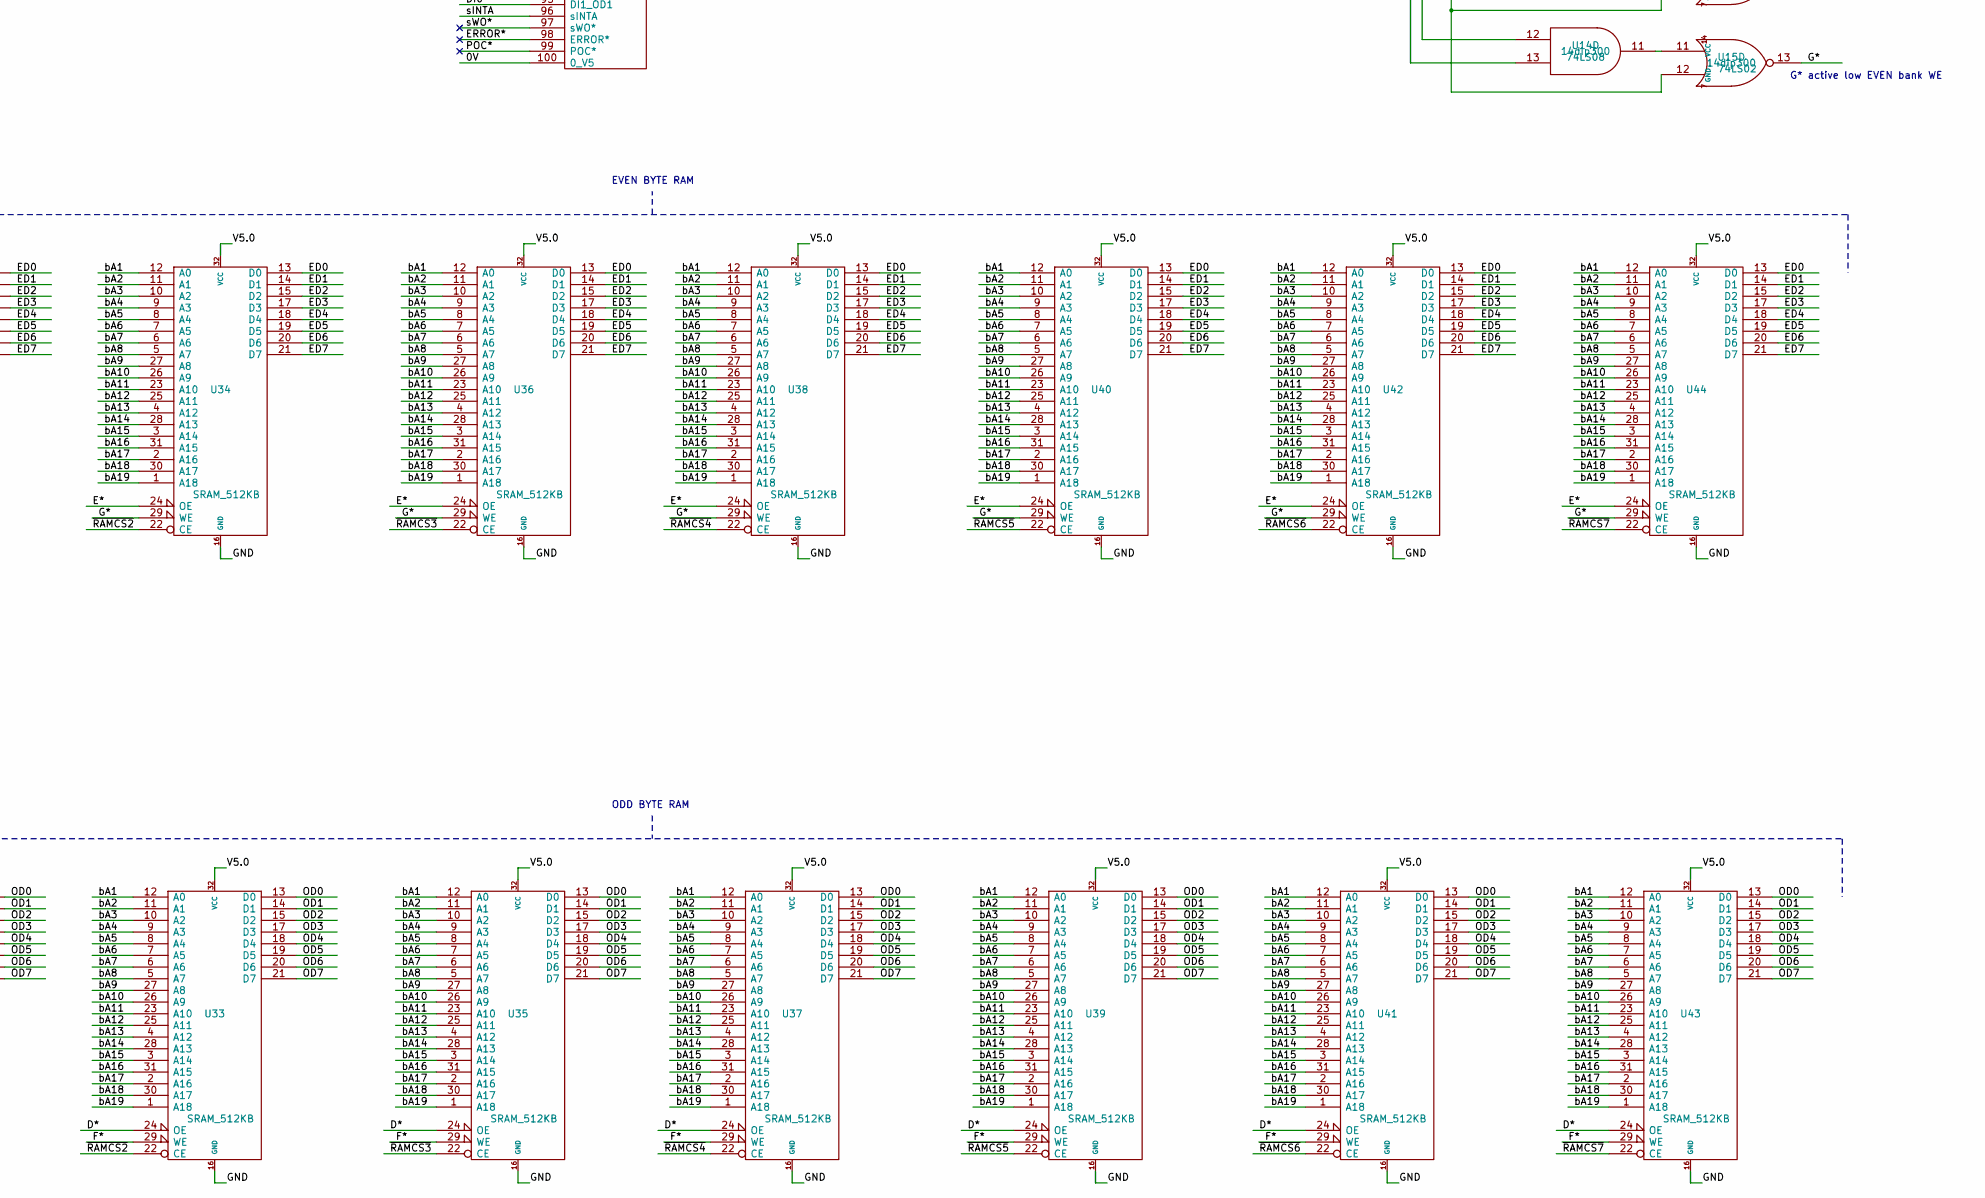
[picture p65: schematic s100_SRAM.sch, part in row 2, column 2]

Parts:
0.1: 0.1 uF; C2
C1, C3: 10 uF
C2, C4, C5, C6, C7, C8, C9, C10, C11, C12, C13, C14, C15, C16, C18, C19, C20, C21, C22, C23, C24, C25, C26, C27, C28, C29, C30, C36, C37, C39, C40, C41, C42, C43: 0.1 uF; C2
D1, D2, D3, D4, D5, D6, D7, D8, D9, D10, D11, D12: LED; LEDV
JP1, JP2, JP3: JUMPER; PIN_ARRAY_2X1
JP8: JUMPER
P1: S100_MALE
P34, P35: CONN_1; 1pin
R1, R2, R3, R4, R5, R6, R7, R8, R9, R10, R11, R12: 470; R3
RR1, RR2, RR3, RR4: 1100; r_pack9
SW1, SW3, SW4: DIPS_08; 16dip300
SW2: DIPS_08; SWDIP8
U: 74LS240; 20dip300
U1: LDO_REG_7805
U2, U23, U24: 74LS244; 20dip300
U3, U4: 74LS138
U5, U6, U7, U8, U11, U16: 74LS85
U10: 74LS01; 14dip300
U12, U13: ^^74LS11
U14: 74LS08; 14dip300
U15: 74LS02; 14dip300
U18: 74LS32
U19, U22, U31: 74LS245; 20dip300
U20: 74HC00
U21, U26, U29, U32, U33, U34, U35, U36, U37, U38, U39, U40, U41, U42, U43, U44: SRAM_512KB
U25: 74LS32; 14dip300
U27: 74LS165; 16dip300
U30: ^^74LS27
U45: LOGO_S100_SRAM_8MB

Connections:
0V_A: JP1.2, P1.20 (0_V1)
0V_B: JP2.2, P1.53 (0_V3)
0V_C: JP3.2, P1.70 (0_V4)
8rd: U.1, U.8, U.9, U12.12, U30.1
8wr: U.4, U.5, U.13, U12.8, U14.13, U30.5
16rd: U.3, U.6, U.11, U12.6, U30.2, U30.3
16wr: U.12, U.15 (I2b), U13.12, U15.9, U30.4, U30.13
+8V: C1.1, P1.1 (+8_V), P1.51 (+8_V), U1.1 (VI)
+16V: P1.2 (+16_V)
-16V: P1.52 (-16_V)
A0: P1.79 (A0), U.13
A0*: U.2, U.7 (GND), U.10, U.15 (I2b), U14.12
A1: P1.80 (A1), U23.2 (I0a)
A2: P1.81 (A2), U23.4 (I1a)
A3: P1.31 (A3), U23.6 (I2a)
A4: P1.30 (A4), U23.8 (I3a)
A5: P1.29 (A5), U23.11 (I0b)
A6: P1.82 (A6), U23.13 (I1b)
A7: P1.83 (A7), U23.15 (I2b)
A8: P1.84 (A8), U23.17 (I3b)
A9: P1.34 (A9), U24.2 (I0a)
A10: P1.37 (A10), U24.4 (I1a)
A11: P1.87 (A11), U24.6 (I2a)
A12: P1.33 (A12), U24.8 (I3a)
A13: P1.85 (A13), U24.11 (I0b)
A14: P1.86 (A14), U24.13 (I1b)
A15: P1.32 (A15), U24.15 (I2b)
A16: P1.16 (A16), U2.17 (I3b), U24.17 (I3b)
A17: P1.17 (A17), U2.15 (I2b)
A18: P1.15 (A18), U2.13 (I1b)
A19: P1.59 (A19), U2.11 (I0b)
A20: P1.61 (A20), U2.8 (I3a)
A21: P1.62 (A21), U2.6 (I2a)
A22: P1.63 (A22), U2.4 (I1a)
A23: P1.64 (A23), U2.2 (I0a)
A*: U19.19 (CE), U30.12
ADSB*: P1.22 (ADSB*)
B*: U30.8, U31.19 (CE)
BOARD_SELECT: U.13, U.14 (VCC), U10.3, U12.5, U12.11, U12.13, U13.13
BOARD_SELECT*: U.6, U3.4 (E1), U3.5 (E2), U4.4 (E1), U4.5 (E2), U25.11
BOARD_SYNC: RR1.10, U.11, U.17 (I3b), U27.1 (Pl)
C*: U22.19 (CE), U30.6
CDSB*: P1.19 (CDSB*)
CLOCK: P1.49 (CLOCK)
D*: U.1, U21.24 (OE), U29.24 (OE), U33.24 (OE), U35.24 (OE), U37.24 (OE), U39.24 (OE), U41.24 (OE), U43.24 (OE)
DI0: P1.95 (DI1_OD1), U19.2 (A0)
DI1: P1.94 (DI1_OD1), U19.3 (A1)
DI2: P1.41 (D12_OD2), U19.4 (A2)
DI3: P1.42 (D13_OD3), U19.5 (A3)
DI4: P1.91 (DI4_OD4), U19.6 (A4)
DI5: P1.92 (DI5_OD5), U19.7 (A5)
DI6: P1.93 (DI6_OD6), U19.8 (A6)
DI7: P1.43 (D17_OD7), U19.9 (A7)
DO0: P1.36 (DO0_ED0), U22.2 (A0)
DO1: P1.35 (DO1_ED1), U22.3 (A1)
DO2: P1.88 (DO2_ED2), U22.4 (A2)
DO3: P1.89 (DO3_ED3), U22.5 (A3)
DO4: P1.38 (DO4_ED4), U22.6 (A4)
DO5: P1.39 (DO5_ED5), U22.7 (A5)
DO6: P1.40 (DO6_ED6), U22.8 (A6)
DO7: P1.90 (DO7_ED7), U22.9 (A7)
DODSB*: P1.23 (DODSB*)
E*: U.4, U26.24 (OE), U32.24 (OE), U34.24 (OE), U36.24 (OE), U38.24 (OE), U40.24 (OE), U42.24 (OE), U44.24 (OE)
ED0: U22.18 (B0), U26.13 (D0), U31.18 (B0), U32.13 (D0), U34.13 (D0), U36.13 (D0), U38.13 (D0), U40.13 (D0), U42.13 (D0), U44.13 (D0)
ED1: U22.17 (B1), U26.14 (D1), U31.17 (B1), U32.14 (D1), U34.14 (D1), U36.14 (D1), U38.14 (D1), U40.14 (D1), U42.14 (D1), U44.14 (D1)
ED2: U22.16 (B2), U26.15 (D2), U31.16 (B2), U32.15 (D2), U34.15 (D2), U36.15 (D2), U38.15 (D2), U40.15 (D2), U42.15 (D2), U44.15 (D2)
ED3: U22.15 (B3), U26.17 (D3), U31.15 (B3), U32.17 (D3), U34.17 (D3), U36.17 (D3), U38.17 (D3), U40.17 (D3), U42.17 (D3), U44.17 (D3)
ED4: U22.14 (B4), U26.18 (D4), U31.14 (B4), U32.18 (D4), U34.18 (D4), U36.18 (D4), U38.18 (D4), U40.18 (D4), U42.18 (D4), U44.18 (D4)
ED5: U22.13 (B5), U26.19 (D5), U31.13 (B5), U32.19 (D5), U34.19 (D5), U36.19 (D5), U38.19 (D5), U40.19 (D5), U42.19 (D5), U44.19 (D5)
ED6: U22.12 (B6), U26.20 (D6), U31.12 (B6), U32.20 (D6), U34.20 (D6), U36.20 (D6), U38.20 (D6), U40.20 (D6), U42.20 (D6), U44.20 (D6)
ED7: U22.11 (B7), U26.21 (D7), U31.11 (B7), U32.21 (D7), U34.21 (D7), U36.21 (D7), U38.21 (D7), U40.21 (D7), U42.21 (D7), U44.21 (D7)
ERROR*: P1.98 (ERROR*)
F*: U15.10, U21.29 (WE), U29.29 (WE), U33.29 (WE), U35.29 (WE), U37.29 (WE), U39.29 (WE), U41.29 (WE), U43.29 (WE)
G*: U.13, U26.29 (WE), U32.29 (WE), U34.29 (WE), U36.29 (WE), U38.29 (WE), U40.29 (WE), U42.29 (WE), U44.29 (WE)
GND: 0.1.2, C1.2, C2.2, C3.2, C4.2, C5.2, C6.2, C7.2, C8.2, C9.2, C10.2, C11.2, C12.2, C13.2, C14.2, C15.2, C16.2, C18.2, C19.2, C20.2, C21.2, C22.2, C23.2, C24.2, C25.2, C26.2, C27.2, C28.2, C29.2, C30.2, C36.2, C37.2, C39.2, C40.2, C41.2, C42.2, C43.2, JP1.1, JP2.1, JP3.1, P1.50 (0_V2), P1.100 (0_V5), P34.1, P35.1, SW1.1, SW1.2, SW1.3, SW1.4, SW1.5, SW1.6, SW1.7, SW1.8, SW2.1, SW2.2, SW2.3, SW2.4, SW2.5, SW2.6, SW2.7, SW2.8, SW3.1, SW3.2, SW3.3, SW3.4, SW3.5, SW3.6, SW3.7, SW3.8, SW4.1, SW4.2, SW4.3, SW4.4, SW4.5, SW4.6, SW4.7, SW4.8, U.1, U.19 (OEb), U1.2 (GND), U2.1 (OEa), U2.19 (OEb), U5.1 (B3), U5.15 (A3), U7.2 (Ia<b), U7.4 (Ia>b), U8.1 (B3), U8.15 (A3), U16.2 (Ia<b), U16.4 (Ia>b), U21.16 (GND), U23.1 (OEa), U23.19 (OEb), U24.1 (OEa), U24.19 (OEb), U26.16 (GND), U27.15 (CE), U29.16 (GND), U30.10, U31.1 (A->B), U32.16 (GND), U33.16 (GND), U34.16 (GND), U35.16 (GND), U36.16 (GND), U37.16 (GND), U38.16 (GND), U39.16 (GND), U40.16 (GND), U41.16 (GND), U42.16 (GND), U43.16 (GND), U44.16 (GND)
HOLD*: P1.74 (HOLD*)
INT*: P1.73 (INT*)
IO_REQUEST: U25.6, U25.9
MWRT: P1.68 (MWRT)
NDEF1: P1.21 (NDEF1)
NDEF2: P1.65 (NDEF2), U25.12
NDEF3: P1.66 (NDEF3)
NMI*: P1.12 (NMI*)
unnamed: D1.2 (K), R1.2
unnamed: D2.2 (K), R2.1
unnamed: D3.2 (K), R3.1
unnamed: D4.2 (K), R4.1
unnamed: D5.2 (K), R5.1
unnamed: D6.2 (K), R6.2
unnamed: D7.2 (K), R7.2
unnamed: D8.2 (K), R8.2
unnamed: D9.2 (K), R9.2
unnamed: D10.2 (K), R10.2
unnamed: D11.2 (K), R11.2
unnamed: D12.2 (K), R12.2
unnamed: JP8.1, U10.1
unnamed: R1.1, U3.15 (O0)
unnamed: R2.2, U.12
unnamed: R3.2, U.9
unnamed: R4.2, U.7 (GND)
unnamed: R5.2, U.5
unnamed: R6.1, U3.14 (O1)
unnamed: R7.1, U3.13 (O2)
unnamed: R8.1, U3.12 (O3)
unnamed: R9.1, U3.11 (O4)
unnamed: R10.1, U3.10 (O5)
unnamed: R11.1, U3.9 (O6)
unnamed: R12.1, U3.7 (O7)
unnamed: RR1.2, SW2.9, U27.6 (P7)
unnamed: RR1.3, SW2.10, U27.5 (P6)
unnamed: RR1.4, SW2.11, U27.4 (P5)
unnamed: RR1.5, SW2.12, U27.3 (P4)
unnamed: RR1.6, SW2.13, U27.14 (P3)
unnamed: RR1.7, SW2.14, U27.13 (P2)
unnamed: RR1.8, SW2.15, U27.12 (P1)
unnamed: RR1.9, SW2.16, U27.11 (P0)
unnamed: RR2.4, SW3.9, U5.13 (A2)
unnamed: RR2.5, SW3.10, U5.12 (A1)
unnamed: RR2.6, SW3.11, U5.10 (A0)
unnamed: RR2.8, SW3.14, U8.13 (A2)
unnamed: RR2.9, SW3.15, U8.12 (A1)
unnamed: RR2.10, SW3.16, U8.10 (A0)
unnamed: RR3.3, SW1.9, U6.15 (A3)
unnamed: RR3.4, SW1.10, U6.13 (A2)
unnamed: RR3.5, SW1.11, U6.12 (A1)
unnamed: RR3.6, SW1.12, U6.10 (A0)
unnamed: RR3.7, SW1.13, U7.15 (A3)
unnamed: RR3.8, SW1.14, U7.13 (A2)
unnamed: RR3.9, SW1.15, U7.12 (A1)
unnamed: RR3.10, SW1.16, U7.10 (A0)
unnamed: RR4.3, SW4.9, U11.15 (A3)
unnamed: RR4.4, SW4.10, U11.13 (A2)
unnamed: RR4.5, SW4.11, U11.12 (A1)
unnamed: RR4.6, SW4.12, U11.10 (A0)
unnamed: RR4.7, SW4.13, U16.15 (A3)
unnamed: RR4.8, SW4.14, U16.13 (A2)
unnamed: RR4.9, SW4.15, U16.12 (A1)
unnamed: RR4.10, SW4.16, U16.10 (A0)
unnamed: U5.2 (Ia<b), U6.7 (Oa<b)
unnamed: U5.3 (Ia=b), U6.6 (Oa=b)
unnamed: U5.4 (Ia>b), U6.5 (Oa>b)
unnamed: U6.2 (Ia<b), U7.7 (Oa<b)
unnamed: U6.3 (Ia=b), U7.6 (Oa=b)
unnamed: U6.4 (Ia>b), U7.5 (Oa>b)
unnamed: U11.2 (Ia<b), U16.7 (Oa<b)
unnamed: U11.3 (Ia=b), U16.6 (Oa=b)
unnamed: U11.4 (Ia>b), U16.5 (Oa>b)
unnamed: U8.4 (Ia>b), U11.5 (Oa>b)
unnamed: U8.3 (Ia=b), U11.6 (Oa=b)
unnamed: U8.2 (Ia<b), U11.7 (Oa<b)
unnamed: U5.5 (Oa>b), U18.1
unnamed: U5.6 (Oa=b), U18.2
unnamed: U18.3, U20.1
unnamed: U8.7 (Oa<b), U18.4
unnamed: U8.6 (Oa=b), U18.5
unnamed: U18.6, U20.2
unnamed: U5.7 (Oa<b), U18.9
unnamed: U8.5 (Oa>b), U18.10
unnamed: U18.11, U25.10
unnamed: U18.12, U20.3
unnamed: U18.8, U18.13
unnamed: U25.3, U25.4
unnamed: U25.8, U25.13
unnamed: U.2, U.3
unnamed: U.3, U30.9
unnamed: U.5, U.6, U.8, U27.7 (~Q7)
unnamed: U.6, U15.8, U30.11
unnamed: U.9, U12.9, U13.1
unnamed: U.11, U14.11
unnamed: U.12, U12.2, U12.10
unnamed: U.8, U.14 (VCC), U10.2, U12.4, U13.2
unnamed: U.16 (O1a), U12.1, U12.3
unnamed: U.4, U.18 (O0a)
OD0: U19.18 (B0), U21.13 (D0), U29.13 (D0), U31.2 (A0), U33.13 (D0), U35.13 (D0), U37.13 (D0), U39.13 (D0), U41.13 (D0), U43.13 (D0)
OD1: U19.17 (B1), U21.14 (D1), U29.14 (D1), U31.3 (A1), U33.14 (D1), U35.14 (D1), U37.14 (D1), U39.14 (D1), U41.14 (D1), U43.14 (D1)
OD2: U19.16 (B2), U21.15 (D2), U29.15 (D2), U31.4 (A2), U33.15 (D2), U35.15 (D2), U37.15 (D2), U39.15 (D2), U41.15 (D2), U43.15 (D2)
OD3: U19.15 (B3), U21.17 (D3), U29.17 (D3), U31.5 (A3), U33.17 (D3), U35.17 (D3), U37.17 (D3), U39.17 (D3), U41.17 (D3), U43.17 (D3)
OD4: U19.14 (B4), U21.18 (D4), U29.18 (D4), U31.6 (A4), U33.18 (D4), U35.18 (D4), U37.18 (D4), U39.18 (D4), U41.18 (D4), U43.18 (D4)
OD5: U19.13 (B5), U21.19 (D5), U29.19 (D5), U31.7 (A5), U33.19 (D5), U35.19 (D5), U37.19 (D5), U39.19 (D5), U41.19 (D5), U43.19 (D5)
OD6: U19.12 (B6), U21.20 (D6), U29.20 (D6), U31.8 (A6), U33.20 (D6), U35.20 (D6), U37.20 (D6), U39.20 (D6), U41.20 (D6), U43.20 (D6)
OD7: U19.11 (B7), U21.21 (D7), U29.21 (D7), U31.9 (A7), U33.21 (D7), U35.21 (D7), U37.21 (D7), U39.21 (D7), U41.21 (D7), U43.21 (D7)
PHANTOM*: P1.67 (PHANTOM*), U.11, U.12
PHI: P1.24 (PHI), U.2
PHI*: U.18 (O0a), U27.2 (CP)
POC*: P1.99 (POC*)
PWRFAIL*: P1.13 (PWRFAIL*)
RDY: P1.72 (RDY), U.4
RESET*: P1.75 (RESET*)
RFU1: P1.27 (RFU_1)
RFU2: P1.28 (RFU_2)
RFU3: P1.69 (RFU3)
RFU4: P1.71 (RFU4)
SDSB*: P1.18 (SDSB*)
SIXTN*: JP8.2, P1.60 (SIXTN*)
SLAVE_CLR*: P1.54 (SLAVE_CLR*)
TMA0*: P1.55 (TMA0*)
TMA1*: P1.56 (TMA1*)
TMA2*: P1.57 (TMA2*)
TMA3*: P1.14 (TMA3*)
VCC: 0.1.1, C2.1, C3.1, C4.1, C5.1, C6.1, C7.1, C8.1, C9.1, C10.1, C11.1, C12.1, C13.1, C14.1, C15.1, C16.1, C18.1, C19.1, C20.1, C21.1, C22.1, C23.1, C24.1, C25.1, C26.1, C27.1, C28.1, C29.1, C30.1, C36.1, C37.1, C39.1, C40.1, C41.1, C42.1, C43.1, D1.1 (A), D2.1 (A), D3.1 (A), D4.1 (A), D5.1 (A), D6.1 (A), D7.1 (A), D8.1 (A), D9.1 (A), D10.1 (A), D11.1 (A), D12.1 (A), RR1.1 (COM), RR2.1 (COM), RR3.1 (COM), RR4.1 (COM), U1.3 (VO), U3.6 (E3), U4.6 (E3), U7.3 (Ia=b), U16.3 (Ia=b), U21.32 (VCC), U26.32 (VCC), U27.10 (Ds), U29.32 (VCC), U32.32 (VCC), U33.32 (VCC), U34.32 (VCC), U35.32 (VCC), U36.32 (VCC), U37.32 (VCC), U38.32 (VCC), U39.32 (VCC), U40.32 (VCC), U41.32 (VCC), U42.32 (VCC), U43.32 (VCC), U44.32 (VCC)
VI0*: P1.4 (VIO*)
VI1*: P1.5 (VI1*)
VI2*: P1.6 (VI2*)
VI3*: P1.7 (VI3*)
VI4*: P1.8 (VI4*)
VI5*: P1.9 (VI5*)
VI6*: P1.10 (VI6*)
VI7*: P1.11 (VI7*)
XRDY: P1.3 (XRDY)
bA1: U21.12 (A0), U23.18 (O0a), U26.12 (A0), U29.12 (A0), U32.12 (A0), U33.12 (A0), U34.12 (A0), U35.12 (A0), U36.12 (A0), U37.12 (A0), U38.12 (A0), U39.12 (A0), U40.12 (A0), U41.12 (A0), U42.12 (A0), U43.12 (A0), U44.12 (A0)
bA2: U21.11 (A1), U23.16 (O1a), U26.11 (A1), U29.11 (A1), U32.11 (A1), U33.11 (A1), U34.11 (A1), U35.11 (A1), U36.11 (A1), U37.11 (A1), U38.11 (A1), U39.11 (A1), U40.11 (A1), U41.11 (A1), U42.11 (A1), U43.11 (A1), U44.11 (A1)
bA3: U21.10 (A2), U23.14 (O2a), U26.10 (A2), U29.10 (A2), U32.10 (A2), U33.10 (A2), U34.10 (A2), U35.10 (A2), U36.10 (A2), U37.10 (A2), U38.10 (A2), U39.10 (A2), U40.10 (A2), U41.10 (A2), U42.10 (A2), U43.10 (A2), U44.10 (A2)
bA4: U21.9 (A3), U23.12 (O3a), U26.9 (A3), U29.9 (A3), U32.9 (A3), U33.9 (A3), U34.9 (A3), U35.9 (A3), U36.9 (A3), U37.9 (A3), U38.9 (A3), U39.9 (A3), U40.9 (A3), U41.9 (A3), U42.9 (A3), U43.9 (A3), U44.9 (A3)
bA5: U21.8 (A4), U23.9 (O0b), U26.8 (A4), U29.8 (A4), U32.8 (A4), U33.8 (A4), U34.8 (A4), U35.8 (A4), U36.8 (A4), U37.8 (A4), U38.8 (A4), U39.8 (A4), U40.8 (A4), U41.8 (A4), U42.8 (A4), U43.8 (A4), U44.8 (A4)
bA6: U21.7 (A5), U23.7 (O1b), U26.7 (A5), U29.7 (A5), U32.7 (A5), U33.7 (A5), U34.7 (A5), U35.7 (A5), U36.7 (A5), U37.7 (A5), U38.7 (A5), U39.7 (A5), U40.7 (A5), U41.7 (A5), U42.7 (A5), U43.7 (A5), U44.7 (A5)
bA7: U21.6 (A6), U23.5 (O2b), U26.6 (A6), U29.6 (A6), U32.6 (A6), U33.6 (A6), U34.6 (A6), U35.6 (A6), U36.6 (A6), U37.6 (A6), U38.6 (A6), U39.6 (A6), U40.6 (A6), U41.6 (A6), U42.6 (A6), U43.6 (A6), U44.6 (A6)
bA8: U21.5 (A7), U23.3 (O3b), U26.5 (A7), U29.5 (A7), U32.5 (A7), U33.5 (A7), U34.5 (A7), U35.5 (A7), U36.5 (A7), U37.5 (A7), U38.5 (A7), U39.5 (A7), U40.5 (A7), U41.5 (A7), U42.5 (A7), U43.5 (A7), U44.5 (A7)
bA9: U21.27 (A8), U24.18 (O0a), U26.27 (A8), U29.27 (A8), U32.27 (A8), U33.27 (A8), U34.27 (A8), U35.27 (A8), U36.27 (A8), U37.27 (A8), U38.27 (A8), U39.27 (A8), U40.27 (A8), U41.27 (A8), U42.27 (A8), U43.27 (A8), U44.27 (A8)
bA10: U21.26 (A9), U24.16 (O1a), U26.26 (A9), U29.26 (A9), U32.26 (A9), U33.26 (A9), U34.26 (A9), U35.26 (A9), U36.26 (A9), U37.26 (A9), U38.26 (A9), U39.26 (A9), U40.26 (A9), U41.26 (A9), U42.26 (A9), U43.26 (A9), U44.26 (A9)
bA11: U21.23 (A10), U24.14 (O2a), U26.23 (A10), U29.23 (A10), U32.23 (A10), U33.23 (A10), U34.23 (A10), U35.23 (A10), U36.23 (A10), U37.23 (A10), U38.23 (A10), U39.23 (A10), U40.23 (A10), U41.23 (A10), U42.23 (A10), U43.23 (A10), U44.23 (A10)
bA12: U21.25 (A11), U24.12 (O3a), U26.25 (A11), U29.25 (A11), U32.25 (A11), U33.25 (A11), U34.25 (A11), U35.25 (A11), U36.25 (A11), U37.25 (A11), U38.25 (A11), U39.25 (A11), U40.25 (A11), U41.25 (A11), U42.25 (A11), U43.25 (A11), U44.25 (A11)
bA13: U7.9 (B0), U16.9 (B0), U21.4 (A12), U24.9 (O0b), U26.4 (A12), U29.4 (A12), U32.4 (A12), U33.4 (A12), U34.4 (A12), U35.4 (A12), U36.4 (A12), U37.4 (A12), U38.4 (A12), U39.4 (A12), U40.4 (A12), U41.4 (A12), U42.4 (A12), U43.4 (A12), U44.4 (A12)
bA14: U7.11 (B1), U16.11 (B1), U21.28 (A13), U24.7 (O1b), U26.28 (A13), U29.28 (A13), U32.28 (A13), U33.28 (A13), U34.28 (A13), U35.28 (A13), U36.28 (A13), U37.28 (A13), U38.28 (A13), U39.28 (A13), U40.28 (A13), U41.28 (A13), U42.28 (A13), U43.28 (A13), U44.28 (A13)
bA15: U7.14 (B2), U16.14 (B2), U21.3 (A14), U24.5 (O2b), U26.3 (A14), U29.3 (A14), U32.3 (A14), U33.3 (A14), U34.3 (A14), U35.3 (A14), U36.3 (A14), U37.3 (A14), U38.3 (A14), U39.3 (A14), U40.3 (A14), U41.3 (A14), U42.3 (A14), U43.3 (A14), U44.3 (A14)
bA16: U2.3 (O3b), U7.1 (B3), U16.1 (B3), U21.31 (A15), U26.31 (A15), U29.31 (A15), U32.31 (A15), U33.31 (A15), U34.31 (A15), U35.31 (A15), U36.31 (A15), U37.31 (A15), U38.31 (A15), U39.31 (A15), U40.31 (A15), U41.31 (A15), U42.31 (A15), U43.31 (A15), U44.31 (A15)
bA17: U2.5 (O2b), U6.9 (B0), U11.9 (B0), U21.2 (A16), U26.2 (A16), U29.2 (A16), U32.2 (A16), U33.2 (A16), U34.2 (A16), U35.2 (A16), U36.2 (A16), U37.2 (A16), U38.2 (A16), U39.2 (A16), U40.2 (A16), U41.2 (A16), U42.2 (A16), U43.2 (A16), U44.2 (A16)
bA18: U2.7 (O1b), U6.11 (B1), U11.11 (B1), U21.30 (A17), U26.30 (A17), U29.30 (A17), U32.30 (A17), U33.30 (A17), U34.30 (A17), U35.30 (A17), U36.30 (A17), U37.30 (A17), U38.30 (A17), U39.30 (A17), U40.30 (A17), U41.30 (A17), U42.30 (A17), U43.30 (A17), U44.30 (A17)
bA19: U2.9 (O0b), U6.14 (B2), U11.14 (B2), U21.1 (A18), U26.1 (A18), U29.1 (A18), U32.1 (A18), U33.1 (A18), U34.1 (A18), U35.1 (A18), U36.1 (A18), U37.1 (A18), U38.1 (A18), U39.1 (A18), U40.1 (A18), U41.1 (A18), U42.1 (A18), U43.1 (A18), U44.1 (A18)
bA20: U2.12 (O3a), U3.1 (A0), U4.1 (A0), U6.1 (B3), U11.1 (B3)
bA21: U2.14 (O2a), U3.2 (A1), U4.2 (A1), U5.9 (B0), U8.9 (B0)
bA22: U2.16 (O1a), U3.3 (A2), U4.3 (A2), U5.11 (B1), U8.11 (B1)
bA23: U2.18 (O0a), U5.14 (B2), U8.14 (B2)
buffered_A0: U.2, U.4, U.5
pDBIN: P1.78 (pDBIN), U.2
pHLDA: P1.26 (pHDLA)
pSTVAL*: P1.25 (pSTVAL*)
pSYNC: P1.76 (pSYNC), U.12
pWR*: P1.77 (pWR*), U.11
sHLTA: P1.48 (sHLTA)
sINP: P1.46 (sINP), U25.2
sINTA: P1.96 (sINTA), U25.5
sM1: P1.44 (sM1)
sMEMR: P1.47 (sMEMR), U.17 (I3b)
sMEMR*: U.3, U19.1 (A->B), U22.1 (A->B)
sOUT: P1.45 (sOUT), U25.1
sWO*: P1.97 (sWO*)
sXTRQ*: P1.58 (sXTRQ*), U.6
~BOARD_SYNC: U.3
~RAMCS0: U4.15 (O0), U21.22 (CE), U26.22 (CE)
~RAMCS1: U4.14 (O1), U29.22 (CE), U32.22 (CE)
~RAMCS2: U4.13 (O2), U33.22 (CE), U34.22 (CE)
~RAMCS3: U4.12 (O3), U35.22 (CE), U36.22 (CE)
~RAMCS4: U4.11 (O4), U37.22 (CE), U38.22 (CE)
~RAMCS5: U4.10 (O5), U39.22 (CE), U40.22 (CE)
~RAMCS6: U4.9 (O6), U41.22 (CE), U42.22 (CE)
~RAMCS7: U4.7 (O7), U43.22 (CE), U44.22 (CE)

Notes on the sheet:
74LS240 INVERTER I3b/O3b
8rd 16rd 8wr 16wr
ODD BYTE RAM
EVEN BYTE RAM
SPARES
Card Ejector Mounting Holes
inverting buffer
xx A23 A22 A21
A20 A19 A18 A17 A16 A15 A14 A13
A23 A22 A21
BOARD LOW START ADDRESS
BOARD HIGH END ADDRESS
B is Address Lines A is DIP Switches
A>B -> within A<B -> not within board domain (higher than) A=B -> within
A>B -> not within board domain (lower than) A<B -> within A=B -> within
HIGH when IO request
LOW when Address inputs meet board domain requirement
HIGH when out of range
TO-220
pin 65 S100 bus Memory Request (active low) ~MEMRQ
A* active low MEM READ
Data INPUT from S100 Bus
Data OUTPUT to S100 Bus
C* active low MEM WRITE
G* active low EVEN bank WE
E* active low EVEN bank OE
F* active low ODD bank WE
D* active low ODD bank OE
B->A
B* active low ODD address MEM WRITE EVEN address MEM READ
B* active low data BRIDGE
