CatspersCoffee/S100-Boards/SRAM-8MB/rev2/s100_SRAMp2.sch

## KiCad design SRAM-8MB/rev2/s100_SRAMp2.sch (2015-07-16, an earlier design)

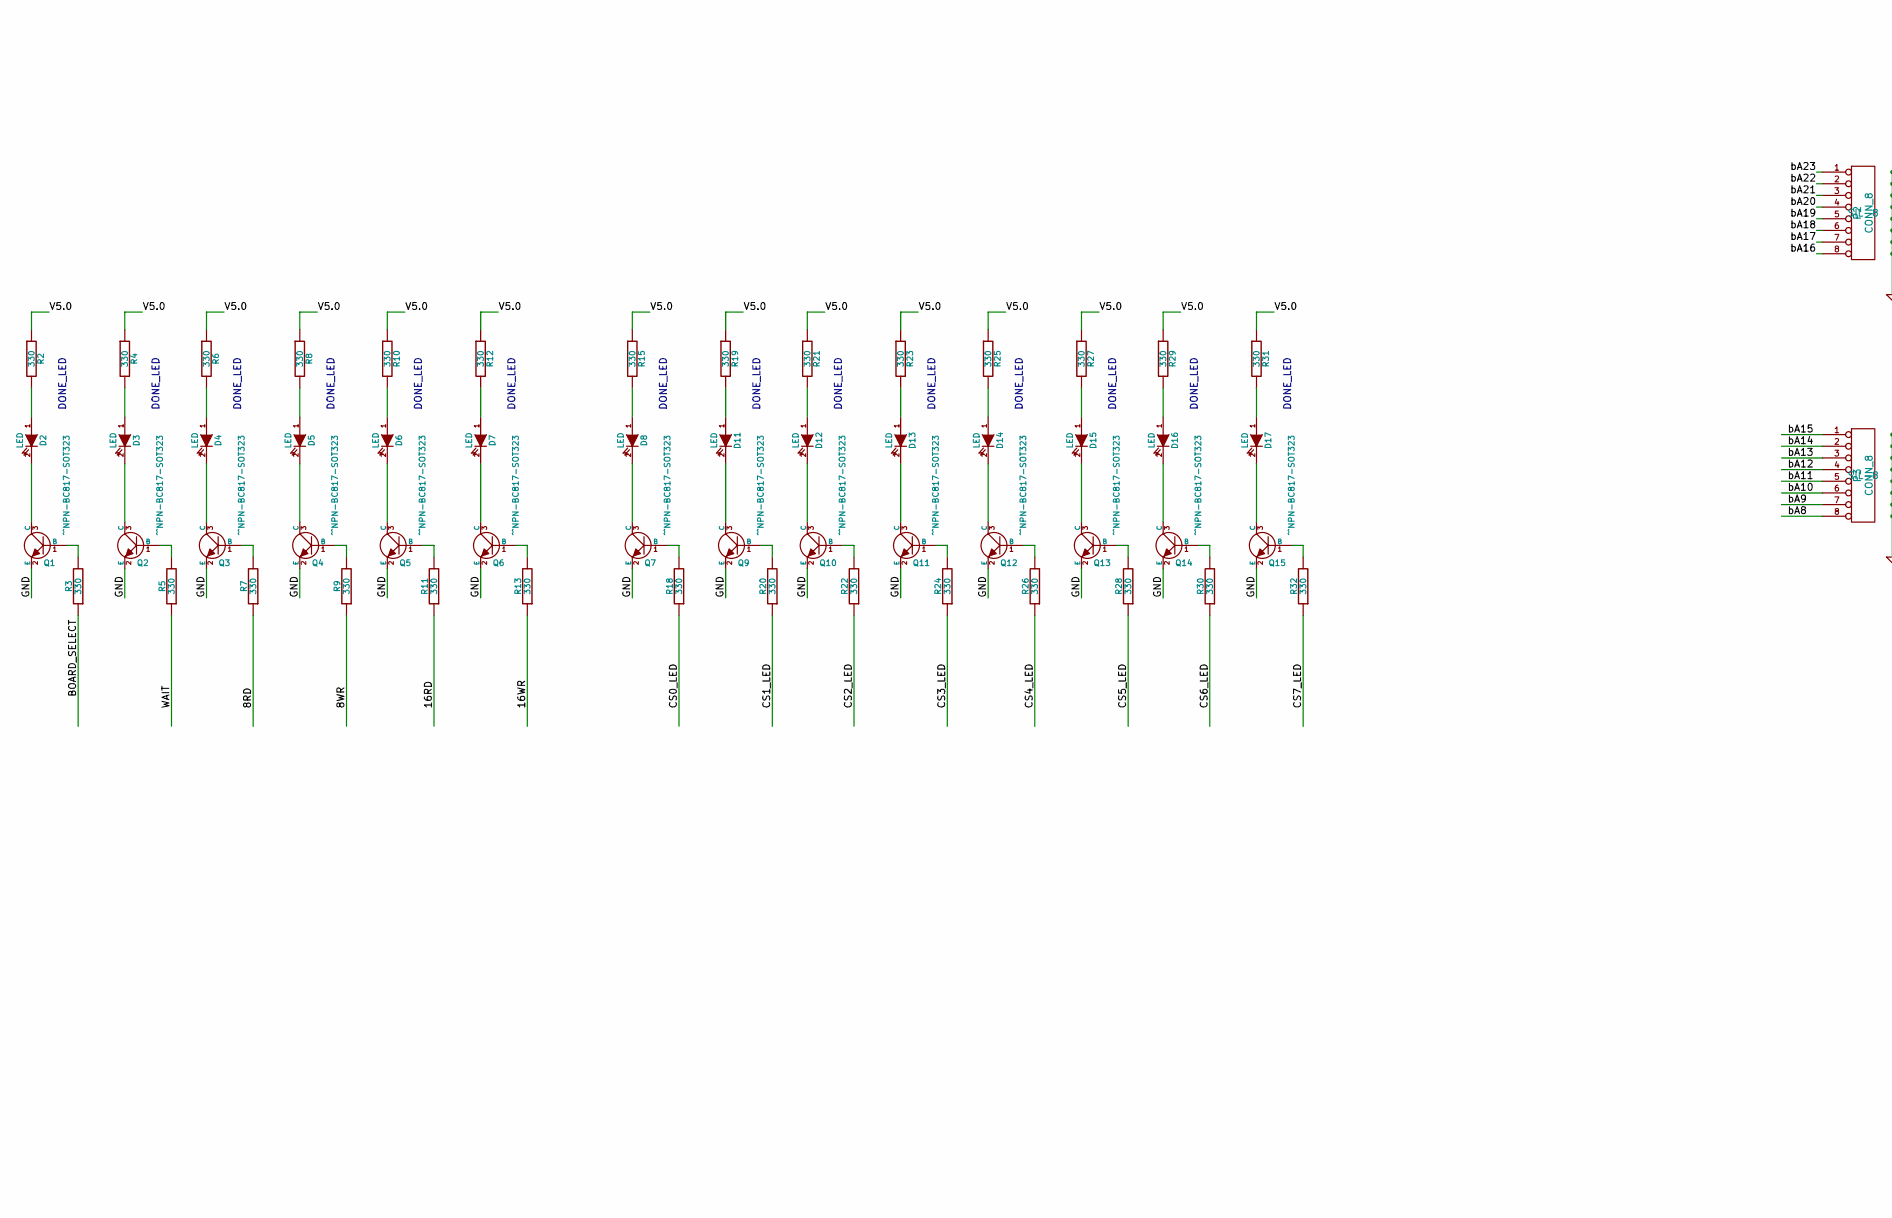
[picture p66: schematic s100_SRAMp2.sch, part in row 1, column 1]

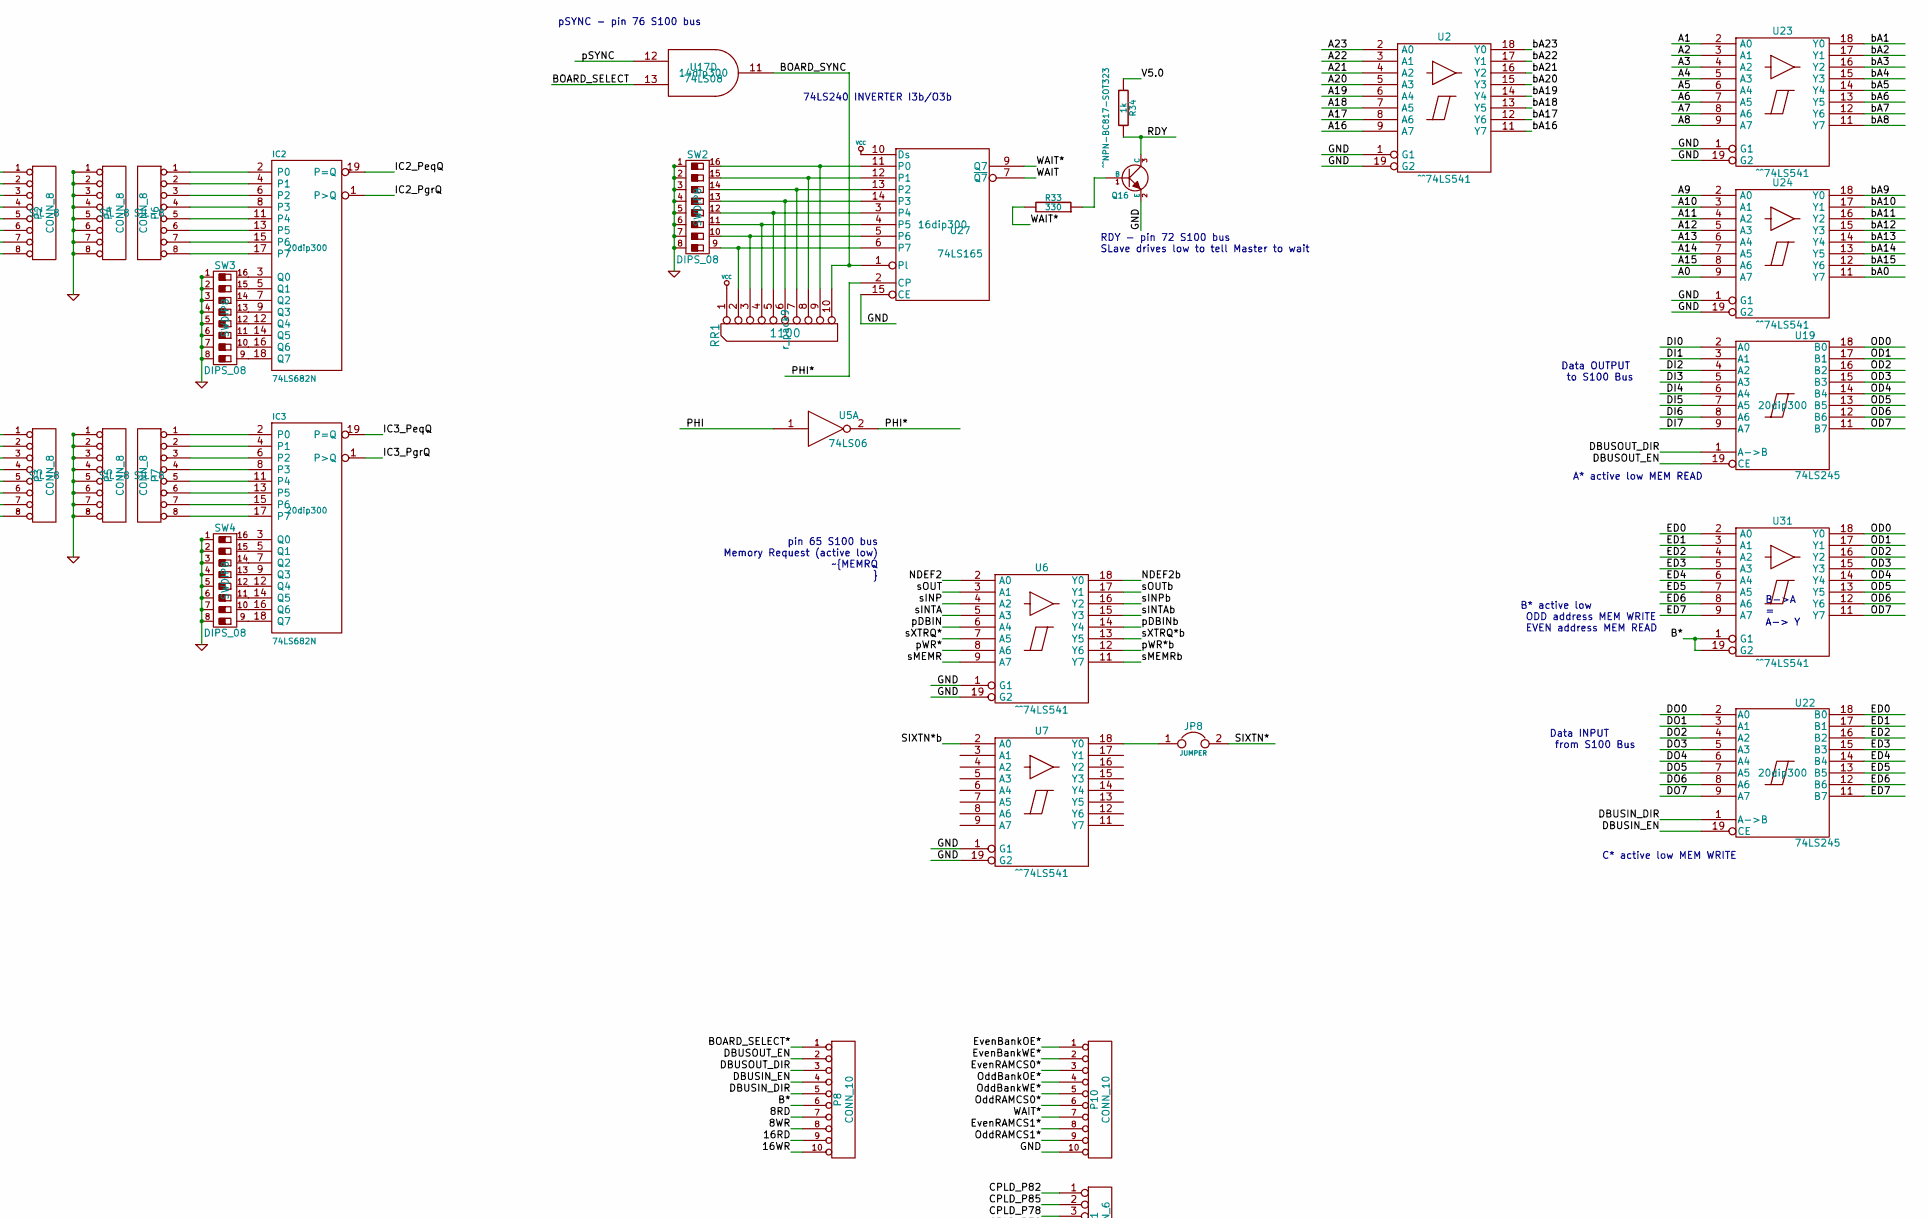
[picture p67: schematic s100_SRAMp2.sch, part in row 1, column 2]

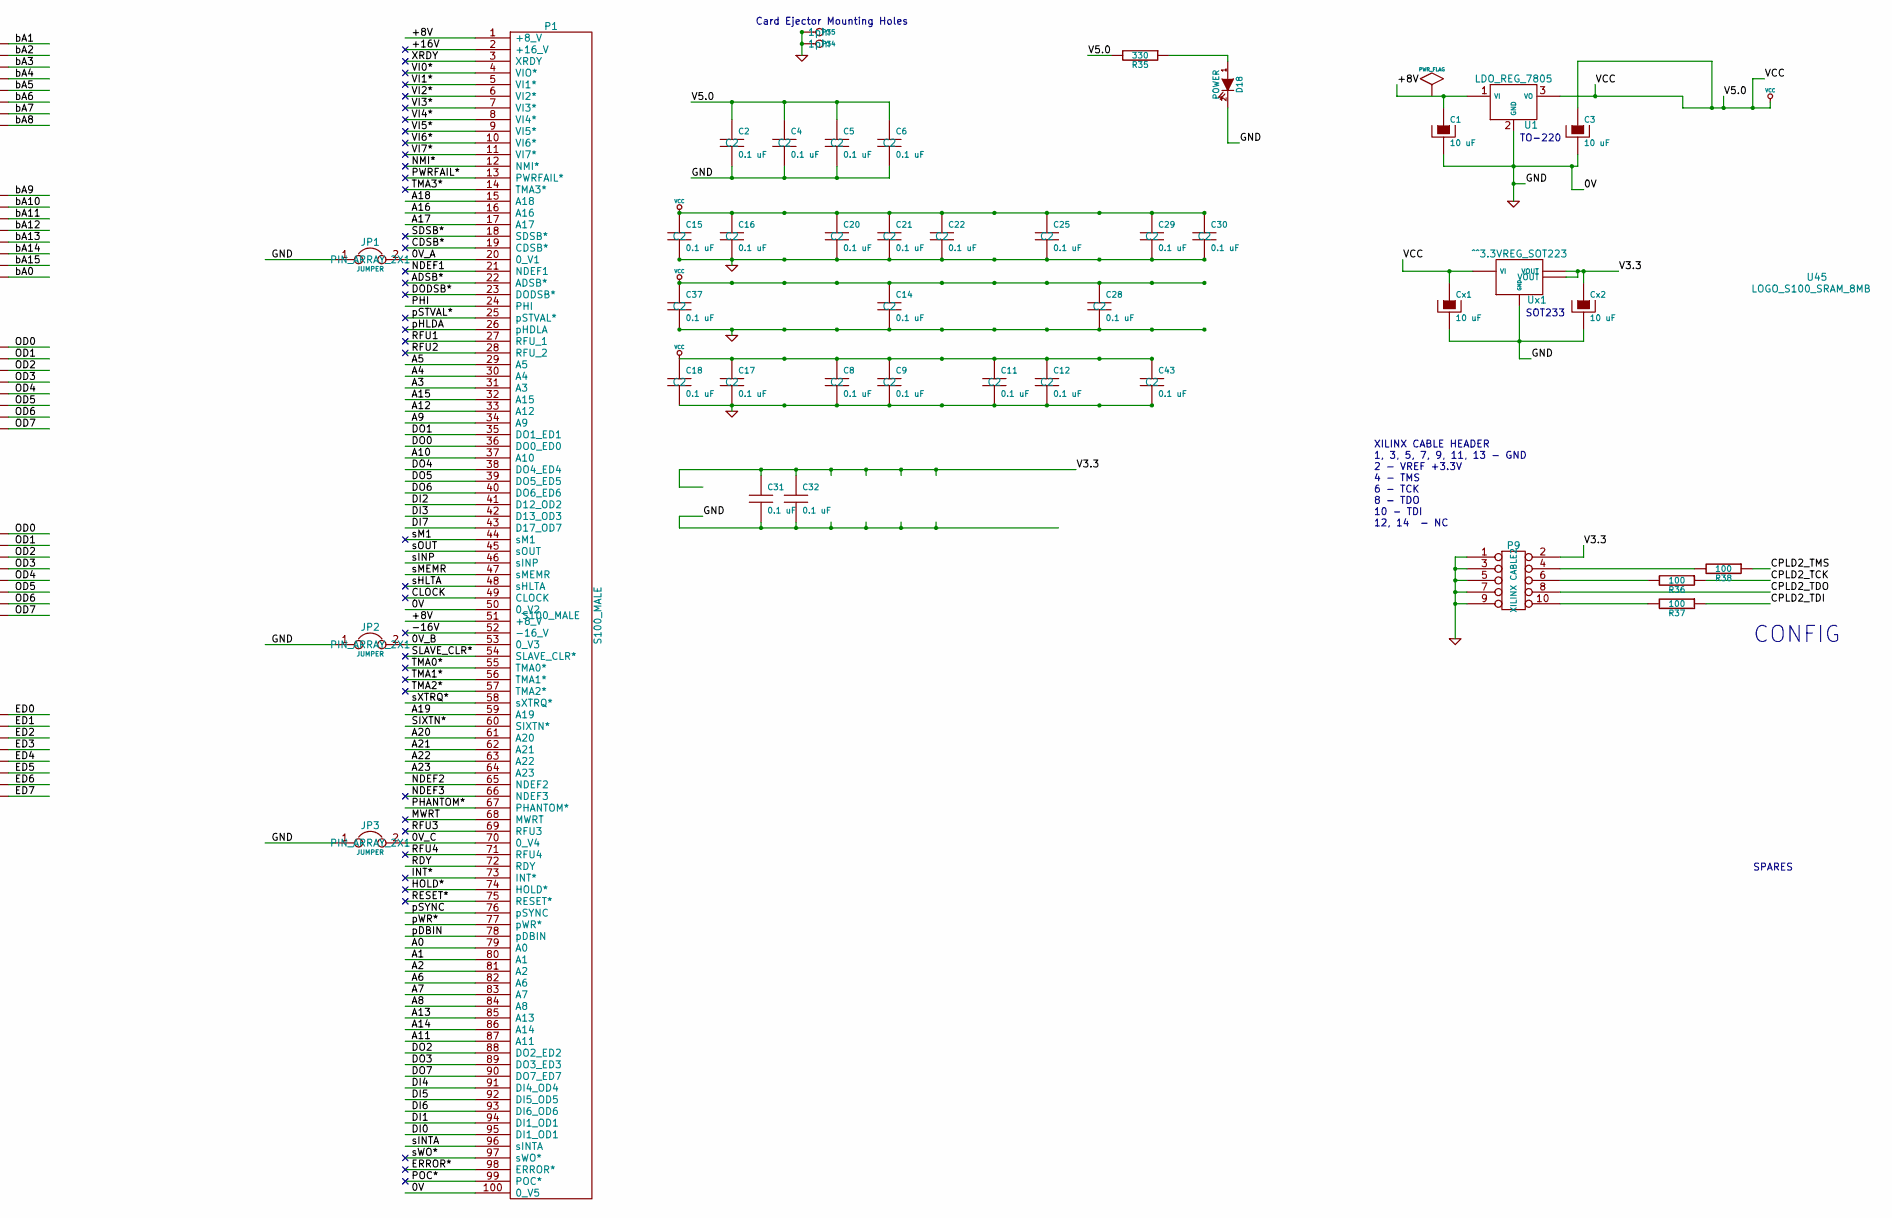
[picture p68: schematic s100_SRAMp2.sch, part in row 1, column 3]

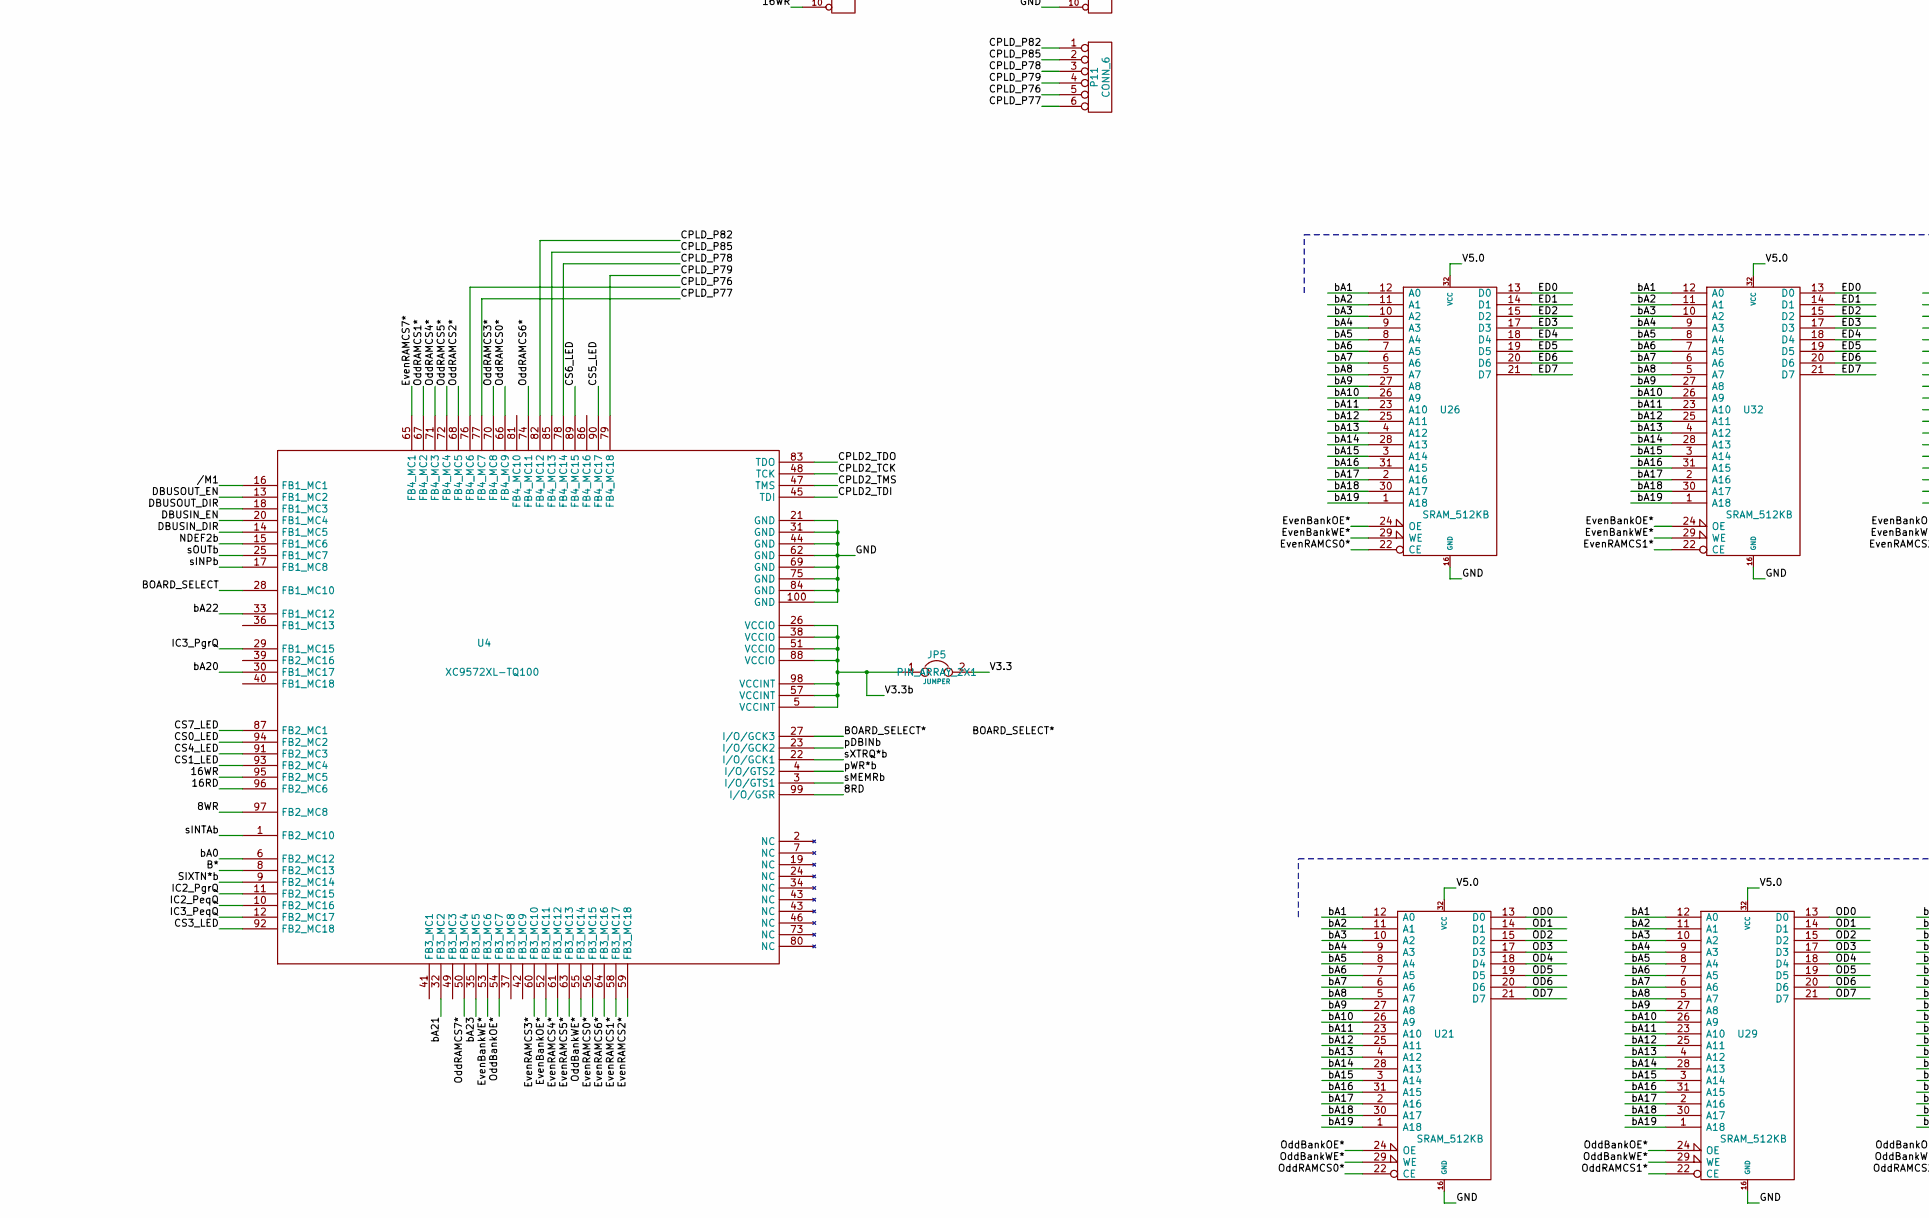
[picture p69: schematic s100_SRAMp2.sch, part in row 2, column 2]

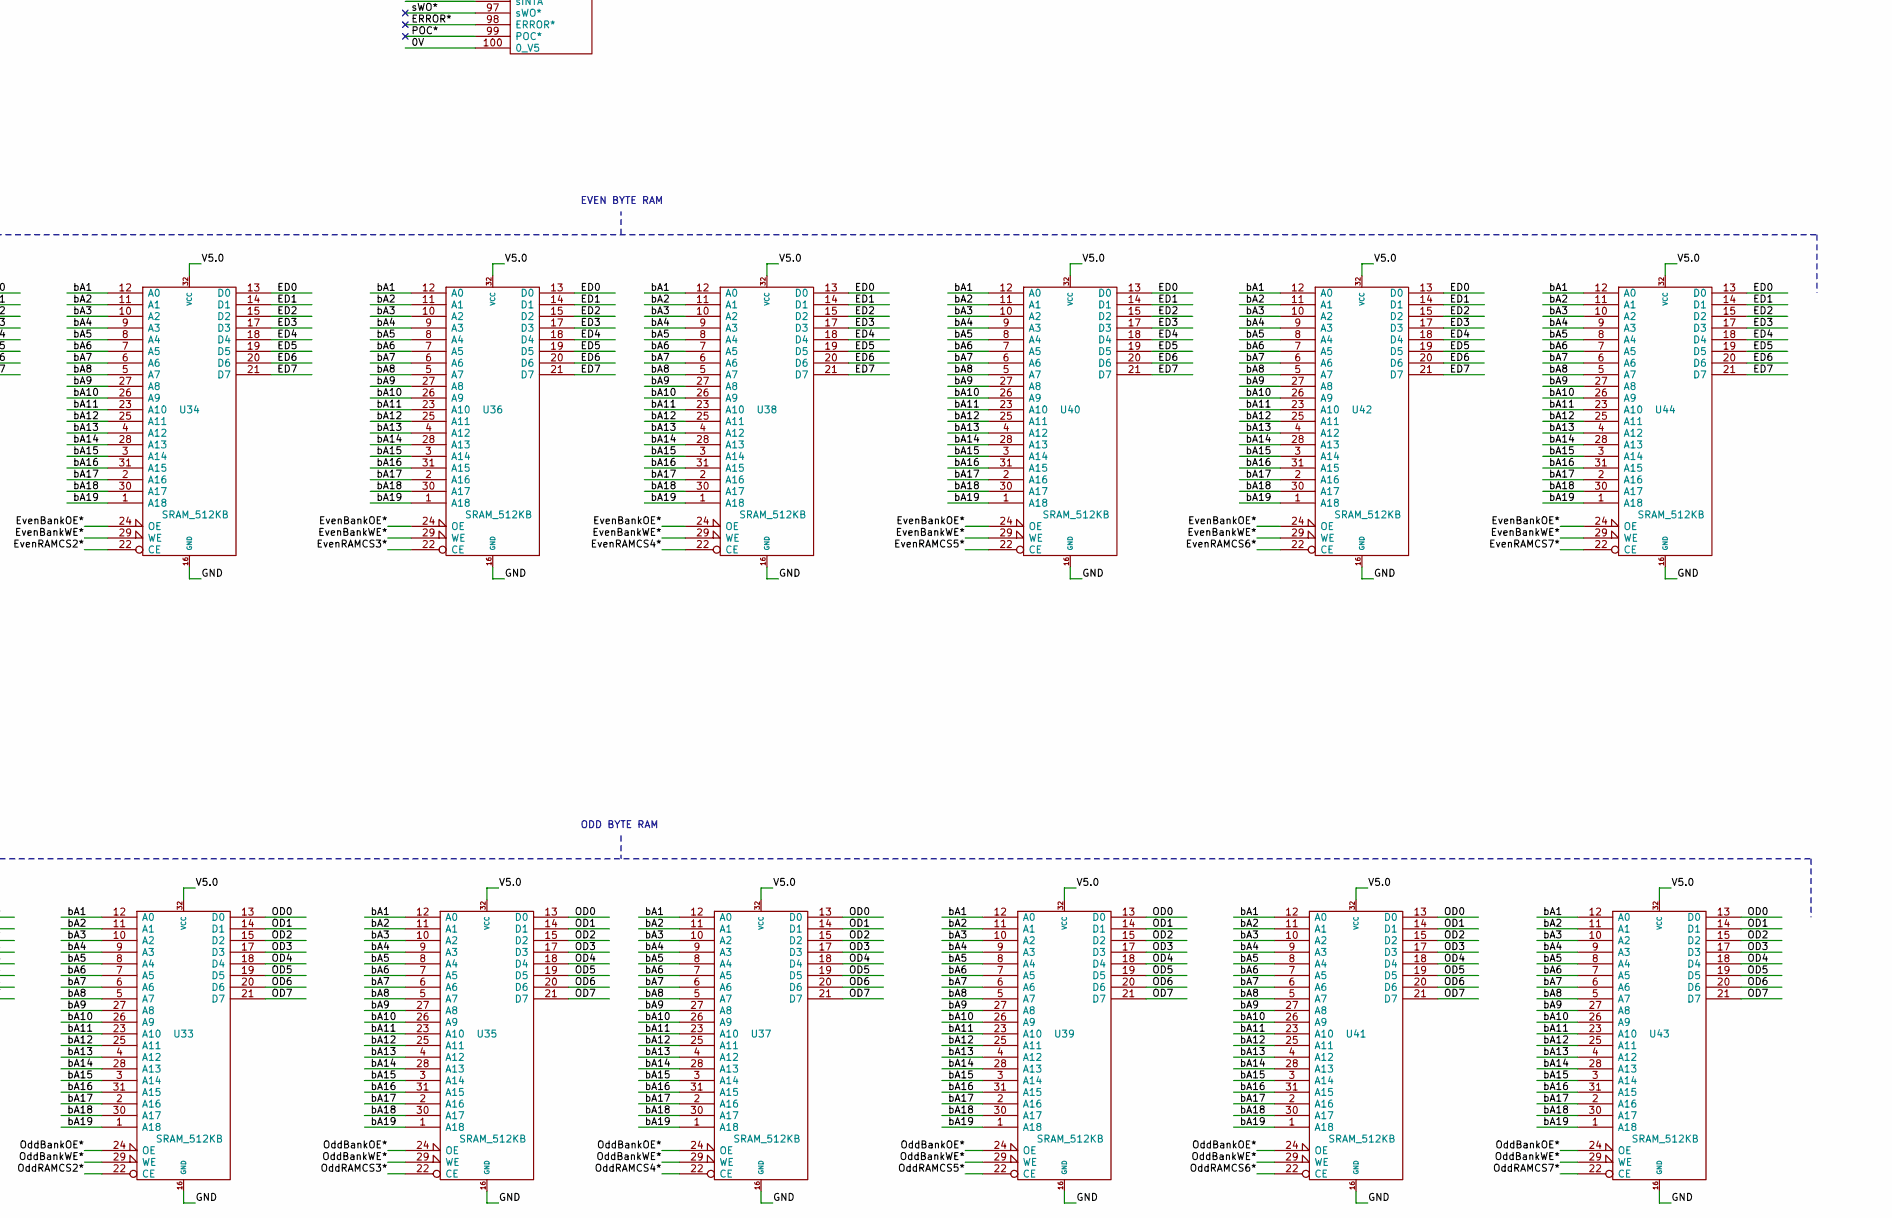
[picture p70: schematic s100_SRAMp2.sch, part in row 2, column 3]

Parts:
0.1: 0.1 uF; C2
C1, C3: 10 uF
C2, C4, C5, C6, C8, C9, C11, C12, C14, C15, C16, C18, C20, C21, C22, C25, C28, C29, C30, C37, C43: 0.1 uF; C2
C31, C32: 0.1 uF
Cx1, Cx2: 10 uF
D2, D3, D4, D5, D6, D7, D8, D11, D12, D13, D14, D15, D16, D17: LED
D18: POWER
IC2, IC3: 74LS682N; 20dip300
JP1, JP2, JP3, JP5: JUMPER; PIN_ARRAY_2X1
JP8: JUMPER
P1: S100_MALE
P2, P3, P4, P5, P6, P7: CONN_8; SIL-8
P8, P10: CONN_10
P9: XILINX CABLE2
P11: CONN_6
P34, P35: CONN_1; 1pin
Q1, Q2, Q3, Q4, Q5, Q6, Q7, Q9, Q10, Q11, Q12, Q13, Q14, Q15, Q16: ^^NPN-BC817-SOT323
R2, R3, R4, R5, R6, R7, R8, R9, R10, R11, R12, R13, R15, R18, R19, R20, R21, R22, R23, R24, R25, R26, R27, R28, R29, R30, R31, R32, R33, R35: 330
R34: 1k
R36, R37, R38: 100
RR1: 1100; r_pack9
SW2, SW3, SW4: DIPS_08; SWDIP8
U: 74LS08; 14dip300
U1: LDO_REG_7805
U2, U6, U7, U23, U24, U31: ^^74LS541
U4: XC9572XL-TQ100
U5: 74LS06
U19, U22: 74LS245; 20dip300
U21, U26, U29, U32, U33, U34, U35, U36, U37, U38, U39, U40, U41, U42, U43, U44: SRAM_512KB
U27: 74LS165; 16dip300
U45: LOGO_S100_SRAM_8MB
Ux1: ^^3.3VREG_SOT223

Connections:
0V_A: JP1.2, P1.20 (0_V1)
0V_B: JP2.2, P1.53 (0_V3)
0V_C: JP3.2, P1.70 (0_V4)
8RD: P8.7, R7.1, U4.99 (I/O/GSR)
8WR: P8.8, R9.1, U4.97 (FB2_MC8)
16RD: P8.9, R11.1, U4.96 (FB2_MC6)
16WR: P8.10, R13.1, U4.95 (FB2_MC5)
+8V: C1.1, P1.1 (+8_V), P1.51 (+8_V), U1.1 (VI)
+16V: P1.2 (+16_V)
-16V: P1.52 (-16_V)
/M1: U4.16 (FB1_MC1)
A0: P1.79 (A0), U24.9 (A7)
A1: P1.80 (A1), U23.2 (A0)
A2: P1.81 (A2), U23.3 (A1)
A3: P1.31 (A3), U23.4 (A2)
A4: P1.30 (A4), U23.5 (A3)
A5: P1.29 (A5), U23.6 (A4)
A6: P1.82 (A6), U23.7 (A5)
A7: P1.83 (A7), U23.8 (A6)
A8: P1.84 (A8), U23.9 (A7)
A9: P1.34 (A9), U24.2 (A0)
A10: P1.37 (A10), U24.3 (A1)
A11: P1.87 (A11), U24.4 (A2)
A12: P1.33 (A12), U24.5 (A3)
A13: P1.85 (A13), U24.6 (A4)
A14: P1.86 (A14), U24.7 (A5)
A15: P1.32 (A15), U24.8 (A6)
A16: P1.16 (A16), U2.9 (A7)
A17: P1.17 (A17), U2.8 (A6)
A18: P1.15 (A18), U2.7 (A5)
A19: P1.59 (A19), U2.6 (A4)
A20: P1.61 (A20), U2.5 (A3)
A21: P1.62 (A21), U2.4 (A2)
A22: P1.63 (A22), U2.3 (A1)
A23: P1.64 (A23), U2.2 (A0)
ADSB*: P1.22 (ADSB*)
B*: P8.6, U4.8 (FB2_MC13), U31.1 (G1), U31.19 (G2)
BOARD_SELECT: R3.1, U.13, U4.28 (FB1_MC10)
BOARD_SELECT*: P8.1, U4.27 (I/O/GCK3)
BOARD_SYNC: RR1.10, U.11, U27.1 (Pl)
CDSB*: P1.19 (CDSB*)
CLOCK: P1.49 (CLOCK)
CPLD2_TCK: R36.1, U4.48 (TCK)
CPLD2_TDI: R37.1, U4.45 (TDI)
CPLD2_TDO: P9.8, U4.83 (TDO)
CPLD2_TMS: R38.1, U4.47 (TMS)
CPLD_P76: P11.5, U4.76 (FB4_MC6)
CPLD_P77: P11.6, U4.77 (FB4_MC7)
CPLD_P78: P11.3, U4.78 (FB4_MC14)
CPLD_P79: P11.4, U4.79 (FB4_MC18)
CPLD_P82: P11.1, U4.82 (FB4_MC12)
CPLD_P85: P11.2, U4.85 (FB4_MC13)
CS0_LED: R18.1, U4.94 (FB2_MC2)
CS1_LED: R20.1, U4.93 (FB2_MC4)
CS2_LED: R22.1
CS3_LED: R24.1, U4.92 (FB2_MC18)
CS4_LED: R26.1, U4.91 (FB2_MC3)
CS5_LED: R28.1, U4.90 (FB4_MC17)
CS6_LED: R30.1, U4.89 (FB4_MC15)
CS7_LED: R32.1, U4.87 (FB2_MC1)
DBUSIN_DIR: P8.5, U4.14 (FB1_MC5), U22.1 (A->B)
DBUSIN_EN: P8.4, U4.20 (FB1_MC4), U22.19 (CE)
DBUSOUT_DIR: P8.3, U4.18 (FB1_MC3), U19.1 (A->B)
DBUSOUT_EN: P8.2, U4.13 (FB1_MC2), U19.19 (CE)
DI0: P1.95 (DI1_OD1), U19.2 (A0)
DI1: P1.94 (DI1_OD1), U19.3 (A1)
DI2: P1.41 (D12_OD2), U19.4 (A2)
DI3: P1.42 (D13_OD3), U19.5 (A3)
DI4: P1.91 (DI4_OD4), U19.6 (A4)
DI5: P1.92 (DI5_OD5), U19.7 (A5)
DI6: P1.93 (DI6_OD6), U19.8 (A6)
DI7: P1.43 (D17_OD7), U19.9 (A7)
DO0: P1.36 (DO0_ED0), U22.2 (A0)
DO1: P1.35 (DO1_ED1), U22.3 (A1)
DO2: P1.88 (DO2_ED2), U22.4 (A2)
DO3: P1.89 (DO3_ED3), U22.5 (A3)
DO4: P1.38 (DO4_ED4), U22.6 (A4)
DO5: P1.39 (DO5_ED5), U22.7 (A5)
DO6: P1.40 (DO6_ED6), U22.8 (A6)
DO7: P1.90 (DO7_ED7), U22.9 (A7)
DODSB*: P1.23 (DODSB*)
ED0: U22.18 (B0), U26.13 (D0), U31.2 (A0), U32.13 (D0), U34.13 (D0), U36.13 (D0), U38.13 (D0), U40.13 (D0), U42.13 (D0), U44.13 (D0)
ED1: U22.17 (B1), U26.14 (D1), U31.3 (A1), U32.14 (D1), U34.14 (D1), U36.14 (D1), U38.14 (D1), U40.14 (D1), U42.14 (D1), U44.14 (D1)
ED2: U22.16 (B2), U26.15 (D2), U31.4 (A2), U32.15 (D2), U34.15 (D2), U36.15 (D2), U38.15 (D2), U40.15 (D2), U42.15 (D2), U44.15 (D2)
ED3: U22.15 (B3), U26.17 (D3), U31.5 (A3), U32.17 (D3), U34.17 (D3), U36.17 (D3), U38.17 (D3), U40.17 (D3), U42.17 (D3), U44.17 (D3)
ED4: U22.14 (B4), U26.18 (D4), U31.6 (A4), U32.18 (D4), U34.18 (D4), U36.18 (D4), U38.18 (D4), U40.18 (D4), U42.18 (D4), U44.18 (D4)
ED5: U22.13 (B5), U26.19 (D5), U31.7 (A5), U32.19 (D5), U34.19 (D5), U36.19 (D5), U38.19 (D5), U40.19 (D5), U42.19 (D5), U44.19 (D5)
ED6: U22.12 (B6), U26.20 (D6), U31.8 (A6), U32.20 (D6), U34.20 (D6), U36.20 (D6), U38.20 (D6), U40.20 (D6), U42.20 (D6), U44.20 (D6)
ED7: U22.11 (B7), U26.21 (D7), U31.9 (A7), U32.21 (D7), U34.21 (D7), U36.21 (D7), U38.21 (D7), U40.21 (D7), U42.21 (D7), U44.21 (D7)
ERROR*: P1.98 (ERROR*)
EvenBankOE*: P10.1, U4.52 (FB3_MC11), U26.24 (OE), U32.24 (OE), U34.24 (OE), U36.24 (OE), U38.24 (OE), U40.24 (OE), U42.24 (OE), U44.24 (OE)
EvenBankWE*: P10.2, U4.53 (FB3_MC6), U26.29 (WE), U32.29 (WE), U34.29 (WE), U36.29 (WE), U38.29 (WE), U40.29 (WE), U42.29 (WE), U44.29 (WE)
EvenRAMCS0*: P10.3, U4.56 (FB3_MC15), U26.22 (CE)
EvenRAMCS1*: P10.8, U4.58 (FB3_MC17), U32.22 (CE)
EvenRAMCS2*: U4.59 (FB3_MC18), U34.22 (CE)
EvenRAMCS3*: U4.60 (FB3_MC10), U36.22 (CE)
EvenRAMCS4*: U4.61 (FB3_MC12), U38.22 (CE)
EvenRAMCS5*: U4.63 (FB3_MC13), U40.22 (CE)
EvenRAMCS6*: U4.64 (FB3_MC16), U42.22 (CE)
EvenRAMCS7*: U4.65 (FB4_MC1), U44.22 (CE)
GND: 0.1.2, C1.2, C2.2, C3.2, C4.2, C5.2, C6.2, C8.2, C9.2, C11.2, C12.2, C14.2, C15.2, C16.2, C18.2, C20.2, C21.2, C22.2, C25.2, C28.2, C29.2, C30.2, C31.2, C32.2, C37.2, C43.2, Cx1.2, Cx2.2, D18.2 (K), JP1.1, JP2.1, JP3.1, P1.50 (0_V2), P1.100 (0_V5), P4.1, P4.2, P4.3, P4.4, P4.5, P4.6, P4.7, P4.8, P5.1, P5.2, P5.3, P5.4, P5.5, P5.6, P5.7, P5.8, P9.1, P9.3, P9.5, P9.7, P9.9, P10.10, P34.1, P35.1, Q1.2 (E), Q2.2 (E), Q3.2 (E), Q4.2 (E), Q5.2 (E), Q6.2 (E), Q7.2 (E), Q9.2 (E), Q10.2 (E), Q11.2 (E), Q12.2 (E), Q13.2 (E), Q14.2 (E), Q15.2 (E), Q16.2 (E), SW2.1, SW2.2, SW2.3, SW2.4, SW2.5, SW2.6, SW2.7, SW2.8, SW3.1, SW3.2, SW3.3, SW3.4, SW3.5, SW3.6, SW3.7, SW3.8, SW4.1, SW4.2, SW4.3, SW4.4, SW4.5, SW4.6, SW4.7, SW4.8, U1.2 (GND), U2.1 (G1), U2.19 (G2), U4.21 (GND), U4.31 (GND), U4.44 (GND), U4.62 (GND), U4.69 (GND), U4.75 (GND), U4.84 (GND), U4.100 (GND), U6.1 (G1), U6.19 (G2), U7.1 (G1), U7.19 (G2), U21.16 (GND), U23.1 (G1), U23.19 (G2), U24.1 (G1), U24.19 (G2), U26.16 (GND), U27.15 (CE), U29.16 (GND), U32.16 (GND), U33.16 (GND), U34.16 (GND), U35.16 (GND), U36.16 (GND), U37.16 (GND), U38.16 (GND), U39.16 (GND), U40.16 (GND), U41.16 (GND), U42.16 (GND), U43.16 (GND), U44.16 (GND), Ux1.1 (GND)
HOLD*: P1.74 (HOLD*)
IC2_PeqQ: IC2.19 (P=Q), U4.10 (FB2_MC16)
IC2_PgrQ: IC2.1 (P>Q), U4.11 (FB2_MC15)
IC3_PeqQ: IC3.19 (P=Q), U4.12 (FB2_MC17)
IC3_PgrQ: IC3.1 (P>Q), U4.29 (FB1_MC15)
INT*: P1.73 (INT*)
MWRT: P1.68 (MWRT)
NDEF1: P1.21 (NDEF1)
NDEF2: P1.65 (NDEF2), U6.2 (A0)
NDEF2b: U4.15 (FB1_MC6), U6.18 (Y0)
NDEF3: P1.66 (NDEF3)
NMI*: P1.12 (NMI*)
unnamed: D2.1 (A), R2.2
unnamed: D2.2 (K), Q1.3 (C)
unnamed: D3.1 (A), R4.2
unnamed: D3.2 (K), Q2.3 (C)
unnamed: D4.1 (A), R6.2
unnamed: D4.2 (K), Q3.3 (C)
unnamed: D5.1 (A), R8.2
unnamed: D5.2 (K), Q4.3 (C)
unnamed: D6.1 (A), R10.2
unnamed: D6.2 (K), Q5.3 (C)
unnamed: D7.1 (A), R12.2
unnamed: D7.2 (K), Q6.3 (C)
unnamed: D8.1 (A), R15.2
unnamed: D8.2 (K), Q7.3 (C)
unnamed: D11.1 (A), R19.2
unnamed: D11.2 (K), Q9.3 (C)
unnamed: D12.1 (A), R21.2
unnamed: D12.2 (K), Q10.3 (C)
unnamed: D13.1 (A), R23.2
unnamed: D13.2 (K), Q11.3 (C)
unnamed: D14.1 (A), R25.2
unnamed: D14.2 (K), Q12.3 (C)
unnamed: D15.1 (A), R27.2
unnamed: D15.2 (K), Q13.3 (C)
unnamed: D16.1 (A), R29.2
unnamed: D16.2 (K), Q14.3 (C)
unnamed: D17.1 (A), R31.2
unnamed: D17.2 (K), Q15.3 (C)
unnamed: D18.1 (A), R35.1
unnamed: IC2.2 (P0), P6.1
unnamed: IC2.3 (Q0), SW3.16
unnamed: IC2.4 (P1), P6.2
unnamed: IC2.5 (Q1), SW3.15
unnamed: IC2.6 (P2), P6.3
unnamed: IC2.7 (Q2), SW3.14
unnamed: IC2.8 (P3), P6.4
unnamed: IC2.9 (Q3), SW3.13
unnamed: IC2.11 (P4), P6.5
unnamed: IC2.12 (Q4), SW3.12
unnamed: IC2.13 (P5), P6.6
unnamed: IC2.14 (Q5), SW3.11
unnamed: IC2.15 (P6), P6.7
unnamed: IC2.16 (Q6), SW3.10
unnamed: IC2.17 (P7), P6.8
unnamed: IC2.18 (Q7), SW3.9
unnamed: IC3.2 (P0), P7.1
unnamed: IC3.3 (Q0), SW4.16
unnamed: IC3.4 (P1), P7.2
unnamed: IC3.5 (Q1), SW4.15
unnamed: IC3.6 (P2), P7.3
unnamed: IC3.7 (Q2), SW4.14
unnamed: IC3.8 (P3), P7.4
unnamed: IC3.9 (Q3), SW4.13
unnamed: IC3.11 (P4), P7.5
unnamed: IC3.12 (Q4), SW4.12
unnamed: IC3.13 (P5), P7.6
unnamed: IC3.14 (Q5), SW4.11
unnamed: IC3.15 (P6), P7.7
unnamed: IC3.16 (Q6), SW4.10
unnamed: IC3.17 (P7), P7.8
unnamed: IC3.18 (Q7), SW4.9
unnamed: JP8.1, U7.18 (Y0)
unnamed: P9.4, R38.2
unnamed: P9.6, R36.2
unnamed: P9.10, R37.2
unnamed: Q1.1 (B), R3.2
unnamed: Q2.1 (B), R5.2
unnamed: Q3.1 (B), R7.2
unnamed: Q4.1 (B), R9.2
unnamed: Q5.1 (B), R11.2
unnamed: Q6.1 (B), R13.2
unnamed: Q7.1 (B), R18.2
unnamed: Q9.1 (B), R20.2
unnamed: Q10.1 (B), R22.2
unnamed: Q11.1 (B), R24.2
unnamed: Q12.1 (B), R26.2
unnamed: Q13.1 (B), R28.2
unnamed: Q14.1 (B), R30.2
unnamed: Q15.1 (B), R32.2
unnamed: Q16.1 (B), R33.1
unnamed: RR1.2, SW2.9, U27.6 (P7)
unnamed: RR1.3, SW2.10, U27.5 (P6)
unnamed: RR1.4, SW2.11, U27.4 (P5)
unnamed: RR1.5, SW2.12, U27.3 (P4)
unnamed: RR1.6, SW2.13, U27.14 (P3)
unnamed: RR1.7, SW2.14, U27.13 (P2)
unnamed: RR1.8, SW2.15, U27.12 (P1)
unnamed: RR1.9, SW2.16, U27.11 (P0)
OD0: U19.18 (B0), U21.13 (D0), U29.13 (D0), U31.18 (Y0), U33.13 (D0), U35.13 (D0), U37.13 (D0), U39.13 (D0), U41.13 (D0), U43.13 (D0)
OD1: U19.17 (B1), U21.14 (D1), U29.14 (D1), U31.17 (Y1), U33.14 (D1), U35.14 (D1), U37.14 (D1), U39.14 (D1), U41.14 (D1), U43.14 (D1)
OD2: U19.16 (B2), U21.15 (D2), U29.15 (D2), U31.16 (Y2), U33.15 (D2), U35.15 (D2), U37.15 (D2), U39.15 (D2), U41.15 (D2), U43.15 (D2)
OD3: U19.15 (B3), U21.17 (D3), U29.17 (D3), U31.15 (Y3), U33.17 (D3), U35.17 (D3), U37.17 (D3), U39.17 (D3), U41.17 (D3), U43.17 (D3)
OD4: U19.14 (B4), U21.18 (D4), U29.18 (D4), U31.14 (Y4), U33.18 (D4), U35.18 (D4), U37.18 (D4), U39.18 (D4), U41.18 (D4), U43.18 (D4)
OD5: U19.13 (B5), U21.19 (D5), U29.19 (D5), U31.13 (Y5), U33.19 (D5), U35.19 (D5), U37.19 (D5), U39.19 (D5), U41.19 (D5), U43.19 (D5)
OD6: U19.12 (B6), U21.20 (D6), U29.20 (D6), U31.12 (Y6), U33.20 (D6), U35.20 (D6), U37.20 (D6), U39.20 (D6), U41.20 (D6), U43.20 (D6)
OD7: U19.11 (B7), U21.21 (D7), U29.21 (D7), U31.11 (Y7), U33.21 (D7), U35.21 (D7), U37.21 (D7), U39.21 (D7), U41.21 (D7), U43.21 (D7)
OddBankOE*: P10.4, U4.54 (FB3_MC7), U21.24 (OE), U29.24 (OE), U33.24 (OE), U35.24 (OE), U37.24 (OE), U39.24 (OE), U41.24 (OE), U43.24 (OE)
OddBankWE*: P10.5, U4.55 (FB3_MC14), U21.29 (WE), U29.29 (WE), U33.29 (WE), U35.29 (WE), U37.29 (WE), U39.29 (WE), U41.29 (WE), U43.29 (WE)
OddRAMCS0*: P10.6, U4.66 (FB4_MC9), U21.22 (CE)
OddRAMCS1*: P10.9, U4.67 (FB4_MC2), U29.22 (CE)
OddRAMCS2*: U4.68 (FB4_MC5), U33.22 (CE)
OddRAMCS3*: U4.70 (FB4_MC8), U35.22 (CE)
OddRAMCS4*: U4.71 (FB4_MC3), U37.22 (CE)
OddRAMCS5*: U4.72 (FB4_MC4), U39.22 (CE)
OddRAMCS6*: U4.74 (FB4_MC11), U41.22 (CE)
OddRAMCS7*: U4.50 (FB3_MC4), U43.22 (CE)
PHANTOM*: P1.67 (PHANTOM*)
PHI: P1.24 (PHI), U5.1
PHI*: U5.2, U27.2 (CP)
POC*: P1.99 (POC*)
PWRFAIL*: P1.13 (PWRFAIL*)
RDY: P1.72 (RDY), Q16.3 (C), R34.2
RESET*: P1.75 (RESET*)
RFU1: P1.27 (RFU_1)
RFU2: P1.28 (RFU_2)
RFU3: P1.69 (RFU3)
RFU4: P1.71 (RFU4)
SDSB*: P1.18 (SDSB*)
SIXTN*: JP8.2, P1.60 (SIXTN*)
SIXTN*b: U4.9 (FB2_MC14), U7.2 (A0)
SLAVE_CLR*: P1.54 (SLAVE_CLR*)
TMA0*: P1.55 (TMA0*)
TMA1*: P1.56 (TMA1*)
TMA2*: P1.57 (TMA2*)
TMA3*: P1.14 (TMA3*)
V3.3: C31.1, C32.1, Cx2.1, JP5.2, P9.2, Ux1.2 (VOUT), Ux1.4 (VOUT)
V3.3b: JP5.1, U4.5 (VCCINT), U4.26 (VCCIO), U4.38 (VCCIO), U4.51 (VCCIO), U4.57 (VCCINT), U4.88 (VCCIO), U4.98 (VCCINT)
VCC: 0.1.1, C2.1, C3.1, C4.1, C5.1, C6.1, C8.1, C9.1, C11.1, C12.1, C14.1, C15.1, C16.1, C18.1, C20.1, C21.1, C22.1, C25.1, C28.1, C29.1, C30.1, C37.1, C43.1, Cx1.1, R2.1, R4.1, R6.1, R8.1, R10.1, R12.1, R15.1, R19.1, R21.1, R23.1, R25.1, R27.1, R29.1, R31.1, R34.1, R35.2, RR1.1 (COM), U1.3 (VO), U21.32 (VCC), U26.32 (VCC), U27.10 (Ds), U29.32 (VCC), U32.32 (VCC), U33.32 (VCC), U34.32 (VCC), U35.32 (VCC), U36.32 (VCC), U37.32 (VCC), U38.32 (VCC), U39.32 (VCC), U40.32 (VCC), U41.32 (VCC), U42.32 (VCC), U43.32 (VCC), U44.32 (VCC), Ux1.3 (VI)
VI0*: P1.4 (VIO*)
VI1*: P1.5 (VI1*)
VI2*: P1.6 (VI2*)
VI3*: P1.7 (VI3*)
VI4*: P1.8 (VI4*)
VI5*: P1.9 (VI5*)
VI6*: P1.10 (VI6*)
VI7*: P1.11 (VI7*)
WAIT: R5.1, U27.7 (~Q7)
WAIT*: P10.7, R33.2, U27.9 (Q7)
XRDY: P1.3 (XRDY)
bA0: U4.6 (FB2_MC12), U24.11 (Y7)
bA1: U21.12 (A0), U23.18 (Y0), U26.12 (A0), U29.12 (A0), U32.12 (A0), U33.12 (A0), U34.12 (A0), U35.12 (A0), U36.12 (A0), U37.12 (A0), U38.12 (A0), U39.12 (A0), U40.12 (A0), U41.12 (A0), U42.12 (A0), U43.12 (A0), U44.12 (A0)
bA2: U21.11 (A1), U23.17 (Y1), U26.11 (A1), U29.11 (A1), U32.11 (A1), U33.11 (A1), U34.11 (A1), U35.11 (A1), U36.11 (A1), U37.11 (A1), U38.11 (A1), U39.11 (A1), U40.11 (A1), U41.11 (A1), U42.11 (A1), U43.11 (A1), U44.11 (A1)
bA3: U21.10 (A2), U23.16 (Y2), U26.10 (A2), U29.10 (A2), U32.10 (A2), U33.10 (A2), U34.10 (A2), U35.10 (A2), U36.10 (A2), U37.10 (A2), U38.10 (A2), U39.10 (A2), U40.10 (A2), U41.10 (A2), U42.10 (A2), U43.10 (A2), U44.10 (A2)
bA4: U21.9 (A3), U23.15 (Y3), U26.9 (A3), U29.9 (A3), U32.9 (A3), U33.9 (A3), U34.9 (A3), U35.9 (A3), U36.9 (A3), U37.9 (A3), U38.9 (A3), U39.9 (A3), U40.9 (A3), U41.9 (A3), U42.9 (A3), U43.9 (A3), U44.9 (A3)
bA5: U21.8 (A4), U23.14 (Y4), U26.8 (A4), U29.8 (A4), U32.8 (A4), U33.8 (A4), U34.8 (A4), U35.8 (A4), U36.8 (A4), U37.8 (A4), U38.8 (A4), U39.8 (A4), U40.8 (A4), U41.8 (A4), U42.8 (A4), U43.8 (A4), U44.8 (A4)
bA6: U21.7 (A5), U23.13 (Y5), U26.7 (A5), U29.7 (A5), U32.7 (A5), U33.7 (A5), U34.7 (A5), U35.7 (A5), U36.7 (A5), U37.7 (A5), U38.7 (A5), U39.7 (A5), U40.7 (A5), U41.7 (A5), U42.7 (A5), U43.7 (A5), U44.7 (A5)
bA7: U21.6 (A6), U23.12 (Y6), U26.6 (A6), U29.6 (A6), U32.6 (A6), U33.6 (A6), U34.6 (A6), U35.6 (A6), U36.6 (A6), U37.6 (A6), U38.6 (A6), U39.6 (A6), U40.6 (A6), U41.6 (A6), U42.6 (A6), U43.6 (A6), U44.6 (A6)
bA8: P3.8, U21.5 (A7), U23.11 (Y7), U26.5 (A7), U29.5 (A7), U32.5 (A7), U33.5 (A7), U34.5 (A7), U35.5 (A7), U36.5 (A7), U37.5 (A7), U38.5 (A7), U39.5 (A7), U40.5 (A7), U41.5 (A7), U42.5 (A7), U43.5 (A7), U44.5 (A7)
bA9: P3.7, U21.27 (A8), U24.18 (Y0), U26.27 (A8), U29.27 (A8), U32.27 (A8), U33.27 (A8), U34.27 (A8), U35.27 (A8), U36.27 (A8), U37.27 (A8), U38.27 (A8), U39.27 (A8), U40.27 (A8), U41.27 (A8), U42.27 (A8), U43.27 (A8), U44.27 (A8)
bA10: P3.6, U21.26 (A9), U24.17 (Y1), U26.26 (A9), U29.26 (A9), U32.26 (A9), U33.26 (A9), U34.26 (A9), U35.26 (A9), U36.26 (A9), U37.26 (A9), U38.26 (A9), U39.26 (A9), U40.26 (A9), U41.26 (A9), U42.26 (A9), U43.26 (A9), U44.26 (A9)
bA11: P3.5, U21.23 (A10), U24.16 (Y2), U26.23 (A10), U29.23 (A10), U32.23 (A10), U33.23 (A10), U34.23 (A10), U35.23 (A10), U36.23 (A10), U37.23 (A10), U38.23 (A10), U39.23 (A10), U40.23 (A10), U41.23 (A10), U42.23 (A10), U43.23 (A10), U44.23 (A10)
bA12: P3.4, U21.25 (A11), U24.15 (Y3), U26.25 (A11), U29.25 (A11), U32.25 (A11), U33.25 (A11), U34.25 (A11), U35.25 (A11), U36.25 (A11), U37.25 (A11), U38.25 (A11), U39.25 (A11), U40.25 (A11), U41.25 (A11), U42.25 (A11), U43.25 (A11), U44.25 (A11)
bA13: P3.3, U21.4 (A12), U24.14 (Y4), U26.4 (A12), U29.4 (A12), U32.4 (A12), U33.4 (A12), U34.4 (A12), U35.4 (A12), U36.4 (A12), U37.4 (A12), U38.4 (A12), U39.4 (A12), U40.4 (A12), U41.4 (A12), U42.4 (A12), U43.4 (A12), U44.4 (A12)
bA14: P3.2, U21.28 (A13), U24.13 (Y5), U26.28 (A13), U29.28 (A13), U32.28 (A13), U33.28 (A13), U34.28 (A13), U35.28 (A13), U36.28 (A13), U37.28 (A13), U38.28 (A13), U39.28 (A13), U40.28 (A13), U41.28 (A13), U42.28 (A13), U43.28 (A13), U44.28 (A13)
bA15: P3.1, U21.3 (A14), U24.12 (Y6), U26.3 (A14), U29.3 (A14), U32.3 (A14), U33.3 (A14), U34.3 (A14), U35.3 (A14), U36.3 (A14), U37.3 (A14), U38.3 (A14), U39.3 (A14), U40.3 (A14), U41.3 (A14), U42.3 (A14), U43.3 (A14), U44.3 (A14)
bA16: P2.8, U2.11 (Y7), U21.31 (A15), U26.31 (A15), U29.31 (A15), U32.31 (A15), U33.31 (A15), U34.31 (A15), U35.31 (A15), U36.31 (A15), U37.31 (A15), U38.31 (A15), U39.31 (A15), U40.31 (A15), U41.31 (A15), U42.31 (A15), U43.31 (A15), U44.31 (A15)
bA17: P2.7, U2.12 (Y6), U21.2 (A16), U26.2 (A16), U29.2 (A16), U32.2 (A16), U33.2 (A16), U34.2 (A16), U35.2 (A16), U36.2 (A16), U37.2 (A16), U38.2 (A16), U39.2 (A16), U40.2 (A16), U41.2 (A16), U42.2 (A16), U43.2 (A16), U44.2 (A16)
bA18: P2.6, U2.13 (Y5), U21.30 (A17), U26.30 (A17), U29.30 (A17), U32.30 (A17), U33.30 (A17), U34.30 (A17), U35.30 (A17), U36.30 (A17), U37.30 (A17), U38.30 (A17), U39.30 (A17), U40.30 (A17), U41.30 (A17), U42.30 (A17), U43.30 (A17), U44.30 (A17)
bA19: P2.5, U2.14 (Y4), U21.1 (A18), U26.1 (A18), U29.1 (A18), U32.1 (A18), U33.1 (A18), U34.1 (A18), U35.1 (A18), U36.1 (A18), U37.1 (A18), U38.1 (A18), U39.1 (A18), U40.1 (A18), U41.1 (A18), U42.1 (A18), U43.1 (A18), U44.1 (A18)
bA20: P2.4, U2.15 (Y3), U4.30 (FB1_MC17)
bA21: P2.3, U2.16 (Y2), U4.32 (FB3_MC2)
bA22: P2.2, U2.17 (Y1), U4.33 (FB1_MC12)
bA23: P2.1, U2.18 (Y0), U4.35 (FB3_MC5)
pDBIN: P1.78 (pDBIN), U6.6 (A4)
pDBINb: U4.23 (I/O/GCK2), U6.14 (Y4)
pHLDA: P1.26 (pHDLA)
pSTVAL*: P1.25 (pSTVAL*)
pSYNC: P1.76 (pSYNC), U.12
pWR*: P1.77 (pWR*), U6.8 (A6)
pWR*b: U4.4 (I/O/GTS2), U6.12 (Y6)
sHLTA: P1.48 (sHLTA)
sINP: P1.46 (sINP), U6.4 (A2)
sINPb: U4.17 (FB1_MC8), U6.16 (Y2)
sINTA: P1.96 (sINTA), U6.5 (A3)
sINTAb: U4.1 (FB2_MC10), U6.15 (Y3)
sM1: P1.44 (sM1)
sMEMR: P1.47 (sMEMR), U6.9 (A7)
sMEMRb: U4.3 (I/O/GTS1), U6.11 (Y7)
sOUT: P1.45 (sOUT), U6.3 (A1)
sOUTb: U4.25 (FB1_MC7), U6.17 (Y1)
sWO*: P1.97 (sWO*)
sXTRQ*: P1.58 (sXTRQ*), U6.7 (A5)
sXTRQ*b: U4.22 (I/O/GCK1), U6.13 (Y5)

Notes on the sheet:
74LS240 INVERTER I3b/O3b
ODD BYTE RAM
EVEN BYTE RAM
SPARES
Card Ejector Mounting Holes
TO-220
pin 65 S100 bus Memory Request (active low) ~MEMRQ
A* active low MEM READ
Data INPUT from S100 Bus
Data OUTPUT to S100 Bus
C* active low MEM WRITE
B->A = A-> Y
B* active low ODD address MEM WRITE EVEN address MEM READ
XILINX CABLE HEADER 1, 3, 5, 7, 9, 11, 13 - GND 2 - VREF +3.3V 4 - TMS 6 - TCK 8 - TDO 10 - TDI 12, 14 - NC
CONFIG
DONE_LED
RDY - pin 72 S100 bus SLave drives low to tell Master to wait
pSYNC - pin 76 S100 bus
SOT233
